v5blueskyer/ESP32_appcardV2/appcardV1.2程序固件及说明（最新）/appcardV1.2/Englishfy.h

 #include <pgmspace.h>
static const char *Englishfy[7990] PROGMEM ={"v.抛弃，放弃",
"n.放弃",
"n.缩写",
"n.缓办，中止",
"v.遵守",
"n.能力",
"adj.有能力的，能干的",
"adj.反常的，变态的",
"adv.船(车)上",
"v.废除，取消",
"n.废除，取消",
"n.流产",
"adj.无效果的，失败的",
"prep.关于，大约",
"prep.在...之上，高于",
"adj.上述的",
"adv.并肩，并列",
"v.省略，摘要",
"adv.国外，海外",
"v.取消，废除",
"n.取消，废除",
"adj.突然的，生硬的",
"adv.突然地",
"n.缺席，缺乏",
"adj.缺席的，不存在",
"adj.心不在焉的",
"adj.完全的，绝对的",
"adv.绝对，完全",
"v.吸收，专心于",
"n.吸收，专注",
"adj.抽象的，难懂的",
"n.抽象，提取",
"adj.荒唐的",
"n.荒唐(事)",
"n.丰富，大量",
"adj.丰富的，充裕的",
"v.滥用，谩骂",
"n.滥用",
"adj.学院的，学术的",
"n.学院，研究院",
"v.同意",
"v.加速，加快",
"v.加速，促进",
"n.腔调v.重读",
"v.接受，同意",
"adj.可接受的，合意的",
"n.接受，承兑",
"n.接近，入口",
"adj.可接近的",
"n.附件，装饰品",
"n.事故，意外之事",
"adj.意外的，偶然的",
"adv.偶尔，附带",
"v.提供便利，拆借",
"n.便利，通融",
"n.伴侣，伴奏",
"v.伴随，伴奏",
"v.完成，达到",
"n.成就",
"v.符合，协调",
"n.按照，与...一致",
"adj.按照，据...说",
"adj.相应地，从而",
"n.账目v.说明",
"n.会计(师)",
"n.会计学",
"v.产生，发生",
"adj.增值的，应计的",
"v.积累，积蓄",
"n.积累",
"adj.积累的",
"n.准确(性)",
"adj.准确的，精密的",
"adj.准确地",
"n.控告",
"v.告发，指责",
"v.使...习惯于",
"v.觉得疼n.疼痛",
"adj.疼痛的",
"v.完成，实现",
"n.完成，成就",
"n.酸",
"v.承认，鸣谢",
"n.承认，鸣谢，回执",
"n.使熟悉，相识",
"n.熟悉人，相识",
"adj.熟悉的",
"v.求得，获得",
"n.获得",
"n.英亩",
"n.杂技演员",
"n.杂技",
"prep.横越adv.横穿",
"n.行为，法令v.表演",
"n.行为，行动",
"v.使活跃，开动",
"adj.活跃的，积极的",
"adv.积极地，活跃地",
"n.活动",
"n.男演员",
"n.女演员",
"adj.现实的，实际的",
"n.实际",
"adv.实际上，居然",
"adj.剧烈的，敏锐的",
"(缩)公元",
"n.(缩)广告",
"v.使适应，改编",
"n.适应",
"v.增添，加，补充",
"n.增加，附加物",
"adj.增加的，附加的",
"adj.附加的n.添加剂",
"n.地址v.致词",
"adj.足够的，恰当的",
"adv.恰当地",
"v.粘附，坚持",
"n.粘合剂",
"adj.邻近的",
"n.形容词",
"v.毗连",
"v.调整，修整",
"adj.可调整的",
"n.调整",
"v.管理",
"n.行政管理，管理机关",
"adj.行政管理的",
"adj.可钦佩的",
"n.羡慕，钦佩",
"v.钦佩，赞美",
"n.准入，承认",
"v.承认，接纳",
"adv.明白地",
"n.青春期",
"adj.青春期的",
"v.采用，采纳",
"n.采用",
"v.崇拜，敬慕",
"v.装饰，佩带",
"n.装饰(品)",
"n.成年人adj.成年的",
"n.v.前进",
"adj.先进的，发达的",
"n.优点，优势",
"adj.有利的，有用的",
"n.冒险，惊险活动",
"adj.冒险的",
"n.副词",
"adj.副词的",
"adj.敌手，对手",
"v.逆的，相反的",
"n.逆境，不幸",
"v.登广告，推销",
"adj.广告的",
"n.广告",
"n.忠告，意见",
"adj.适当的，可行的",
"v.劝告，通知",
"n.顾问",
"v.拥护，提倡",
"adj.天空的，航空的",
"n.飞机",
"n.事件，事情",
"v.影响，改变",
"n.友爱，爱慕",
"adj.充满感情的",
"n.分号(公司)",
"v.断言，肯定",
"n.确定，确认",
"adj.肯定的",
"v.买得起，经受得起",
"adj.买得起的",
"adj.航行中的",
"adj.上述的",
"adj.害怕的，恐怕",
"n.非洲",
"adj.非洲的n.非洲人",
"prep.在...后",
"n.下午",
"adv.后来",
"adv.再，又",
"prep.反对，对着",
"n.年龄，时代",
"n.代理，代理处",
"n.代理人，试剂",
"v.加重，恶化",
"n.加重，恶化",
"v.n.adj.合计(的)",
"n.总计，集合",
"n.侵略",
"adj.侵略的，进取的",
"n.侵略者",
"v.鼓动",
"n.鼓动，不安",
"adv....以前",
"v.使痛苦",
"n.苦恼，痛苦",
"v.同意，一致认为",
"adj.惬意的，易相处的",
"adv.欣然，依照",
"adj.商定的",
"n.一致，协议",
"adj.农业的",
"n.农业",
"adv.在...前",
"n.v.援助，救护",
"n.(缩)艾滋病",
"n.疾病",
"n.目的v.旨在，指向",
"adj.无目的的",
"n.空气，气派",
"n.航空器",
"n.航线，航空公司",
"n.定期航班",
"n.航空邮件",
"n.飞机",
"n.机场",
"n.航线",
"n.过道，走廊",
"adv.半开的",
"n.惊慌，警报",
"adj.警告的",
"int.唉，哎呀",
"n.相册，地图册",
"n.酒精",
"adj.含酒精的",
"n.嗜酒者，酒鬼",
"n.淡啤酒",
"adj.警惕的，灵活的",
"n.代数",
"adj.异国的，异样的",
"v.疏远，转让，挪用",
"n.异化",
"n.对准，准线",
"adj.相象的",
"adj.活着的，有生命的",
"adj.所有的n.一切",
"adj.过敏的，变态的",
"n.反感，过敏",
"n.联合，同盟",
"adj.同盟的",
"v.分配",
"n.分配",
"v.分配，配给",
"n.分配，份额",
"v.允许，许可",
"n.补助，津贴",
"n.合金",
"n.同盟者v.结盟",
"adv.几乎，差不多",
"adj.单独的，仅仅",
"prep.沿着adv.一起",
"prep.在...旁边",
"adv.大声地",
"n.字母表",
"adv.也",
"v.改变，变动",
"v.轮流，交替",
"n.改变，变更",
"n.v.两者取一",
"conj.虽然",
"n.高度",
"adv.全部地，总共",
"n.铝",
"adv.总是，始终",
"(缩)上午",
"adj.业余的",
"v.使惊叹",
"n.惊奇，诧异",
"n.大使",
"adj.周围的，包围着的",
"n.歧义性，意义不明处",
"adj.模棱两可的",
"n.抱负，野心",
"adj.雄心勃勃的",
"n.救护车",
"v.修改，更正",
"n.修改(通知书)",
"n.赔偿",
"n.美国，美洲",
"adj.美国的n.美国人",
"adj.和蔼的，亲切的",
"adj.友好的，和睦的",
"prep.在...之间",
"n.弹药",
"prep.在...之中",
"n.数量，总数v.合计",
"n.【电】安培",
"adj.宽大的，充裕的",
"n.放大",
"n.放大器，扩音机",
"v.详述，放大",
"v.逗乐，给娱乐",
"n.娱乐，乐趣",
"n.模拟，类似物",
"n.类似，类推",
"n.分析，分解",
"adj.分析的，解析的",
"v.分析，分解",
"n.祖先，祖宗",
"n.锚v.停泊",
"adj.古老的，古代的",
"conj.和，与，而",
"n.轶事，轶闻",
"n.天命，安琪儿",
"n.生气，愤怒",
"n.角，角度",
"adj.生气的，愤怒的",
"adj.角状的",
"n.动物",
"v.使有活力，激活",
"n.生气，生机",
"n.踝，踝骨",
"n.附录，附件",
"n.周年纪念日",
"v.宣布，通报",
"n.通知",
"n.播音员",
"v.烦扰，使生气",
"n.烦恼，麻烦事",
"adj.每年的，年度的",
"adv.每年，年年",
"pron.prep.另一个",
"n.答案v.答复",
"n.蚂蚁",
"n.对立，敌对",
"n.对手，敌手",
"adj.南极的",
"adj.抗菌的",
"n.触角，天线",
"v.期望，预料",
"n.期望，预料",
"adj.古老的n.古玩",
"n.反义词",
"adj.反义的",
"n.焦虑，担心",
"adj.焦急的，切盼的",
"adv.焦急地，急切地",
"adj.任何，一些",
"pron.任何人",
"adv.无论如何",
"pron.无论谁",
"pron.无论什么",
"adv.不管怎样",
"adv.无论何地",
"adv.分离，隔开",
"n.套房，公寓",
"n.猿猴",
"v.道歉",
"n.道歉",
"n.仪器，设备",
"adj.明显的，表面上的",
"adj.显然，似乎",
"v.n.呼吁，上诉",
"adj.有吸引力的",
"v.出现，好象",
"n.出现，外表",
"n.附录，盲肠",
"n.食欲，欲望",
"v.称赞，拍手喝彩",
"n.喝彩，欢呼",
"n.苹果",
"n.用具，器械",
"adj.生动的，适用的",
"n.申请人",
"n.申请，应用",
"v.应用，申请",
"v.任命，约定",
"n.任命，约会",
"adj.可看到的",
"adv.相当大地",
"v.欣赏，感激",
"n.欣赏，感激",
"adj.感激的",
"n.学校",
"v.通知",
"v.接近n.途径",
"adj.恰当的v.拨给",
"n.同意，批准",
"v.赞成，批准",
"adj.v.近似，约略",
"adv.近乎，大约",
"n.近似值",
"n.四月",
"adj.恰当的，易于..的",
"n.才智，天资",
"n.阿拉伯",
"n.阿拉伯人，阿拉伯语",
"adj.阿拉伯的",
"adj.专横的，任意的",
"v.仲裁",
"n.仲裁",
"n.仲裁员",
"n.弧",
"n.拱门，弓形",
"n.考古学家",
"n.考古学",
"n.建筑师",
"n.建筑学",
"adj.北极的",
"adj.热心的，强烈的",
"adj.艰巨的，努力的",
"n.地区，面积，领域",
"n.竞技场",
"v.争论，辩论",
"n.争论，论点",
"v.起来，出现",
"n.贵族阶层",
"n.贵族",
"adj.贵族的",
"n.算术",
"n.手臂，扶手v.武装",
"n.武器",
"n.手扶椅",
"n.盔甲，装甲",
"n.军队，陆军",
"adv.在周围，大约",
"v.唤醒，唤起",
"v.整理，安排",
"n.安排，计划",
"v.装扮，排列",
"n.欠款",
"v.逮捕，吸引",
"n.到达，到货",
"v.到达，达到",
"n.傲慢",
"adj.傲慢的",
"adv.傲慢地",
"n.箭，箭头",
"n.艺术，技艺",
"n.文章，物品，冠词",
"adj.人造的，假的",
"n.艺术家",
"n.艺术的",
"adv.一样prep.作为",
"v.登，上升",
"v.查明，弄清",
"v.归于",
"n.(缩)东盟",
"n.灰，灰烬",
"adj.惭愧的，羞耻的",
"adv.在岸上，上岸",
"n.烟灰缸",
"n.亚洲",
"adj.亚洲的n.亚洲人",
"adv.在旁边，搁在一边",
"v.问，要求，邀请",
"adj.睡着的",
"n.容貌，方面",
"n.阿斯匹林",
"n.驴，愚蠢的人",
"v.暗杀",
"n.暗杀",
"n.暗杀者",
"v.袭击，攻击",
"v.集合，装配",
"n.集合，装配",
"v.断言，宣称",
"n.断言",
"v.评定，估价",
"n.估值，评价",
"v.分配，指定",
"n.任务，作业",
"v.协助",
"n.协助，辅助",
"n.助手",
"v.联想adv.副的",
"adj.联合的",
"n.协会，合营",
"adj.联想的",
"adj.各种各样的",
"n.花色品种",
"v.假定，担任",
"n.假定，假装",
"n.自信，保证",
"v.使..放心，向..保证",
"adj.感到放心的",
"v.使惊讶",
"n.惊讶",
"v.使惊讶",
"adv.(信件)遗失、误传",
"n.宇宙飞行员",
"n.天文学家",
"adj.天文学的",
"n.天文学",
"prep.在，处于，以",
"n.田径运动员",
"adj.田径的",
"n.adj.大西洋(的)",
"n.地图集",
"n.大气，气氛",
"adj.大气的，空气的",
"n.原子，微粒",
"adj.原子的，原子能的",
"v.附着于，依恋",
"n.依附，附件，爱慕",
"v.n.进攻，侵袭",
"v.赢得，到达",
"v.n.尝试，企图",
"v.出席，照顾",
"n.出勤(率)，出席",
"n.随从，服务员",
"n.注意，关心",
"adj.注意的，关心的",
"adv.关心地",
"n.阁楼",
"n.态度，看法",
"n.辩护律师",
"v.吸引，引力",
"adj.有吸引力的",
"adj.归于...的",
"v.属于n.属性",
"n.属于",
"adj.定语的，属性的",
"n.拍卖",
"n.听众，观众",
"n.礼堂",
"n.八月",
"n.伯(婶、姨、姑)母",
"adj.听觉的，耳的",
"n.赞助，主办",
"n.澳大利亚",
"adj.澳大利亚的",
"n.作者，创造者",
"n.权力，权威",
"n.授权",
"v.授权，批准",
"n.自传",
"v.自动化",
"adj.自动的",
"n.自动化",
"n.汽车",
"adj.自治的",
"n.自治",
"n.秋天",
"adj.辅助的，补助的",
"v.帮助，有用n.效用",
"n.可用性，可供货",
"adj.可得到的",
"v.报复",
"n.林荫道，途径",
"adj.平均的n.平均数",
"adv.平均",
"n.航空",
"v.避免，逃避",
"v.等候，等待",
"v.醒来醒悟adj.醒的",
"adj.醒着的",
"v.授予n.奖，奖品",
"adj.知道的，意识到的",
"adv.去，远离，在远处",
"n.威惧",
"adj.可怕的",
"adj.令人畏惧的",
"adv.可怕地，非常",
"adj.笨拙的，不熟练的",
"adv.笨拙地",
"n.笨拙",
"n.斧子",
"adj.轴的，轴向的",
"n.轴，轴线，轴心",
"n.(轮)轴",
"n.婴儿，年龄最小的人",
"v.(替人)看护小孩",
"n.看护小孩的人",
"n.单身汉，学士",
"n.背adj.背后的",
"n.脊梁骨",
"v.回溯",
"n.背景，经历",
"n.倒退，支持物",
"n.未交付的订货",
"adv.向后，逆",
"n.落后(状态)",
"n.咸肉，熏肉",
"n.细菌",
"adj.坏的，低劣的",
"n.徽章",
"adv.坏，非常，严重地",
"n.羽毛球",
"v.困扰，难倒",
"n.袋子，提包",
"n.行李",
"adj.袋状的",
"n.饵，诱饵",
"v.烤，烘",
"n.面包师",
"n.面包店",
"n.平衡，天平，余额",
"n.阳台",
"adj.秃的",
"n.球，球状物，舞会",
"n.芭蕾舞",
"n.气球",
"n.热气球飞行运动",
"penn.圆珠笔",
"n.舞厅",
"n.竹",
"n.竹笋",
"n.香蕉",
"n.乐队，带子v.联合",
"n.绷带",
"n.盗匪，歹徒",
"n.v.砰的一响",
"n.岸，银行",
"n.银行家",
"n.银行业务、金融业",
"n.v.adj.破产",
"n.旗帜，横幅",
"n.宴会",
"n.棒，杆，酒吧",
"n.理发师",
"adj.裸的，直率的",
"adv.赤裸裸地",
"n.交易，便宜货",
"n.驳船",
"n.狗吠，树皮v.吠",
"n.谷仓，牲口棚",
"n.晴雨表，标记",
"n.男爵",
"n.男爵夫人，女男爵",
"n.桶，枪(炮)管",
"adj.不育的，贫瘠的",
"n.障碍，壁垒",
"n.易货贸易",
"n.基础，基地v.基于",
"n.棒球",
"n.地下室，地窖",
"adj.基本的，基础的",
"adv.基本上，主要地",
"n.盆，盆地",
"n.基础，根据",
"n.篮子，筐",
"n.篮球",
"n.球拍，蝙蝠v.击打",
"n.洗澡，浴室",
"v.洗澡，冲洗",
"n.浴室，洗手间",
"v.打击",
"n.电池",
"n.战斗，战役",
"n.海湾，湾",
"n.集市",
"(缩)公元前",
"v.是，存在",
"n.海滩，湖滨",
"n.有孔小珠",
"n.鸟嘴",
"n.梁，射线v.发光",
"n.豆子",
"v.负担，忍受，生育",
"n.举止，意义，轴承",
"adj.熊市的",
"n.野兽，牲畜",
"v.打，击败n.击打",
"adj.美丽的，绝妙的",
"n.美，美女",
"conj.因为，由于",
"v.变成",
"n.床，河床，苗圃",
"n.卧室",
"n.蜜蜂",
"n.牛肉",
"n.啤酒",
"n.甲虫",
"prep.在...前面",
"adv.事先，预先",
"v.乞讨，恳求",
"n.乞丐",
"v.开始，着手进行",
"n.初学者",
"n.开端，起点",
"n.代表",
"v.行为，举动",
"n.行为，举止",
"prep.在...后面",
"adj.落后，事后",
"n.生物，存在",
"n.信仰，信心",
"v.相信，认为",
"n.钟，铃",
"n.肚子",
"v.属于",
"adj.敬爱的n.爱人",
"adj.prep.在...下面",
"n.带，腰带",
"n.长凳，工作台",
"v.弯曲，俯身n.拐弯",
"prep.在...之下",
"adj.有益的，有利的",
"n.受益者",
"n.益处，利益",
"n.慈悲，捐助",
"adj.乐善好施的",
"adj.弯曲的",
"n.浆果",
"prep.在...之旁",
"adj.而且prep...之外",
"adj.最好的",
"n.畅销书(货)",
"adj.畅销的",
"v.赠给，授予",
"n.v.打赌",
"v.背叛，泄露",
"n.背叛，暴露",
"adj.更好的adv.较好",
"adj.经济情况较好的",
"prep.在两者之间",
"n.饮料",
"v.当心",
"v.迷惑，茫然",
"prep.在...那边，超出",
"n.偏好",
"n.圣经",
"n.自行车",
"n.v.报价，投标",
"n.投标",
"adj.大的，重大的",
"n.自行车",
"n.帐单，议案，钞票",
"n.十亿",
"v.捆绑，约束",
"n.装订",
"n.传记记者",
"n.传记",
"n.生物学家",
"n.生物学",
"n.鸟",
"n.出生，创始",
"n.生日，诞辰",
"n.出生地",
"n.饼干",
"n.主教",
"n.小片，一点",
"n.v.咬，叮n.一口",
"adj.苦的，痛苦的",
"adv.惨痛地，辛酸地",
"n.苦味，苦难",
"n.(缩)提单",
"adj.黑的n.黑色",
"n.黑板",
"n.铁匠",
"n.刀刃，叶片",
"v.责备n.过失",
"adj.空白的n.空格",
"n.毛毯",
"n.阵风v.爆炸",
"n.火光，光亮",
"v.漂白，变白",
"v.出血，流血",
"v.混合，掺混",
"v.保佑，祝福",
"n.祝福",
"adj.瞎的v.使失明",
"adj.眨眼，闪烁",
"n.大块，街区，障碍物",
"n.封锁",
"adj.金发的",
"n.血，血统",
"adj.流血的，残忍的",
"n.花v.开花",
"n.(果树的)花",
"n.污迹",
"n.女衫",
"v.吹，吹掉，刮风",
"adj.蓝色的，忧郁的",
"n.大错",
"adj.钝的，生硬的",
"v.脸红，害臊",
"adj.害羞的",
"n.木板，伙食，董事会",
"n.伙食",
"v.夸口，以...而自豪",
"n.小船，艇",
"n.身体，尸体，团体",
"n.保镖",
"v.沸腾，煮沸",
"n.锅炉",
"adj.沸腾的",
"adj.大胆的",
"n.胆略",
"n.螺检，插销v.闩门",
"n.炸弹v.轰炸",
"n.轰炸机",
"adj.真诚的，无欺的",
"n.束缚，联结，债券",
"adj.保税的",
"n.骨，骨骼",
"adj.骨头的",
"n.红利",
"n.书v.预订(票)",
"adj.定货",
"n.小册子",
"n.书橱",
"n.书架",
"n.书店",
"v.隆隆响，兴旺，繁荣",
"adj.兴旺的，繁荣的",
"v.抬高，促进",
"n.靴子",
"n.货摊，电话亭",
"n.国界，边境",
"v.烦扰，使厌烦，钻孔",
"adj.讨厌的",
"adj.出生的，天生的",
"v.借，借用",
"n.借款",
"n.X，X怀",
"n.上司，老板",
"adj.好发号施令的",
"pron.adj.双方，两",
"v.打扰，麻烦n.麻烦",
"n.瓶子",
"n.影响...的环节",
"n.底部，末尾",
"n.末行数字，结果",
"n.大树枝",
"v.跳起n.跳跃",
"v.缚，以...为界",
"n.界线，边界",
"n.资产阶级分子",
"v.鞠躬，服从n.弓",
"n.碗，钵",
"n.保龄球",
"n.箱，盒v.拳击",
"n.拳击运动员",
"n.拳击",
"n.节礼日",
"n.男孩，小伙子",
"v.n.抵制",
"n.支撑v.激励",
"n.括号",
"v.吹嘘，夸口",
"n.脑子，头脑，智能",
"n.制动器v.刹车",
"n.树枝，分支，分部",
"n.牌子，商标",
"n.白兰地",
"n.黄铜",
"adj.勇敢的v.冒着",
"adv.勇敢地",
"n.勇敢",
"n.巴西",
"adj.n.巴西的(人)",
"n.违反(契约)",
"n.面包，生计",
"n.挣钱养家的人",
"n.宽度，大量",
"n.打破，破坏n.裂口",
"n.裂口",
"n.故障，衰竭",
"n.突破",
"n.早饭",
"n.ru房，X脯",
"n.呼吸，气息",
"v.呼吸",
"v.繁殖，饲养n.品种",
"n.微风",
"v.贿赂",
"v.贿赂",
"n.砖",
"n.新娘",
"n.新郎",
"n.桥梁，桥牌",
"n.约束v.抑制",
"adj.简短的",
"n.简要情况",
"adv.简单地，简短地",
"adj.明亮的，鲜明的",
"v.使发光",
"n.光辉，明亮",
"n.辉煌，光彩",
"v.辉煌的，杰出的",
"n.边，边缘",
"v.拿来，带来",
"n.边缘",
"adj.敏捷的，活跃的",
"n.鬃毛",
"n.不列颠，英国",
"adj.英国的，英属的",
"adj.易碎的，脆的",
"adj.宽的，辽阔的",
"v.n.广播",
"n.广播节目",
"v.加宽，扩大",
"n.产品介绍手册",
"adj.破碎的，毁坏了的",
"n.经纪人",
"n.青铜",
"n.一窝",
"n.小河，溪流",
"n.扫帚",
"n.兄弟，同胞",
"n.兄弟情谊",
"n.姻兄(弟)",
"n.眉毛，额",
"n.adj.褐色(的)",
"n.青肿v.打伤",
"n.刷子，画笔v.刷",
"adj.野蛮的",
"n.禽兽，畜生",
"n.气泡",
"n.水桶",
"n.芽，蓓蕾",
"n.佛教",
"n.佛教徒",
"n.预算",
"n.水牛，野牛",
"n.冷餐",
"n.臭虫，虫子",
"n.喇叭",
"v.建造，建设",
"n.建筑工人，建设者",
"n.建筑物，大楼",
"n.球形物，灯泡",
"n.体积，大半",
"adj.庞大的，笨重的",
"n.公牛",
"n.子弹",
"n.公报",
"n.金块，金条",
"adj.行情看涨的",
"v.碰，颠簸n.碰撞",
"adj.颠簸不平的",
"n.一束",
"n.v.捆，包",
"n.担子，负担",
"adj.沉重的",
"n.局，司，办公室",
"n.官僚主义",
"adj.官僚主义的",
"n.夜盗，窃贼",
"n.盗窃",
"n.埋葬",
"v.烧，燃烧，烧伤",
"n.喷灯",
"adj.烧焦的，烧坏的",
"v.n.爆炸，破裂",
"v.掩埋，安葬",
"n.公共汽车",
"n.灌木",
"n.蒲式耳(重量单位)",
"n.行业，买卖，商号",
"adj.事务式的",
"adj.忙碌的，热闹的",
"prep.但是，除了",
"n.屠夫v.屠宰",
"n.肉食店",
"n.根端v.顶撞",
"n.黄油",
"n.蝴蝶",
"n.钮扣，按钮",
"v.买，购买",
"n.购买者",
"v.嗡嗡叫n.嗡嗡声",
"prep.在...旁边，按照",
"n.已往的，过时的",
"n.旁道，分路",
"n.副产品",
"n.出租汽车",
"n.卷心菜；圆白菜",
"n.小屋，船舱",
"n.橱柜，内阁",
"n.电缆，海底电报",
"n.咖啡馆",
"n.自助餐厅",
"n.笼子，鸟笼",
"n.糕，饼",
"v.计算，估计",
"n.计算(结果)",
"n.微积分",
"n.日历",
"n.小牛，腿肚子",
"n.刻度，核定",
"v.叫，称为，打电话",
"adj.宁静的，镇静的",
"adv.平静地，沉着地",
"n.热卡，卡路里",
"n.骆驼",
"n.照相机",
"n.帐篷，野营n.宿营",
"n.战役，运动",
"n.野营",
"n.校园",
"v.aux.能，会，可以",
"n.加拿大",
"adj.n.加拿大的(人)",
"n.运河，渠道",
"n.金丝雀",
"v.删除，取消",
"n.删除，取消",
"n.癌",
"adj.坦白的，直率的",
"n.候选人",
"n.蜡烛",
"n.糖果",
"n.手杖，(藤、竹的)茎",
"adj.罐装的",
"n.大炮",
"n.独木舟，游艇",
"n.规范，准则",
"n.食堂",
"n.帆布，画布",
"v.游说",
"n.帽子，盖子v.覆盖",
"n.才能，能力",
"adj.有能力的",
"n.容量，容积，资格",
"n.披肩，岬，海角",
"n.人",
"n.首都，资本",
"adj.资本密集型的",
"n.资本主义",
"adj.资本主义的",
"n.资本化",
"v.大写，资本化",
"n.队长，船长，上尉",
"n.标题",
"adj.被俘虏的n.俘虏",
"v.n.俘获，捉拿",
"n.小汽车",
"n.车队，大蓬车",
"n.碳，复写纸",
"n.卡片，纸牌，名片",
"n.硬纸板",
"adj.主要的",
"n.注意，小心v.关心",
"n.职业，生涯",
"adj.小心的，仔细的",
"adj.粗心的，不关心的",
"n.粗心",
"n.货物",
"n.颂歌",
"n.木匠",
"n.地毯",
"n.马车，(火车)车厢",
"n.运载工具，媒介",
"n.胡萝卜",
"v.搬运，携带",
"n.手推车",
"n.纸箱",
"n.漫画，动画片",
"n.弹仓",
"v.雕刻，切",
"n.雕塑",
"n.事实，案例，箱子",
"n.现金v.兑现",
"n.出纳",
"n.小盒，磁盘盒",
"v.掷，投射，铸造",
"n.城堡",
"adj.偶然的，随便的",
"n.伤亡",
"n.猫",
"n.(商品)目录",
"n.灾难",
"n.催化剂",
"v.捕获，染病n.捉",
"n.种类，范畴",
"v.提供",
"n.大教堂",
"adj.天主教的",
"n.牛(总称)",
"n.原因，理由，事业",
"n.谨慎，告诫",
"adj.谨慎的，当心的",
"n.骑兵，马术",
"n.洞穴，山洞",
"n.酒馆",
"n.坑，孔穴",
"v.停止，平息",
"n.天花板",
"v.庆祝",
"n.庆祝仪式",
"n.芹菜",
"n.细胞，牢房，电池",
"n.地窖，地下室",
"n.水泥",
"n.墓场",
"v.审查",
"n.审查",
"n.分币",
"adj.摄氏的",
"n.厘米",
"adj.中心的，中央的",
"n.中心v.集中",
"n.世纪",
"n.谷物",
"adj.仪式的",
"n.仪式，典礼，礼节",
"adj.确信的，一定的",
"adv.一定，当然，行",
"n.确实，必然的事",
"n.证书，执照",
"n.证明",
"v.证明",
"n.链条，一系列，锁链",
"n.椅子",
"n.主席，董事长",
"n.主席(无性别之分)",
"n.女主席，女董事长",
"n.白垩，粉笔",
"n.v.挑战，质问",
"adj.具有挑战性的",
"n.房间",
"n.优胜者，冠军",
"n.锦标(赛)",
"n.机会，可能性",
"n.变化，零钱v.改变",
"adj.变化的",
"n.沟渠，途径，频道",
"n.混乱",
"n.伙计",
"n.章，节",
"n.性格，角色，特牲",
"n.特征，特性",
"adj....特征的",
"v.具有...特征",
"n.木炭",
"v.收费，冲向，控告",
"n.施舍，仁慈",
"n.魅力v.迷惑",
"adj.迷人的",
"n.图表v.制定计划",
"n.特许证，宪章",
"v.追逐，驱除",
"v.聊天",
"v.喋喋不休，啁啾",
"adj.便宜的，可鄙的",
"v.欺骗，作弊n.骗子",
"n.欺骗行为",
"v.检验，核对n.支票",
"n.结帐，离店时限",
"n.核对，检查",
"n.颊，脸",
"adj.胖乎乎的",
"n.喝彩v.向...喝彩",
"adj.快活的",
"n.干酪，奶酪",
"adj.化学的",
"n.化学家，药剂师",
"n.化学",
"n.支票",
"v.珍爱，怀有",
"n.樱桃",
"n.国际象棋",
"n.X膛，柜子",
"n.栗树，栗子",
"v.咀嚼",
"n.小鸡",
"n.鸡，鸡肉",
"adj.首席的，首要的",
"adv.多半，首要地",
"n.孩子，儿童",
"n.童年",
"adj.孩子气的",
"adj.孩子似的，天真的",
"n.寒意v.冷却",
"adj.凉的，冷淡的",
"n.烟囱",
"n.下巴，下颊",
"n.中国",
"n.瓷器，陶瓷",
"adj.n.中国的",
"n.片，屑，缺口",
"n.巧克力",
"n.选择，选中的人或物",
"v.闷死，窒息，阻塞",
"v.选择，愿意",
"v.劈，剁n.带骨肉",
"n.合唱队，齐声",
"n.基督",
"adj.基督教的n.基督徒",
"n.基督教(精神)",
"n.圣诞节",
"n.教堂",
"n.(缩)到岸价",
"n.雪茄",
"n.卷烟",
"n.电影院",
"n.圆，果v.画圈于",
"adj.圆圈的",
"n.巡回，电路",
"v.循环，流通，流传",
"n.循环，销路，周转",
"n.周围，圆周",
"n.情况，环境",
"n.马戏团",
"v.引证，举例",
"n.公民，市民",
"n.公民权",
"n.城市",
"adj.民用的，民事的",
"n.文明，民族文化",
"v.使...文明，开化",
"v.要求，索赔，声称",
"n.夹子v.夹紧",
"v.排手，鼓掌",
"v.弄清(问题)",
"n.澄清",
"v.n.碰撞，冲突",
"n.扣子v.紧握(抱)",
"n.阶级，种类，班级",
"n.经典作品",
"adj.经典的，古典的",
"n.分类",
"v.分类，分等",
"n.同班同学",
"n.教室",
"v.咔嗒响n.卡嗒响",
"n.条款，从句",
"n.爪",
"n.黏土",
"adj.清洁的，干的",
"adj.清楚的，明确的",
"n.结关",
"adv.清晰地，无疑地",
"v.咬紧，握紧，决定",
"n.办事员，职员，店员",
"adj.聪明的，灵巧的",
"n.聪明，机灵",
"n.当事人，顾客，用户",
"n.顾客(总称)",
"n.悬崖，峭壁",
"n.气候",
"n.顶点，高潮",
"v.爬，攀登，上升",
"v.粘住，依附",
"n.诊所",
"n.夹子，卡子v.夹住",
"n.外套，借口",
"n.时钟",
"adj.adv.顺时针的",
"v.关闭，结束n.终结",
"adj.关闭的，停业的",
"n.倒闭",
"adv.紧密地，严密地",
"n.壁橱",
"n.织物，布，衣料",
"v.给...着衣",
"n.衣服(总称)",
"n.服装(总称)",
"n.云",
"adj.多云的",
"n.小丑，丑角",
"n.俱乐部，会，棍棒",
"n.线索",
"adj.笨拙的，愚蠢的",
"n.群，串",
"v.n.抓紧",
"v.(缩)请转交...",
"n.客车，教练",
"n.煤",
"adj.粗糙的，粗的",
"n.海岸，海滨",
"adj.沿海的",
"n.上衣，涂层",
"n.公鸡",
"n.鸡尾酒",
"n.法规，代码，密码",
"v.编码",
"n.系数",
"n.咖啡",
"n.棺材",
"n.凝聚性",
"adj.有条理的，粘着的",
"n.凝聚力，团结",
"adj.有粘性的",
"v.卷曲n.一卷，线圈",
"n.硬币，创造新词",
"v.重合，一致",
"n.巧合，同时发生",
"adj.同时发生的",
"adj.冷，冷冰冰的",
"n.寒冷，冷淡",
"v.协作，勾结",
"n.协作，通敌",
"v.倒塌v.坍塌",
"n.领子",
"n.同事，同行",
"v.收集，征收，聚集",
"n.收集，收藏",
"n.集体adj.集体的",
"n.学院",
"v.猛烈碰撞，冲突",
"n.猛烈碰拉，冲突",
"n.上校",
"adj.殖民的，殖民地的",
"n.殖民者，移民",
"n.殖民主义",
"n.殖民地",
"n.颜色，色彩，气色",
"adj.色盲的",
"adj.色彩丰富的",
"adj.无色的",
"n.圆柱，栏",
"n.专栏作家",
"v.梳n.梳子",
"v.n.战斗，斗争",
"n.混合，组合",
"v.组合，化合，结合",
"v.来到，出现，发生",
"n.喜剧演员",
"n.喜剧",
"n.舒适，慰藉v.安慰",
"adj.舒适的，自在的",
"adj.喜剧的，滑稽的",
"v.n.命令，控制",
"n.司令，指挥官",
"n.纪念",
"v.纪念",
"v.开始",
"v.称赞，推荐",
"n.称赞",
"n.v.评论",
"n.商业",
"adj.商业的，商务的",
"n.v.委托，委任",
"v.委托，犯(错误)",
"n.责任",
"n.委员会",
"n.商品",
"adj.共同的，普通的",
"adv.通常，平常",
"adj.平凡的，平淡的",
"n.常识",
"n.共同体，联邦",
"n.公社",
"v.传播，通讯",
"n.通信，通讯系统",
"adj.通讯的",
"n.共产主义",
"n.共产主义者",
"n.团体，共同体，群体",
"adj.严密的，紧凑的",
"n.同伴，伴侣",
"n.公司，同伴",
"adj.可比较的",
"adj.比较的，相当的",
"adv.比较地",
"v.比较，比作",
"n.比较",
"n.指南针，圆规",
"adj.可兼容的，一致的",
"v.强迫，逼迫",
"v.赔偿，补偿，酬报",
"n.赔偿，补偿",
"v.竞争，比赛",
"adj.称职的，有能力的",
"n.竞争，比赛",
"adj.竞争的",
"n.竞争能力",
"n.竞争者，对手",
"v.编(书)，编辑",
"v.抱怨，控诉",
"n.怨言，控告",
"n.补充，余数",
"v.完成，结束",
"adv.完全地，十分",
"n.完成，完满",
"adj.综合的，复杂的",
"n.复杂性",
"n.顺从，应允",
"v.使复杂",
"adj.错综复杂的",
"n.v.称赞，问候",
"adj.称赞的",
"v.履行，遵守",
"n.成分，组分",
"adj.成分的",
"v.由...组成，作曲",
"adj.镇静的",
"n.作曲家",
"adj.合成的，组合的",
"n.作文，组成",
"n.化合物v.混合",
"v.理解，了解",
"n.理解",
"adj.综合的，广泛的",
"v.压缩",
"n.压缩，凝缩",
"v.包括，由...组成",
"n.v.妥协，和解",
"v.强迫",
"adj.强制的，必修的",
"n.计算",
"v.计算",
"n.计算机",
"n.计算机化",
"v.使...计算机化",
"n.同志",
"v.隐瞒，隐藏",
"v.让步，输",
"n.自负，自大",
"adj.自负的",
"v.想象，怀孕",
"v.集中，浓缩",
"adj.全神贯注的",
"n.专心，浓度",
"n.概念",
"n.想法，概念",
"adj.概念的",
"v.涉及，关心n.商行",
"adj.有关的",
"prep.关于",
"n.音乐会",
"adj.齐心协力的",
"v.让步",
"n.让步，减免，租界",
"adj.简明的，简要的",
"v.结束，缔结，断定",
"n.结束，结论",
"adj.结束的，结论性的",
"n.混凝土adj.具体的",
"v.同地发生",
"n.合作，并发",
"adj.同时发生的",
"v.谴责，判刑",
"n.谴责，判决",
"n.凝聚",
"v.凝结，冷凝，精简",
"n.冷凝器，聚光器",
"n.状态，情形，条件",
"adj.有条件的",
"v.导致，有益于",
"adj.有助于...的",
"n.行为，管理v.为人",
"n.传导，传热",
"n.(乐队)指挥，售票员",
"n.锥体，锥形",
"v.授予，颁布，商议",
"n.会议",
"v.坦白，供认",
"n.供认，自由",
"v.委托，吐露秘密",
"n.信任，信心",
"adj.确信的，自信的",
"adj.机密的",
"v.限制",
"n.限制",
"v.证实，确认，批准",
"n.确认",
"v.n.冲突，斗争",
"v.遵守，使...一致",
"n.遵照，一致",
"v.面对，与...相对",
"n.面对，对峙",
"v.混淆，弄糊涂，搅乱",
"n.混乱，糊涂",
"n.阻塞，消化不良",
"v.祝贺",
"n.祝贺，贺辞",
"n.(代表)大会，国会",
"n.国会议员",
"n.连词，联结",
"v.连接，联想",
"n.联系，社会关系",
"v.征服，战胜",
"n.征服者，胜利者",
"n.征服",
"n.良心，良知",
"adj.有良心的",
"adv.认真地",
"adj.意识到的，自觉的",
"n.知觉，意识",
"adj.连续的，连贯的",
"v.n.同意，允许",
"n.后果，重要性",
"adv.因而，所以",
"n.保护，保存",
"adj.保守的，稳健的",
"v.考虑，以为，体谅",
"adj.相当的，可观的",
"adv.相当",
"adj.考虑周全的",
"n.考虑，照顾",
"v.委托，托运货物",
"n.委托，货物",
"v.由...组成",
"n.一致(性)",
"adj.始终如一的，符合",
"v.安慰",
"v.团结",
"adj.加固的，统一的",
"n.团结",
"adj.响亮的",
"adj.显眼的，出众的",
"n.阴谋",
"adv.警官",
"adj.不变的，恒定的",
"adv.经常地",
"adj.组成的n.成分",
"v.组成，构成，设立",
"n.宪法，章程",
"adj.宪法的，章程的",
"n.强制，拘束",
"v.建设，建立",
"n.建设，建筑",
"v.翻译，解释",
"n.领事",
"n.领事馆",
"v.咨询，磋商",
"n.咨询顾问(公司)",
"n.咨询",
"v.消费，消耗",
"n.消费者，用户",
"n.消费，消耗量",
"n.v.接触，联系",
"v.含有，容纳，抑制",
"n.容器，集装箱",
"v.沉思",
"n.苦思冥想",
"n.同时代人",
"adj.当代的，同时代的",
"n.轻视，蔑视",
"adj.轻视的",
"n.含量，内容v.满足",
"n.v.争夺，比赛",
"n.参赛人",
"n.上下文，语境，环境",
"adj.上下文的，环境的",
"adj.节制的n.大陆",
"adj.大陆的",
"n.事故，意外",
"adj.连续的，频繁的",
"n.连续",
"v.继续，连续，依旧",
"adj.持续的，不断的",
"adv.连续不断地",
"n.契约，合同v.订",
"adj.合同所规定的",
"adj.合同的，契约的",
"v.反驳，与...矛盾",
"n.矛盾，反驳",
"adj.相反的n.反面",
"n.v.对照，对比",
"v.捐献，贡献，投稿",
"n.贡献，捐献物",
"v.n.控制，管理",
"n.论战，论争",
"adj.有争议的",
"n.方便，便利",
"adj.便利的，方便的",
"n.大会，协定，惯例",
"adj.传统的，常规的",
"adj.精通的，有交情的",
"n.会话，谈话",
"v.谈话，对话，交往",
"adv.相反地",
"n.转变，转化，换算",
"v.转换，改变信仰",
"v.运输，传达",
"n.运送，传达",
"n.罪犯",
"n.定罪，确信",
"v.使...确信，信服",
"adj.信服的",
"v.烹调，烧n.厨师",
"n.厨具，厨灶",
"adj.凉的，冷静的",
"n.凉爽，冷淡",
"v.合作，协作",
"n.合作，协作",
"adj.合作的n.合作社",
"v.协调，配合",
"n.协调，配合",
"v.应付，对付",
"n.铜",
"v.抄写，复制n.副本",
"n.细绳，电线",
"adj.诚恳的，亲切的",
"adv.亲切地",
"n.核，核心",
"n.软木塞",
"n.谷物，玉米",
"n.角落，拐角",
"n.有限公司",
"n.公司",
"adj.正确的，恰当的",
"n.修改，校正",
"adv.正确地",
"v.相关，关联",
"n.相互关系",
"v.符合，通信，相当于",
"n.相应，通信",
"adj.对应的n.记者",
"adj.相应的，通信的",
"n.走廓",
"v.腐蚀",
"n.腐蚀",
"adj.腐败的，腐化的",
"n.腐败，腐化",
"n.化妆品",
"adj.宇宙的",
"n.宇宙",
"n.大都市",
"n.成本，费用v.花费",
"adj.昂贵的",
"n.村舍",
"n.棉花，棉布，棉纱",
"n.躺椅",
"v.n.咳嗽",
"n.理事会，委员会",
"n.劝告，辩护律师",
"n.顾问",
"v.计算，数，认为",
"adj.可计算的",
"n.容貌，支持",
"n.柜台adj.相反的",
"v.撤回，取消",
"n.对策",
"n.还价，还盘",
"n.同类的人或物",
"v.副署，会签",
"n.副署，会签",
"adj.无数的",
"n.国家，乡间，故乡",
"n.乡下",
"n.县，郡",
"n.一对，几个，夫妇",
"n.勇气，胆量",
"adj.勇敢的",
"n.过程，路线，课程",
"n.法庭，宫廷，球场",
"adj.有礼貌的",
"n.礼貌，礼仪，好意",
"n.院子",
"n.堂(或表)兄弟姐妹",
"v.盖，掩盖n.盖子",
"n.覆盖率",
"adj.包括的",
"n.母牛，奶牛",
"n.懦夫",
"adv.胆小地",
"n.蟹",
"v.使...破裂n.裂缝",
"n.苏打饼干，克力架",
"n.摇篮，发源地",
"n.工艺，手艺，飞机",
"n.手艺人",
"n.手艺",
"n.鹤，起重机",
"v.碰撞n.坠毁",
"n.一箱，篓，筐",
"v.渴望，恳求",
"v.爬行，徐徐行进",
"n.疯狂",
"adj.疯狂的，迷恋的",
"n.ru脂，奶油",
"adj.奶油的，奶黄色的",
"v.创造，创作，造成",
"n.创造，创造物",
"adj.有创造力(性)的",
"n.家伙，生物",
"n.信誉，信用v.相信",
"adj.有信誉的",
"n.商誉",
"n.小川，小湾",
"v.爬行，蔓延",
"n.(飞机等的)全体人员",
"n.板球，蟋蟀",
"n.罪，罪行",
"n.罪犯adj.犯罪的",
"adj.n.深红色(的)",
"n.跛子v.使残废",
"n.危险，危险期",
"adj.松脆的，鲜嫩的",
"n.评论家，爱挑剔的人",
"adj.批评的，危急的",
"n.批评",
"v.批评，评论",
"n.钩子",
"adj.弯曲的，歪的",
"n.作物，庄稼",
"n.十字，交叉v.横过",
"n.交叉，十字路口",
"n.交叉路口，十字路",
"v.蹲下，缩着",
"n.乌鸦v.鸦啼",
"n.人群v.挤满",
"n.王冠v.加冕",
"adj.未加工的，粗糙的",
"adj.残酷的，残忍的",
"n.残忍，残酷行为",
"v.巡游，巡航",
"n.面包屑",
"adj.粉碎，崩溃",
"v.压榨，粉碎",
"n.面包皮，硬的表面",
"n.拐杖",
"v.n.叫喊，哭泣",
"n.水晶，晶体",
"n.立方体，三次方",
"adj.立方的",
"n.立体主义",
"n.布谷鸟，杜鹃",
"n.黄瓜",
"v.耕作，栽培，培养",
"n.耕作，培养",
"adj.文化的",
"n.文化，养殖",
"adj.狡猾的，狡诈的",
"n.杯子，一杯",
"n.碗橱",
"v.制止，束缚",
"v.n.治疗，矫正",
"n.好奇心，古玩",
"adj.好奇的，爱打听的",
"v.卷曲，缭绕n.卷发",
"adj.卷曲的，波浪式的",
"n.通货，货币",
"adj.现令的n.流",
"adv.当前，广泛地",
"n.v.诅咒，咒骂",
"n.削减，剥夺",
"n.窗帘，幕布",
"n.曲线，弯曲",
"n.垫子，靠垫",
"n.保管，监护",
"n.风俗，习惯",
"adj.习惯的，通常的",
"n.顾客，主顾",
"n.海关",
"v.割，切，削减，切断",
"n.刀具，餐刀",
"n.刀具，裁剪者",
"n.切片，剪辑",
"n.周期，循环，自行车",
"n.自行车运动员",
"n.圆筒，柱，汽缸",
"n.(缩)承兑交单",
"n.涤纶",
"n.爸爸",
"n.匕首",
"adj.每日的adv.天天",
"adj.优雅，考究",
"n.奶牛场，ru品商店",
"n.坝",
"v.n.损害，破坏",
"v.n.诅咒",
"adj.潮湿的n.潮气",
"v.跳舞n.舞蹈",
"n.舞蹈者，舞蹈演员",
"n.危险，威胁",
"adj.有危险的",
"adj.n.丹麦人(的)",
"n.丹麦",
"v.敢，挑战，竟敢",
"adj.大胆的，勇敢的",
"adj.黑暗的n.暗处",
"v.变黑，转暗",
"n.黑暗",
"n.爱人adj.心爱的",
"n.飞标游戏",
"v.猛冲泼溅n.破折号",
"n.(复数)资料，数据",
"n.日期v.注日期",
"n.约会",
"n.女儿",
"n.儿媳",
"n.黎明，开端",
"n.一天，白天",
"n.破晓",
"n.日光，白昼",
"n.日间",
"v.耀眼，使迷乱",
"v.使...眼花缭乱",
"adj.令人目眩的",
"adj.死的n.死者",
"n.期限",
"adj.致命的，死一般的",
"adj.聋的",
"v.使...聋，震聋",
"v.处理，交易n.买卖",
"n.商人，贩子",
"n.交往，生意",
"n.系主任",
"adj.亲爱的，敬爱的",
"n.死，死亡",
"adj.致死的",
"v.n.辩论，讨论",
"n.借方",
"n.债，债务",
"n.十年",
"v.n.腐烂，衰败",
"adj.已死的",
"n.欺骗，欺诈行为",
"v.欺骗",
"n.欺诈",
"adj.欺骗性的",
"n.十二月",
"n.体面",
"adj.体面的，象样的",
"v.决定，判决",
"adj.明确的，果断的",
"adv.明确地，果断的",
"adj.十进制的，小数的",
"n.决定，决议",
"adj.决定性，明确的",
"n.甲板",
"n.宣布，宣告",
"v.宣布，声明",
"v.婉谢，推辞n.衰落",
"adj.下降的，衰落的",
"v.分解，腐烂",
"v.装饰",
"n.装饰物",
"adj.装饰的，装璜的",
"v.n.减少",
"n.法令v.判决",
"v.奉献，致力",
"v.演绎，推断",
"v.减",
"n.推断，减少",
"n.行为，契据",
"v.以为，认为",
"adj.深的，深远的",
"v.加深，深化",
"adv.深深的，深切地",
"n.鹿",
"n.v.不履行，不负责",
"v.击败n.失败",
"n.缺点，缺陷",
"adj.有缺点的",
"n.保卫，防御",
"v.保卫，为...辩护",
"v.拖延",
"n.蔑视，挑战",
"adj.无礼的，挑战的",
"n.缺乏",
"adj.缺乏的，不足的",
"n.赤字",
"v.下定义，界定，规定",
"adj.明确的，限定的",
"adv.明确地，肯定地",
"n.定义，解释",
"adv.定义的",
"v.收缩，紧缩",
"v.偏斜",
"n.偏转，偏斜",
"v.使变形，使残废",
"n.变形",
"v.支付",
"v.反抗，蔑视，使不能",
"n.降低，恶化",
"v.败低，下降，堕落",
"n.程度，度，学位",
"v.n.耽搁，延误",
"n.保付",
"n.代表n.委派",
"n.代表团",
"v.删除",
"n.删除",
"adj.故意的，审慎的",
"adv.故意地，从容地",
"n.慎重，故意",
"n.精致",
"adj.优雅的，精致的",
"adj.美味的",
"n.快乐，乐事n.喜爱",
"adj.令人高兴的",
"n.轻微犯罪",
"adj.拖欠的",
"v.交付，递送，讲述",
"n.救助",
"n.交付，递送，讲述",
"n.错觉",
"adj.令人产生错觉的",
"v.n.要求，需求",
"adj.对人要求严格的",
"n.民主，民主政体",
"n.民主党人",
"adj.民主的",
"v.拆除",
"n.拆除",
"v.论证，演示，表明",
"n.示范，表演，示威",
"n.滞期费",
"n.窝",
"n.拒绝，否定",
"v.为...命名",
"n.命名",
"v.表示",
"v.谴责，斥责",
"adj.稠密的，浓厚的",
"n.密度，稠密",
"n.牙，槽，凹陷",
"n.牙科医生",
"v.否认，拒绝",
"v.离去，出发，违反",
"n.部，部门，系",
"n.离开，违背",
"v.依靠，依赖",
"n.可依赖性",
"adj.可依赖的",
"n.受赡养者",
"n.依靠，依赖",
"adj.依靠的，随..而定",
"v.描述，描画",
"n.描述",
"v.减少，耗尽",
"v.存放，储蓄n.存款",
"n.免职，罢官",
"v.降价，贬值，折旧",
"n.折旧，贬值",
"v.抑制，使人抑郁",
"adj.情绪低落的",
"n.沮丧，萧条",
"v.剥夺，丧失",
"n.深度",
"n.代表adj.副职的",
"n.起源，衍生物",
"v.从...而来，得来",
"n.钻塔，井架",
"v.降临，下来，遗传",
"n.子孙，后裔",
"n.下降，血统",
"v.描写，作图",
"n.描述，形容",
"v.遗弃，擅离n.沙漠",
"v.应受，值得",
"v.设计，旨在n.设计",
"v.指明，指定",
"n.指定，委派",
"n.设计者",
"adj.合乎要求的",
"n.欲望，要求v.要求",
"n.课桌，写字台",
"adj.荒芜的，凄凉的",
"n.荒凉，凄凉",
"n.v.绝望",
"adj.不顾一切的",
"n.绝望",
"v.鄙视，看不起",
"prep.不管，任凭",
"n.(最后一道)甜食",
"n.终点，目的地",
"v.注定，预定",
"n.命运，定数",
"v.破坏，摧毁，消灭",
"n.破坏，毁灭",
"adj.破坏性的",
"v.分离，拆开",
"n.细节",
"adj.详细的，详尽的",
"v.留住，阻止",
"v.发现，侦察",
"n.发现，侦查",
"n.侦探",
"v.恶化，败坏",
"n.退化",
"n.决心，决定",
"v.决心，决定，测定",
"v.绕道，绕开",
"v.降低",
"n.损害",
"adj.有害的",
"n.贬值",
"v.贬值",
"v.发展，开发，成长",
"adj.发展中的",
"n.进展，发展",
"v.背离",
"n.背离，偏向",
"n.装置，方法",
"n.魔鬼，恶人",
"v.设计，计划",
"v.奉献，贡献",
"adj.献身于...的",
"n.献身，专心",
"v.吞吃，吞没",
"n.露水",
"v.诊断",
"n.诊断",
"n.图表，图解",
"n.钟盘v.拨电话",
"n.方言",
"n.对话，对白",
"n.直径",
"n.钻石，金刚石",
"n.日记",
"v.口授，命令",
"n.口授，听写",
"n.独裁者",
"n.独裁，专政",
"n.措辞",
"n.词典，字典",
"v.死，消亡",
"n.内燃机，柴油机",
"n.饮食，节食",
"v.不同，相异",
"n.差异，差别",
"adj.不同的，各种",
"adj.有差别的",
"adv.不同地",
"adj.困难的",
"n.困难，难题",
"v.挖，采掘",
"v.消化n.摘要",
"n.消化",
"n.数字",
"adj.数字的",
"n.尊贵，尊严",
"n.堤",
"v.稀释",
"adj.勤奋的，用功的",
"adj.暗淡的，模糊的",
"n.(美元)一角",
"n.维，方面，尺寸",
"adj.尺寸的",
"v.减少，缩小",
"v.用餐",
"n.餐厅",
"adj.肮脏的",
"n.正餐，晚餐，宴会",
"v.n.蘸，浸",
"n.毕业文凭，学位证书",
"n.外交",
"n.外交人员",
"n.外交的",
"v.支配，指挥，对准",
"n.方向，指示，说明",
"n.命令，指令",
"adv.直接地，立即",
"n.指导者，导演，领导",
"n.目录，地址录",
"n.尘埃，灰尘，泥土",
"adj.肮脏的",
"v.使残废",
"adj.残废的n.残疾人",
"n.不利之处",
"adj.不利的",
"v.意见不合，不符",
"n.不和，不一致",
"v.不允许",
"v.失踪，消失",
"n.消失",
"v.使...失望",
"adj.失望的，扫兴的",
"n.失望",
"n.不批准",
"n.自然灾害，祸患",
"adj.灾难性的",
"v.支付",
"n.支付",
"n.圆盘，唱片",
"v.n.丢弃，扔掉",
"v.操作别，辨明",
"v.解除，放出，卸货",
"adj.纪律的，学科的",
"n.训练，纪律n.锻炼",
"v.放弃，不承认",
"v.揭开，透露",
"n.不安，不舒服",
"adj.不舒服的",
"v.中断",
"n.v.折扣",
"v.使...泄气，阻止",
"n.演说，谈话，话语",
"v.发现",
"n.发现，发现物",
"adj.周到的，慎重的",
"adv.慎重地",
"n.单货不符",
"n.慎重",
"v.区别，岐视",
"n.辨别，岐视",
"v.讨论",
"v.讨论，商议",
"v.轻视",
"n.疾病",
"n.耻辱v.使受辱",
"adj.耻辱的，受辱的",
"v.n.伪装，掩饰",
"n.厌恶v.使讨厌",
"adj.令人生厌的",
"n.盘子，碟子",
"adj.不名誉的",
"n.耻辱v.凌辱",
"v.使觉醒，幻灭",
"adj.不愿意的",
"n.消毒剂",
"n.分散，解体",
"v.n.厌恶",
"adj.不忠的",
"adj.不忠",
"adj.阴郁的，沉闷的",
"v.使沮丧n.沮丧",
"v.解散，开除",
"n.解散，开除",
"v.不服从",
"n.紊乱，骚乱，失调",
"n.不同，悬殊",
"v.迅速派遣n.快件",
"v.驱散",
"v.分配，施予",
"v.驱散，散布",
"v.置换，取代",
"n.置换，替换物",
"v.n.陈列，表现",
"v.使生气，惹怒",
"n.不快",
"n.处置，对付",
"v.处置，对付，解决",
"adj.有...倾向的",
"n.布置，处置",
"v.争论，质疑n.争论",
"v.n.无视，不顾",
"n.不满",
"v.使不满",
"adj.不同的",
"v.驱散，消耗，浪费",
"v.溶解，使终结",
"n.距离，远处",
"adj.远方的，疏远的",
"n.蒸馏",
"adj.不同的，明显的",
"n.差别，非凡",
"adv.明晰地，清楚地",
"v.辨别，认出",
"adj.尊贵的，尊敬的",
"v.扭曲，歪曲",
"n.曲解，失真，变形",
"v.分神，迷惑",
"n.分心",
"n.苦恼，不幸",
"v.分配，分布，分销",
"n.分配，分布",
"n.分销商",
"n.分销权",
"v.区，区域，地区",
"v.打扰，打乱，使烦恼",
"n.干扰，动乱",
"v.使分裂",
"v.n.废止",
"n.沟，渠，下水道",
"n.同上",
"v.潜水，跳水，俯冲",
"n.潜水员，跳水运动员",
"v.分歧，离题",
"n.分歧",
"adj.不同的，分歧的",
"n.转移，消遣",
"n.多样化",
"v.使转向，消遣",
"v.分开，分享，分裂",
"adj.神的，神圣的",
"n.划分，部分",
"v.离婚，使脱离",
"adj.晕眩的",
"v.做，干，足够，制作",
"n.码头",
"n.医生，博士",
"n.教义，学说",
"n.文件，公文",
"adj.文化的",
"n.提供文件",
"v.躲避",
"n.狗",
"adv.顽固地",
"n.玩偶，娃娃",
"n.元，美元",
"n.领土，领域",
"n.圆顶，穹窿",
"adj.家里的，国内的",
"adj.统治的",
"v.统治，支配，占优势",
"v.捐献",
"n.捐献",
"n.驴，笨蛋",
"n.命运，判决v.命定",
"n.门，(一户)人家",
"n.门口，门道",
"n.集体宿舍",
"n.剂量，一服药",
"n.点，圆点",
"adj.两倍的，双重的",
"v.n.怀疑，疑惑",
"adj.怀疑的，可疑的",
"adv.无疑地，大约",
"n.面团",
"n.鸽子",
"adv.向下，下降",
"adv.在楼下",
"n.闹市adv.去市里",
"adj.向下的，下坡的",
"adv.向下，以下",
"v.打瞌睡",
"n.一打",
"n.草案，草稿，穿堂风",
"v.拖，拽",
"n.龙",
"v.排水，耗竭，泄",
"v.排水系统，污水",
"n.戏剧，剧本",
"adj.戏剧性的，显著的",
"n.戏剧家",
"v.使戏剧化",
"adj.激烈的，严厉的",
"v.画，拉，吸引",
"n.不利，欠缺",
"n.抽屉",
"n.素描，绘画，图样",
"v.n.恐惧，担心",
"adj.可怕的，糟糕的",
"n.梦，梦想v.做梦",
"adj.疲劳的",
"v.浸泡，充满",
"n.服装v.穿衣",
"n.打扮，调味品",
"v.漂流，游荡",
"n.钻头，操练v.训练",
"v.喝，饮n.饮料，酒",
"v.滴下，流下",
"v.驾驶，乘车n.车道",
"n.司机",
"v.下垂",
"v.落下n.滴，下降",
"n.中途退出者",
"n.旱灾",
"v.淹死",
"n.药物，麻醉剂",
"n.零食店",
"n.鼓v.敲鼓",
"adj.喝醉的",
"n.醉鬼",
"adj.干的，枯燥的",
"adj.怀疑的",
"n.鸭子",
"adj.到期的，预定的",
"n.公爵",
"adj.沉闷的，钝的",
"adv.按期地",
"adj.哑的",
"n.傀儡",
"v.倾倒n.垃圾堆",
"n.倾销",
"n.粪",
"n.地牢",
"adj.二重的，复制的",
"adj.持久的，耐用的",
"n.期间，待续时间",
"prep.在...期间",
"n.黄昏",
"n.尘土，粉末v.掸土",
"n.簸箕",
"adj.沾满灰尘的",
"n.责任，义务，关税",
"adj.免税的",
"n.矮子，侏儒",
"v.居住",
"n.居住者，住客",
"n.住宅",
"n.染料v.染色",
"adj.动力的，动态的",
"n.朝代，王朝",
"adj.adv.名，每个",
"adj.热切的，渴望的",
"n.鹰",
"n.耳朵，穗",
"n.伯爵",
"adj.早的，初期的",
"n.标记，特征",
"v.挣钱，赢得",
"adj.认真的，诚恳的",
"n.收入，赚得的钱",
"n.耳机",
"n.地球，地上，泥土",
"adj.世俗的",
"n.地震",
"n.安逸，轻易",
"adv.容易地，安逸地",
"adj.东方的n.东方",
"n.复活节",
"adj.东的，朝东的",
"adv.向东",
"adj.容易的，轻松的",
"adj.逍遥自在的",
"v.吃",
"adj.性格怪僻的",
"n.怪僻",
"n.回声，反响，共呜",
"n.(日、月)食，蚀",
"n.生态学",
"adj.经济的，经济学的",
"adj.节省的，经济的",
"adv.经济上",
"n.经济学",
"v.节省",
"n.经济，节约",
"n.狂喜",
"n.边，边缘，刀刃",
"v.校订，编辑",
"n.片(本)",
"n.编辑，编者",
"n.社论",
"v.教育",
"n.教育，训练",
"adj.教育的",
"n.鳝鱼",
"n.后果，效力v.导致",
"adj.有效的",
"adv.有效地",
"n.有效",
"n.效率，功效",
"adj.效率高的",
"n.努力，尽力，成果",
"g.(缩)例如",
"n.卵，蛋，鸡蛋",
"n.茄子",
"n.埃及",
"adj.n.埃及人(的)",
"num.八",
"num.十八",
"num.第八，八分之一",
"num.八十",
"adj.二者之一adv.也",
"v.喷射",
"n.喷射",
"v.adj.详尽阐述",
"n.详尽阐述",
"v.(时间)消逝",
"adj.弹性的，灵活的",
"n.弹性",
"n.肘，弯管",
"adj.年长的，资格老的",
"v.选举adj.当选的",
"n.选举",
"adj.电的，电力的",
"adj.电的",
"n.电工",
"n.电",
"v.充电，电气化",
"n.电子",
"adj.电子的",
"n.电子学",
"n.优雅",
"adj.优雅的，典雅的",
"n.成分，元素",
"adj.自然力的，基本的",
"adj.基础的，初步的",
"n.象",
"v.提升，抬高",
"n.海拔，提高，崇高",
"n.电梯",
"num.十一",
"num.第十一",
"v.消灭，删除",
"n.消灭，删除",
"adj.椭圆的，省略的",
"n.省略",
"n.雄辩，口才",
"adj.雄辩的，有口才的",
"adj.别的adv.否则",
"adv.在别处",
"adj.躲闪的",
"n.電子郵件",
"v.解放",
"n.解放",
"n.禁运",
"v.登陆",
"v.使窘，使为难",
"adj.令人尴尬的",
"n.窘迫，尴尬",
"n.使馆",
"v.体现，包含",
"v.拥抱，接受，包括",
"v.绣",
"v.刺绣(品)",
"v.出现，暴露",
"n.紧急情况，急诊",
"n.移居国外的人",
"v.移居国外，移民",
"n.向国外移民",
"adj.杰出的，突出的",
"n.发射，散发",
"v.发射，散发",
"n.感情，情绪",
"adj.感情的，激动的",
"n.皇帝",
"n.强调，重点，重读",
"v.强调，着重",
"adj.强调的，着重的",
"n.帝国，财团",
"adj.经验的",
"v.雇用，使用，从事",
"n.雇员",
"n.雇主",
"n.职业，就业",
"n.空虚，空白",
"adj.空的，空虚的",
"v.使能够，使可能",
"v.迷住，陶醉",
"v.环绕，包围",
"v.围住，圈起，封入",
"n.围绕，附件",
"v.面临，遭遇",
"v.鼓舞，鼓励，助长",
"n.鼓舞，鼓励",
"n.百科全书",
"n.结尾v.终止，结束",
"v.危及，危害",
"v.n.努力，尽力",
"n.结局",
"adj.无穷无尽的",
"v.背签",
"n.背书",
"v.资助，赋予，授予",
"n.忍耐力，耐用",
"v.忍受，容忍，持久",
"n.最终用户",
"n.敌人，对手",
"adj.精力旺盛的",
"n.精力，活力，能量",
"v.实施，强制",
"v.从事，雇用，吸引",
"adj.占用的，从事..的",
"n.约束，约会，婚约",
"n.发动机，火车头",
"n.工程师",
"n.工程",
"n.英格兰，英国",
"n.adj.英国的，英语",
"n.英国人",
"v.刻上，牢记",
"adj.雕刻",
"v.吞没",
"v.提高，增加",
"n.提高",
"v.欣赏，享有，享受",
"adj.愉快的",
"n.享受，乐趣",
"v.扩大，扩展，放大",
"n.扩大",
"v.启发，教导",
"adj.给人启发的",
"adj.巨大的，庞大的",
"adj.adv.足够(的)",
"v.询问",
"v.询问",
"v.使富裕",
"v.登记，招收",
"n.招收",
"adv.在途中",
"v.保证，担保，保护",
"v.遗留给，引起",
"v.进入，加入",
"n.事业，企业",
"v.招待，使欢乐",
"n.招待，娱乐",
"v.热情，热心",
"adj.热情的，热心的",
"adj.完全的，全部的",
"adv.完全地，彻底地",
"n.全部",
"v.给...权利，资格",
"n.进入，入口",
"v.恳求，请求",
"v.委托",
"n.进入，入口，词条",
"v.列举",
"v.包，围绕",
"n.信封",
"adj.嫉妒的",
"n.环境",
"adj.环境的",
"v.n.嫉妒，羡慕",
"adj.传染的n.传染病",
"n.事件，情节，插曲",
"n.时代，纪元",
"adj.划时代的",
"adj.相等的，胜任的",
"n.平等，相等",
"adv.相等地，相同地",
"n.等式，方程式",
"n.赤道",
"n.平衡，均衡",
"v.装备，配备",
"n.设备，器材，装置",
"n.相等，等值",
"adj.相等的，等值的",
"n.时代，年代",
"v.根除",
"n.根除",
"v.擦掉，抹去",
"n.抹去",
"v.树立，建立，竖立",
"n.竖立，建立",
"n.腐蚀，侵蚀",
"v.犯错误",
"n.差事，差使",
"n.错误，过失",
"v.喷发，爆发",
"n.喷发，爆发",
"n.电动扶梯",
"v.逃跑，避免，被遗忘",
"v.护送n.护卫队",
"adj.特别的，专门的",
"adv.特别地，专门地",
"n.散文，论文，小品文",
"n.散文作家",
"n.本质，情髓，香精",
"adj.必需的，本质的",
"adj.本质上，实质上",
"v.建立，设立，确立",
"adj.已建立的",
"n.建立，组织",
"n.房地产，财产",
"v.n.尊重",
"v.n.估算，预算",
"n.估算，估计",
"(缩)等等",
"adj.永恒的，无休止的",
"n.欧洲",
"n.adj.欧洲人(的)",
"v.估价，评价",
"n.估价，评价",
"v.蒸发，脱水，消失",
"n.蒸发，升华",
"n.前夕，前夜",
"adj.平坦的，均匀的",
"n.傍晚，晚上",
"adv.平坦地，均匀地",
"n.事件，场合，比赛",
"adj.多事的",
"adv.最终，终于",
"adv.曾经，总是，究竟",
"adj.永久的，持久的",
"adj.每个，所有的",
"pron.人人，每人",
"adj.每日的，日常的",
"pron.人人，每人",
"pron.事事，一切",
"adv.处处，到处",
"n.证据，迹象",
"adj.明显的，明白的",
"adv.明显地，显然",
"adj.坏的，邪恶的",
"v.发展，渐进，进化",
"v.发展，进化",
"prep.在...交货",
"adj.精确的，精密的",
"adv.确切地，正是",
"v.夸张，夸大",
"adj.言过其辞的",
"n.夸张",
"v.抬高，发扬",
"adj.高贵的，得意的",
"n.考试",
"n.检查，考试",
"v.检查，细看，考试",
"n.例子，榜样",
"v.激怒，恶化",
"n.愤慨，加剧",
"v.超过，过度",
"adv.非常，极端地",
"v.胜过，优于",
"n.优秀，卓越",
"adj.优秀的，卓越的",
"prep.除...外v.除外",
"n.除外，例外",
"adj.异常的，例外的",
"n.过量，过剩",
"adj.过分的，极度的",
"v.交换，兑换n.交易",
"v.刺激，使兴奋",
"adj.兴奋的",
"n.兴奋，激动",
"adj.令人激动的",
"v.呼喊，感叹",
"n.呼喊，感叹",
"v.排除，拒绝考虑",
"n.排除",
"adj.独有的",
"adv.独占地",
"n.独家经营权",
"n.短途游览",
"v.原谅n.借口",
"v.执行，实施，处决",
"n.执行，处决",
"adj.执行的n.执行者",
"v.举例说明",
"v.免除",
"n.锻炼，练习，运用",
"n.练习簿",
"v.尽(力)，发挥",
"n.尽力，竭力",
"v.竭尽，用完",
"adj.精疲力竭的",
"n.用尽，详述",
"adj.详尽的",
"v.展出显示n.展览品",
"n.展览会，表现",
"v.放逐n.流亡者",
"v.存在，生存",
"n.存在，生存",
"adj.现存的，已有的",
"n.出口，安全门，离开",
"v.昭雪，解除",
"n.免罪，免除",
"v.扩张，膨胀，扩充",
"n.扩张，扩大",
"v.盼望，期待，预料",
"v.期待，前程",
"n.便利，权宜之计",
"adj.方便的，临时的",
"v.加快，急送",
"n.探险，考察队",
"v.驱逐，开除",
"v.花费，消耗",
"n.支出，费用",
"n.支出，开支",
"adj.昂贵的，高价的",
"n.v.经历，经验",
"adj.有经验的",
"n.v.实验，试验",
"adj.实验的",
"n.实验",
"n.专家，能手",
"n.专家队伍(总称)",
"n.期满",
"v.到期，断气",
"n.逾期",
"v.解释，说明",
"n.说明，解释",
"adj.说明的",
"adj.清楚的，明晰的",
"adv.清晰地",
"v.爆炸，激增",
"v.开发，利用，剥削",
"n.开发，利用",
"n.勘探，考察",
"v.勘探，考察",
"n.勘探者，探险家",
"n.爆炸，爆发，激增",
"adj.爆炸性的n.炸药",
"v.n.输出，出口",
"n.出口",
"n.出口商",
"v.暴露，揭露，陈列",
"n.展览会，说明",
"n.揭露，曝光",
"v.表达，快递n.快车",
"n.表达，措辞，表情",
"adj.有表现力的",
"adj.明确表示的",
"n.高速公路",
"adj.精致的",
"v.延伸，扩大，给予",
"n.延伸，电话分机",
"adj.广泛的，密集的",
"adv.广泛地",
"n.范围，限度，一大片",
"adj.n.外部(的)",
"adj.外部的，对外的",
"adj.绝灭的，熄灭的",
"n.绝灭，熄灭",
"v.扑灭，熄灯",
"adj.额外的，外加的",
"v.取出，榨出，摘录",
"n.出身，摘要",
"n.特别的，格外的",
"n.奢侈，浪费",
"adj.奢侈的，浪费的",
"adj.极度的，极端的",
"adv.极其，非常",
"n.眼睛，孔眼，视力",
"n.眼球",
"n.眉毛",
"n.眼镜",
"n.眼睑",
"n.视力",
"n.寓言",
"n.织物，结构，组织",
"v.制作，捏造",
"n.制作，虚构",
"n.脸，正面v.面对",
"v.使便利，使容易",
"n.方便，设施，便利",
"n.事实，真相",
"n.宗派，派别",
"n.因素，因数，要素",
"n.工厂，制造厂",
"n.本领，学系",
"v.褪色，枯萎",
"n.adj.华氏(的)",
"v.失败，不及格，不能",
"adj.缺点",
"n.失败，疏忽，破产",
"adj.软弱的，模糊的",
"adj.公平的n.交易会",
"adj.公平地，相当",
"n.妖精，仙女",
"n.信任，信念",
"adj.忠诚的，可靠的",
"adv.忠诚地",
"adj.冒片的n.冒牌货",
"v.落下，跌倒n.瀑布",
"adj.假的，假造的",
"n.名声，声誉",
"n.熟悉，相似",
"adj.熟悉的，亲近的",
"n.家庭，家属",
"n.饥荒，饥饿",
"adj.著名的",
"n.扇子，...迷v.扇",
"adj.狂热的，入迷的",
"n.幻想，爱好v.想象",
"adj.奇异的，荒谬的",
"adj.遥远的adv.远",
"n.车费v.饮食",
"int.再见adj.告别的",
"n.农场，农庄",
"n.农夫，农场主",
"n.农工，农场工人",
"n.农舍",
"n.农业，种植业",
"adv.较远，更进一步",
"v.吸引，入迷，蛊惑",
"n.入迷",
"n.法西斯",
"n.法西斯分子",
"n.方式，时髦，时装",
"adj.流行的，时髦的",
"adj.快的adv.快",
"v.捆紧，钉牢",
"n.脂肪adj.肥胖的",
"adj.致命的",
"n.命运，厄运，宿命",
"n.父亲，神父，始祖",
"n.岳父，公公",
"v.领会，推测",
"n.v.(使)疲劳",
"n.缺点，过失，断层",
"adj.完美的",
"adj.有缺点的",
"n.帮助，偏爱v.宠爱",
"adj.赞成的，有利的",
"adv.有利地，顺利地",
"n.adj.最喜爱的人或物",
"國際刑警",
"n.v.害怕，担忧",
"adj.可怕的，吓人的",
"adj.毫不畏惧的",
"n.可行性",
"adj.可行的，做得到的",
"n.v.宴会，宴请",
"n.功绩",
"n.羽毛",
"n.相貌，特征，特写",
"n.二月",
"adj.联邦的",
"n.联邦",
"n.费用，酬金",
"adj.虚弱的，无力的",
"v.喂养，吃东西",
"n.反馈",
"v.感到，摸，意识到",
"n.知觉，感觉，感情",
"v.砍到",
"n.家伙，同事",
"n.交情，会员资格",
"adj.女性的，雌的",
"adj.女性的，妇女的",
"n.围栏，篱笆",
"adj.凶猛的，野蛮的",
"adj.铁的，含铁的",
"n.渡船v.渡运",
"n.渡船",
"adj.肥沃，多产的",
"n.肥料，化肥",
"adj.强烈的，热烈的",
"n.节日adj.喜庆的",
"v.去取来，去请来",
"n.纠纷，封地",
"adj.封建的",
"n.封建主义",
"n.发烧，狂热",
"adj.少的n.少数",
"n.纤维，质地",
"n.小说，虚构",
"adj.虚构的",
"n.提琴",
"n.田野，战场，场",
"adj.凶猛的，猛烈的",
"adj.火的",
"num.十五",
"num.第五，五分之一",
"num.五十",
"n.无花果",
"v.打仗，战斗，作斗争",
"n.战士",
"adj.比喻的，修饰的",
"n.数字，图形，人物",
"n.档案，纵列，锉刀",
"n.档案管理",
"v.装满，充满，补缺",
"n.充填物，馅",
"n.胶片，电影，薄膜",
"n.滤器v.过滤",
"n.污秽，污物",
"adj.污秽的",
"adj.最终的n.决赛",
"v.落实，定下来",
"adv.最终，终于",
"n.金融v.资助",
"adj.金融的，财政的",
"n.金融家",
"n.金融业，财政学",
"v.寻找，找到，发现",
"n.发现，发现物",
"adj.好的，精细的",
"n.手指",
"v.n.结束，抛光",
"adj.制成的",
"adj.有限的，限定的",
"n.裘皮",
"n.火，火灾v.开火",
"n.消防车",
"n.消防队员",
"n.壁炉",
"n.焰火",
"adj.坚固的n.商号",
"adv.坚定地，坚固地",
"n.坚定，坚固",
"adj.第一的adv.首先",
"adj.第一流的",
"n.鱼v.捞取，探听",
"n.渔夫",
"n.渔业",
"n.裂变，分裂",
"n.拳头",
"adj.适合的，健康的",
"n.适合，健康",
"adj.适当的",
"num.五",
"v.固定，确定，修理",
"adj.固定的，已确定的",
"n.固定物，固定装置",
"n.旗",
"n.片，片状物",
"n.火焰，热情",
"n.侧面，胁腹",
"n.法兰绒",
"v.拍打n.垂下物",
"v.n.闪烁",
"n.v.闪光，闪现",
"n.瓶，烧瓶",
"adj.平的，平淡的",
"v.弄平，变平",
"v.奉承，谄媚",
"n.滋味，风趣",
"n.裂缝，瑕疵，缺点",
"v.逃走，消散",
"n.羊毛",
"n.船队",
"n.肌肉，骨肉，果肉",
"adj.肉的",
"n.柔韧，灵活性",
"adj.柔韧的，灵活的",
"v.闪烁",
"n.飞，航班，逃走",
"v.抛，掷",
"v.浮，漂n.彩车",
"n.群v.群集",
"n.洪水，大量",
"n.地板，(楼)层",
"n.面粉",
"v.茂盛，兴旺",
"v.流动n.流动，流量",
"n.花，盛期",
"n.流感",
"v.波动，起伏",
"n.波动",
"n.流利，流畅",
"adj.流利的",
"n.液体adj.流动的",
"v.(脸)发红n.红晕",
"n.长笛，笛子",
"v.飘动，振翼",
"n.流动，变迁",
"v.飞，驾机n.苍蝇",
"n.泡沫v.起泡",
"(缩)离岸价",
"n.焦点，中心v.集中",
"n.饲料",
"n.敌人，宿敌",
"n.雾，翳",
"adj.有雾的，雾蒙蒙的",
"v.折叠n.折痕",
"n.叶子(总称)",
"n.人们，乡亲，亲属",
"v.跟随，听懂，遵循",
"n.追随者，信徒",
"adj.下列的，其次的",
"n.adj.后续(的)",
"adj.喜爱..的，慈爱的",
"n.食物，食粮",
"n.食品",
"n.蠢人，傻瓜v.愚弄",
"n.愚蠢的，笨的",
"n.脚，英尺，最下部",
"n.足球",
"n.立足点，立场",
"n.足迹，脚步声",
"prep.给，作...用的",
"v.禁止，不许",
"adj.禁止的",
"n.力，力量v.强迫",
"adj.前面的adv.在前面",
"n.v.预测，预报",
"n.祖先，先辈",
"n.食指",
"adj.先行的，上述的",
"n.前额",
"adj.外国的，对外的",
"n.外国人，异乡人",
"n.领班",
"adj.最初的，第一流的",
"v.预见，预知",
"n.森林",
"n.林业",
"v.预告，预言",
"adv.永远，总是",
"v.打铁，锻造，伪造",
"n.锻炉，锻造厂",
"v.忘记，疏忽，没想到",
"v.饶恕，原谅，豁免",
"n.餐叉，岔口",
"n.形状，类型，表格",
"adj.形式上的，正式的",
"n.礼节，正式",
"n.格式，样式",
"n.形成，构成",
"adj.以前的，前者",
"adv.从前，以前",
"adj.可怕的，难对付的",
"n.公式",
"v.系统阐述",
"n.确切表述",
"v.遗弃，抛弃",
"n.堡垒，要塞",
"adv.向前，向外",
"adj.即将到来的",
"n.坚毅",
"n.两星期",
"n.堡垒，城堡",
"n.偶然事件",
"adj.幸运的，侥幸的",
"adv.幸运地，幸而",
"n.运气，财富",
"num.四十",
"n.讨论会，座谈会",
"adj.向前的adv.向前",
"n.化石，守旧者",
"v.养育，抚养",
"adj.肮脏的，邪恶的",
"v.创办，使有根据",
"n.建立，基金，基础",
"n.创办人，奠基人",
"n.泉，源泉，喷泉",
"num.四",
"num.十四",
"num.第四，四分之一",
"n.家禽，鸡，禽肉",
"n.狐狸，狡猾的人",
"n.片断，分数",
"adj.零碎的，不足的",
"n.断裂v.折断",
"adj.易碎的，脆的",
"n.碎片，片断",
"n.芬芳，香气",
"adj.香的，芬芳的",
"adj.脆弱的，虚弱的",
"n.框架，骨骼v.构造",
"n.构架，机构",
"n.法国",
"n.特许权",
"adj.坦率的，真诚的",
"adv.坦率地",
"adj.自由的，空闲的",
"n.自由，免除",
"adv.自由地，随意地",
"v.结冰，楞住，冻结",
"n.冷冻箱",
"n.货运，货物，运费",
"adj.法国的n.法语",
"n.法国人",
"n.频繁，频率",
"adj.频繁的，经常的",
"adv.时常，往往",
"adj.新鲜的，崭新的",
"v.使新鲜，使振作",
"n.新人，新生",
"v.使烦恼n.烦燥",
"n.摩擦，摩擦力",
"n.星期五",
"n.朋友",
"adj.友好的，和气的",
"n.友谊，友好",
"n.恐怖，惊吓",
"v.惊吓，吓唬",
"adj.令人害怕的",
"adj.可怕的",
"n.边缘，花边，穗子",
"n.女上衣，童上装",
"n.蛙",
"prep.自，从...来",
"n.正面，前线v.面对",
"n.边界，国境，新领域",
"n.霜，霜冻",
"adj.霜的",
"v.皱眉头，厌恶",
"adj.节俭的",
"n.果子，水果，成果",
"adj.果实累累的",
"v.阻挠，使灰心",
"n.挫折，灰心",
"v.油煎，炸",
"n.煎锅",
"渾蛋，辱駡",
"n.燃料",
"v.完成，满足要求",
"n.完成，成就",
"adj.满的，完全的",
"adv.完全，彻底",
"v.摸索",
"n.娱乐，玩笑，乐趣",
"n.作用，集会，函数",
"adj.功能的",
"n.基金，资金，蕴藏",
"adj.基本的，根本的",
"n.葬礼",
"adj.有趣的，好笑的",
"n.毛皮，裘衣",
"adj.狂怒的，狂暴的",
"n.熔炉",
"v.供应，装备，摆家具",
"n.家具(总称)",
"n.犁沟",
"adv.更远，进一步",
"adv.而且",
"n.狂暴，狂怒",
"n.保险丝，导火线",
"n.忙乱，大惊小怪的",
"adj.爱大惊小怪的",
"n.将来，前途",
"n.期货",
"v.获得，赢得n.收益",
"n.大风，定期交付",
"n.美术馆",
"n.加仑",
"v.奔驰，飞跑",
"v.n.赌博，投机",
"n.赌徒",
"n.游戏，比赛，猎物",
"n.一群，一帮",
"n.匪徒，歹徒",
"n.监狱",
"n.空隙，隔阂，山口",
"n.车库，汽车修理站",
"n.垃圾",
"n.花园，菜园",
"n.园丁",
"n.园艺",
"n.大蒜",
"n.衣服，服装",
"n.要塞，警备队",
"n.气体，煤气，汽油",
"n.汽油",
"v.n.喘息，喘气",
"n.大门，门票收入",
"v.聚集，收集，采集",
"n.集会，聚集",
"n.规格，计量表",
"adj.快活的，快乐的",
"v.n.凝视，注视",
"n.齿轮，用品",
"n.宝石",
"adj.一般的，总的",
"n.概括",
"v.总结，归纳",
"adv.通常，大概",
"v.产生，发生，生殖",
"n.世代，一代人",
"n.发电机",
"n.慷慨，大方",
"adj.慷慨的，丰盛的",
"n.天份，才华，天才",
"adj.温柔的，温和的",
"n.绅士，先生，君子",
"adv.轻轻地，温柔地",
"adj.真正的，道地的",
"n.地理学，地形",
"n.地质学",
"n.几何学",
"n.萌芽，起源，细菌",
"adj.德国的n.德语",
"n.德国",
"n.姿势，手势，姿态",
"v.获得，记住，到达",
"n.集会，聚会",
"n.鬼魂，幽灵",
"n.巨人adj.巨大的",
"n.礼品，天赋",
"adj.巨大的",
"v.咯咯地笑",
"n.姜",
"n.少女，姑娘",
"v.给予，付出n.让步",
"adj.快乐的，高兴的",
"v.看一眼n.一瞥",
"n.v.闪耀，瞪眼",
"n.玻璃，镜子",
"n.玻璃制品",
"n.微光，闪光",
"v.n.滑行，溜",
"v.n.瞥见",
"v.闪光",
"v.闪闪发光",
"adj.全世界的，总的",
"n.全球化",
"v.使...全球化",
"n.地球，球体，地球仪",
"n.黑暗，忧郁",
"adj.阴沉的，忧郁的",
"adj.光荣的，辉煌的",
"v.颂扬，赞美",
"n.光荣，壮丽，荣誉",
"n.词汇表",
"n.手套",
"v.发光，发红",
"n.胶水n.粘贴",
"n.供过于求v.狼吞虎咽",
"v.啃，咬",
"n.(缩)国民总收入",
"v.去，进行，打算",
"n.目标，目的，球门",
"n.山羊",
"n.神，上帝",
"n.女神",
"n.黄金，金币，金色",
"adj.黄色的，金黄色的",
"n.高尔夫球",
"adj.好的，善良的",
"int.再见",
"adj.好看的",
"n.优良，天哪",
"n.你方",
"n.货物，商品",
"n.商誉",
"n.鹅",
"n.咽喉，峡谷，山口",
"adj.绚丽的，了不起的",
"n.大猩猩",
"n.闲谈，聊天",
"v.统制，支配，决定",
"n.编制，政体，政府",
"n.女家庭教师",
"n.州长，总督",
"n.长袍，法衣",
"v.抓住，攫取",
"n.优美，文雅，恩惠",
"adj.优美的，文雅的",
"adj.亲切的，客气的",
"n.等级，年级",
"adj.逐渐的，逐步的",
"adv.逐渐地，逐步地",
"v.毕业生v.毕业",
"n.毕业",
"n.谷物，颗粒，一点点",
"n.克",
"n.语法",
"adj.语法的",
"n.留声机",
"adj.雄伟的，重大的",
"n.(外)孙儿、女",
"n.孙女，外孙女",
"n.祖父，外祖父",
"n.祖母，外祖母",
"n.(外)祖父(母)",
"n.孙子，外孙",
"n.花岗石",
"v.答应，授予，承认",
"n.葡萄",
"n.图象，图解",
"v.n.抓住，领悟",
"n.草，禾本植物",
"n.蚱蜢",
"adj.感激的，致谢的",
"v.使满足，使高兴",
"adj.可喜的",
"adj.免费的",
"n.感激，感谢",
"adj.严肃的，庄重的",
"n.砂砾，石子",
"n.引力，严肃",
"v.吃草，擦碰",
"v.润滑油脂",
"adj.大的，伟大的",
"adj.大大地，非常地",
"n.伟大，大",
"n.希腊",
"n.贪婪，贪心",
"adj.贪婪的",
"n.adj.希腊人(的)",
"adj.绿的，没有经验的",
"n.蔬菜商",
"n.温室",
"v.打招呼",
"n.问候，致意",
"adj.灰色的，阴郁的",
"n.悲哀，悲伤",
"v.使悲伤，伤心",
"adj.冷酷的，不祥的",
"v.露齿而笑",
"v.碾碎，磨快，折磨",
"v.n.紧握，吸引",
"vn.呻吟",
"n.杂货铺",
"n.杂货店",
"n.槽，沟，常规",
"v.摸索，探索",
"adj.总的，粗糙的",
"n.地面，场，根据",
"adj.无根据的",
"n.群，组，团体",
"n.林子，树丛",
"v.增长，成长，种植",
"v.n.咆哮，嗥叫",
"adj.已长成的",
"n.成人adj.成人的",
"n.增长，发展，生长",
"v.嫉妒，吝啬",
"v.抱怨，咕哝，发牢骚",
"n.v.(作)呼噜声",
"n.v.保证，担保",
"v.警卫，提防v.哨兵",
"n.保护人",
"v.n.猜想，推测",
"n.客人，宾客，旅客",
"n.宾馆",
"n.向导，指导",
"v.向导，指引n.导游",
"n.犯罪，过失",
"adj.有罪的，内疚的",
"n.吉它，六弦琴",
"n.海湾，鸿沟",
"v.吞下",
"n.树胶，口香糖，牙龈",
"n.枪，炮",
"n.火药",
"n.一阵(大风)",
"n.街沟",
"n.家伙",
"n.体育馆，健身房",
"n.体操",
"n.体操运动员",
"n.习惯",
"adj.习惯的，惯常的",
"adj.消瘦的，憔悴的",
"n.争论，讨价还价",
"v.欢呼n.冰雹",
"n.头发，毛发",
"n.理发",
"n.美发",
"n.发卡",
"adj.毛发的，多毛的",
"n.一半adv.一半",
"adv.半途",
"n.大厅，会堂",
"n.标志",
"v.n.停住",
"v.对分，减半",
"n.火腿",
"n.汉堡包",
"n.锤子v.锤击",
"v.妨碍",
"n.手，人手，指针",
"n.手袋，手提包",
"n.手册",
"adj.一把，少量",
"n.障碍v.妨碍",
"adj.有残疾的",
"n.手帕，手绢",
"v.处理，对待n.把",
"n.处理，管理",
"adj.漂亮的，得体",
"n.分发物(印刷品等)",
"n.手写，书法，笔迹",
"adj.方便的，近便的",
"v.挂，垂，绞死",
"n.衣架",
"adj.偶然的",
"v.发生，碰巧，出事",
"n.事件",
"adv.幸运地",
"n.幸福",
"adj.高兴的，幸运的",
"n.港口，停泊处",
"adj.硬的adv.努力",
"v.硬化，变硬",
"adv.刚刚，几乎不",
"n.坚硬，硬度",
"n.困苦，艰难",
"n.硬件",
"adj.勤劳的",
"adj.耐劳的，耐寒的",
"n.野兔",
"n.v.损害，伤害",
"adj.有害的",
"adj.无害的，无恶意的",
"adj.和睦的，和谐的",
"n.融洽，和谐",
"v.支配，治理",
"adj.刺耳的，严厉的",
"v.n.收获",
"n.急忙，急速",
"v.赶紧，加快",
"adj.急促的，草率的",
"n.帽子",
"v.孵化，策划",
"v.恨，憎恶，不愿意",
"adj.可恨的，可憎的",
"n.憎恶，敌意",
"adj.傲慢的",
"v.拉，拖n.获得量",
"v.萦绕，作崇",
"v.有，不得不，拿",
"n.鹰隼",
"n.干草",
"n.危险",
"pron.他",
"n.头，领导v.率领",
"n.头疼，头疼的事",
"n.标题",
"n.通栏标题",
"ad.头向前地，卤莽地",
"n.(中、小学)校长",
"n.司令部，总部",
"v.治愈，医治",
"n.健康(状况)",
"adj.健康的",
"n.一堆，许多v.堆积",
"v.听见，听取，听说",
"n.听力，审讯",
"n.心，心肠，中心",
"adj.衷心的",
"n.壁炉，炉边",
"adv.精神饱满的",
"adj.衷心的，热诚的",
"n.热，热烈v.加热",
"n.激烈的，热烈的",
"n.取暖，供热",
"v.起伏，举起，叹气",
"n.天空，天堂",
"adv.重，沉重的",
"adj.星的，繁重的",
"n.树篱，套期保值",
"n.刺猬",
"v.n.注意，留心",
"n.后跟",
"n.高度，顶点",
"v.加高，增加",
"n.继承人",
"n.女继承人",
"n.直升飞机",
"n.地狱，苦境",
"int.喂，你好",
"n.头盔",
"v.n.帮助，有助于",
"adj.有用的",
"adj.无用的，无效的",
"n.半球，领域",
"n.母鸡",
"adv.因此，由此",
"adv.今后",
"pron.她的，她(宾格)",
"n.先兆，先驱",
"n.药草",
"adj.草药的",
"v.放牧n.(牲畜)群",
"adv.这里，在这里",
"adv.此后",
"adv.以此",
"adv.在此",
"adv.以下",
"adv.在本文件中",
"adv.对此",
"adv.与此一道",
"n.英雄，男主角",
"adj.英雄的，英勇的",
"n.女英雄，女主角",
"pron.她自己",
"adj.犹豫的",
"v.犹豫，不想",
"n.犹豫，踌躇",
"int.嗨",
"int.嗨，你好",
"v.躲藏，隐瞒，掩盖",
"adj.骇人听闻的",
"adj.高的，高度的",
"n.高地",
"adv.十分，赞许地",
"n.公路",
"v.拦路抢劫",
"n.栏路抢劫者",
"n.v.徒步郊游",
"n.小山，丘陵",
"n.山坡，山腰",
"pron.他(宾格)",
"pron.他自己",
"adj.后面的，后部的",
"v.妨碍，阻止",
"n.内地",
"n.障碍(物)",
"n.合页，绞链",
"n.暗示，迹象v.暗示",
"n.臀部",
"v.租，雇佣",
"pron.他的",
"v.n.(发)嘶嘶声",
"n.历史学家",
"adj.历史性的",
"adj.历史的",
"n.历史",
"v.打，碰，打击",
"v.搭车旅行",
"adv.迄今，到那时",
"adj.嘶哑的，沙哑的",
"n.嗜好，业余爱好",
"n.锄头v.锄",
"v.升起，扯起",
"v.握住，容纳n.控制",
"n.持有人，支架",
"n.支持，控股",
"n.停顿，耽误",
"n.洞，孔穴",
"n.节日，假日",
"adj.空心的，凹陷的",
"adj.神圣的，圣洁的",
"n.家，故乡adv.回家",
"adj.无家可归的",
"adj.家常的，简便的",
"n.思乡的",
"n.家庭作业",
"adj.同质的，同类的",
"adj.诚实的，正直的",
"n.诚实，正直",
"n.蜂蜜",
"n.蜜月",
"n.荣誉，名誉v.尊敬",
"adj.可尊敬的，体面的",
"n.钩v.钩住",
"v.跳跃",
"v.n.希望，愿望",
"adj.有希望的",
"adv.可以指望",
"adj.无望的，绝望的",
"n.地平线，视野",
"adj.水平的，横的",
"n.角，触须，号角",
"adj.可怕的，糟透的",
"v.使恐惧",
"n.恐惧，恐怖",
"n.马",
"n.马力",
"n.软水管，长统袜",
"n.医院",
"adj.好客的",
"n.好客，款待",
"n.一大群，男主人",
"n.人质",
"n.廉价旅馆",
"n.女主人，女主持人",
"adj.怀敌意的",
"adj.热的，辣的",
"n.热狗(面包)",
"n.旅馆",
"n.旅馆业",
"n.小时，点钟",
"n.猎狗v.追逐",
"n.房子，剧场，家",
"n.户adj.家庭的",
"n.看门人，保姆",
"n.家庭主妇",
"n.家务",
"v.翱翔，盘旋，徘徊",
"adv.如何，多么，怎样",
"adv.可是，然而",
"v.n.嚎叫，嚎哭",
"v.n.紧抱",
"adj.庞大的，巨大的",
"n.豆荚，外壳，船壳",
"v.哼，嗡嗡叫",
"adj.人的，人类的",
"adj.人慈的",
"n.人道主义",
"n.慈善家",
"n.人类，人性",
"adj.谦卑的，卑贱的",
"adj.湿的，潮湿的",
"n.湿度，湿气",
"v.使受辱",
"n.羞辱，耻辱",
"n.幽默(感)，心情",
"adj.幽默的，诙谐的",
"num.一百",
"num.第一面，百分之一",
"n.饥饿，渴望",
"adj.饥饿的，渴望的",
"v.打猎，搜索，寻找",
"n.猎人，搜索者",
"v.猛掷，猛投",
"int.好哇n.喝彩声",
"v.赶紧，急忙，急运",
"v.使受伤，使痛，伤害",
"n.丈夫",
"int.嘘n.沉默",
"v.奔忙",
"n.小屋",
"adj.水力的，液压的",
"adj.水电的",
"n.氢，氢气",
"n.卫生",
"n.赞美诗，赞歌",
"n.伪善",
"n.假设，前提",
"adj.假设的",
"n.歇斯底里，癔病",
"adj.亢奋的",
".我",
"n.冰，冰块",
"n.冰淇淋",
"adj.冰封的",
"n.冰岛",
"adj.冰冷的，结了冰的",
"n.思想，主意，打算",
"adj.理想的n.理想",
"n.理想主义",
"v.使理想化",
"adj.同一的，相同的",
"n.识别，身分",
"v.认出，认为...一致",
"n.认同，同一性",
"n.习语，成语",
"adj.习语的，惯用的",
"n.傻子，白痴",
"adj.空闲的，懒的",
"n.闲散，无所事事",
"n.偶像，被崇拜的人",
"(缩)即，也就是",
"conj.如果，虽然是否",
"v.点燃",
"n.无知，不知道",
"adj.不知道的，无知的",
"v.忽视，不理睬",
"adj.患病的，坏的",
"adj.不合法的，非法的",
"adj.字迹不清的",
"n.文盲",
"adj.文盲的n.文盲",
"n.疾病，生病",
"v.照亮，启发",
"n.幻想，幻觉",
"adj.幻觉的",
"v.图解，用图说明",
"n.阐明，实例",
"n.图像，影像，形象",
"adj.想象的，虚构的",
"n.想象力，想象",
"v.想象，猜想",
"v.模仿，仿造，模拟",
"n.模仿，仿制品",
"adj.无形的，不重要的",
"adj.不成熟的",
"adj.立即的，最近的",
"adv.立即，马上",
"adj.巨大的，极大的",
"v.浸泡，埋头于",
"n.移民",
"v.移入",
"n.移居入境",
"adj.迫切的，危急的",
"adj.不道德的",
"adj.不朽的",
"n.冲击，影响",
"v.给予，告诉",
"adj.公证的",
"n.不耐烦",
"adj.急切的，不耐烦的",
"adj.绝对必要的",
"adj.不完善的",
"n.帝国主义",
"n.帝国主义者",
"v.实行n.工具",
"n.实行，执行",
"n.暗示，含义",
"adj.暗含的，暗示的",
"v.恳求，哀求",
"v.暗示，意味",
"v.进口引进n.进口货",
"n.重要性，意义",
"adj.重要的，重大的",
"n.进口",
"n.进口商",
"v.征(税)，强加",
"n.强迫接受",
"n.不可能性",
"adj.不可能的，不妥的",
"n.进口税，关税",
"v.不可行的",
"v.印，铭刻，产生印象",
"n.印象，影响，印迹",
"adj.给人深刻印象的",
"v.关押，监禁",
"n.监禁，徒刑",
"adj.不适当的",
"v.改善，提高",
"n.改善，好转",
"n.冲击，冲动，脉搏",
"n.不纯，杂质",
"prep.在...内，穿戴",
"n.无能",
"adj.很难得到的",
"adj.不准确的，不确切",
"adj.不充足的，不足以",
"adv.因为，由于",
"adj.开幕的",
"v.举行开幕、就职典礼",
"n.开幕、就职典礼",
"adj.不能的，不会的",
"v.使发怒n.香",
"n.刺激的，鼓励的",
"n.英寸",
"n.事件，事变，插曲",
"adv.偶然地，另外",
"n.倾斜，倾向",
"v.低头，喜欢，倾斜",
"adj.倾向于...的",
"v.包括",
"n.包括在内",
"adj.包括在内的",
"n.收入，所得",
"n.不兼容",
"adj.不相容的",
"adj.不完全的，没完成",
"n.不一致",
"adj.不一致的",
"n.不便，不利",
"adj.不方便的",
"v.合并，体现",
"adj.有限的",
"adj.不正确的",
"n.(缩)国际贸易术语",
"v.n.增加，增长",
"adj.不断增长的",
"adv.日益，越来越",
"adj.不可信的，惊人的",
"adj.表示怀疑的",
"n.增值",
"v.招致，承受",
"adj.感激的，感恩的",
"n.感激",
"adv.的确，实际上",
"adj.不明确的，不确定",
"adv.不明确地",
"v.赔偿，保护",
"v.(书写)缩行",
"n.独立，自主",
"adj.独立的",
"adv.独立地",
"n.索引，标志，指数",
"n.印度",
"adj.n.印度人(的)",
"v.指明，表示",
"n.表示，迹象",
"adj.表示...的",
"n.冷淡，不关心",
"adj.冷淡的，不在乎的",
"n.消化不良",
"adj.气愤的，愤慨的",
"n.愤慨，气愤",
"adj.间接的，侧面的",
"adj.间接地",
"adj.必不可少的",
"adj.个人的，各自的",
"adj.室内的",
"adv.在户内，在屋里",
"v.诱使，引起，归纳",
"n.诱导，动机",
"n.感应，归纳",
"v.放纵，放任，纵容",
"adj.工业的",
"v.使工业化",
"n.工业化",
"adj.工业化的",
"adj.勤劳的，勤奋的",
"n.工业，产业，勤奋",
"adj.效率低的",
"n.低效率",
"n.无效力",
"adj.无效的",
"n.惯性，惰性，不活动",
"adj.必然的，不可避免",
"adv.必然地",
"adj.便宜的",
"n.婴儿，幼儿",
"n.步兵",
"v.感染，传染",
"n.感染",
"adj.传染的",
"v.推断，推论",
"n.推断，推论的结果",
"adj.低级的n.下级",
"n.劣势",
"adj.无限大的，无穷的",
"adv.无限地，无穷地",
"adj.不定式的",
"n.无限，无数，极多",
"adj.不易燃的",
"n.充气，通货膨胀",
"v.打击",
"n.影响，势力(范围)",
"adj.有影响的",
"n.流行性感冒",
"v.通知，告诉，告密",
"adj.非正式的",
"n.通知，情报，资料",
"adj.提供资料的",
"adj.不经常的",
"v.侵权",
"n.侵权",
"adj.灵巧的，精巧的",
"adj.独创的，机智的",
"n.灵巧，机灵，巧妙",
"v.居住，栖身",
"n.居民",
"adj.生来俱有的",
"v.继承，遗传",
"adj.最初的",
"adv.最初",
"v.发动，开始，使入门",
"n.积极性，首创精神",
"v.注射",
"n.注射",
"v.伤害，损害",
"n.伤害，损害",
"n.不公正",
"n.墨水，油墨",
"n.内地的，内陆的",
"n.水湾，入口",
"n.客栈",
"adj.里面的，内心的",
"n.清白，天真",
"adj.无罪的",
"v.革新，变革，创始",
"n.革新，创新",
"adj.无数的",
"adj.无机的",
"n.输入，投入",
"v.询问",
"n.询问，查询，调查",
"adj.疯狂的",
"n.昆虫",
"v.插入，嵌入",
"n.插入",
"n.里面adj.里面的",
"n.知情者",
"n.洞察力",
"adj.无足轻重的",
"v.坚持，坚决要求",
"adj.紧迫的，坚持的",
"adv.在...范围内",
"adj.无偿付能力的",
"v.检查，视察，审查",
"n.检查，视察",
"n.检查员，视察者",
"n.灵感",
"v.鼓舞，激励，受启发",
"adj.不稳定的",
"v.安装，安置",
"n.安装，装置",
"n.分期付款",
"n.例子",
"adj.立即的，速溶的",
"adv.立即，立刻",
"adv.代替，而是",
"n.本能，直觉，天性",
"adj.本能的，天性的",
"n.(专科)学院v.建立",
"n.机构，制度",
"v.指导，指示，告知",
"n.指导，指示",
"adj.指示的，教育的",
"n.教员，教练",
"n.仪器，乐器，手段",
"adj.仪器的，工具的",
"adj.不充足的",
"v.绝缘，隔离，使孤立",
"n.隔离，绝缘",
"v.adj.侮辱",
"n.保险(业)，保障",
"v.保险，确保",
"adj.无形的",
"adj.组成的，整体的",
"v.整合，结合",
"n.结合，整体",
"n.完整性，诚实",
"n.理智，才智",
"n.知识分子",
"n.智慧，情报",
"adj.聪明的，明智的",
"v.打算",
"adj.强烈的，极度的",
"n.强烈，强度",
"adj.强化的，密集的",
"n.意图adj.专心的",
"n.意图，目的",
"adj.有意的，故意的",
"v.相互作用，相互影响",
"n.相互作用",
"n.交流，往来",
"n.兴趣，利息，利益",
"adj.感兴趣的",
"adj.有趣的",
"n.交界，接口",
"v.妨碍，干涉",
"n.干涉，干扰",
"n.内部，内地，内政",
"adj.中间的",
"adj.内部的，国内的",
"adj.国际的",
"n.国际化",
"v.使国际化",
"v.解释，当...译员",
"n.解释，口译",
"n.译员",
"v.打断，中断",
"n.中断，打扰",
"n.间隔，中间休息",
"v.介入，调解",
"n.v.会见，面谈",
"adj.亲密的，熟悉的",
"n.亲密，熟悉",
"prep.到...里面，..成",
"n.语调，声调",
"v.介绍，引进，采用",
"n.介绍，引言",
"adj.介绍的，入门的",
"v.侵入，强加于",
"adj.使充满",
"v.入侵，侵犯",
"n.入侵者",
"adj.伤残的，无效的",
"v.使无效",
"adj.非常宝贵的",
"adv.不变地，总是",
"n.侵略，侵袭",
"v.发明，创造，编造",
"n.发明，创造",
"n.发明者",
"adj.相反的，倒转的",
"adv.相反地",
"v.投资，花费",
"v.调查，研究",
"n.调查",
"n.投资(额)",
"adj.看不见的",
"n.邀请(信)",
"v.邀请，招致，征求",
"n.发票，装货清单",
"v.使卷入，忙于",
"adj.涉及的，复杂的",
"n.卷入，涉足",
"adj.里面的，内心的",
"adv.向内的",
"n.爱尔兰iIrishn.adj.爱尔兰人(的)",
"n.铁，熨斗v.熨平",
"adj.反讽的，讽刺的",
"n.反讽，讽刺",
"adj.不规则的",
"n.不规则",
"adj.不可抗拒的",
"adj.不论，不考虑",
"adj.不可撤消的",
"v.灌溉",
"n.灌溉",
"v.使生气，刺激",
"n.刺激，恼怒",
"n.伊斯兰教，回教",
"n.岛屿",
"v.隔离，孤立",
"n.隔离，孤立状态",
"v.发行发布n.发行物",
"pron.它",
"n.adj.意大利人(的)",
"n.意大利",
"v.n.痒，热望",
"n.条款，项目",
"v.分列",
"pron.它的",
"pron.它自己",
"n.象牙，象牙色",
"n.千斤顶，船首旗",
"n.短外套，茄克衫",
"n.监狱v.监禁",
"n.果酱，阻塞",
"n.一月",
"n.日本",
"n.adj.日本人(的)",
"n.罐子，坛子，刺耳声",
"n.下颚，下巴",
"n.爵士乐",
"n.妒忌",
"adj.妒忌的",
"n.牛仔裤",
"n.果冻",
"n.吉普车",
"v.危及",
"n.颠簸，猛推",
"n.耶稣",
"v.喷射v.喷气发动机",
"n.投弃货物v.抛弃",
"n.犹太人",
"n.珠宝，宝石",
"n.珠宝(总称)",
"adj.犹太人的",
"v.n.(发)叮当声",
"n.工作，活儿，差使",
"adj.失业的",
"v.慢跑",
"v.连接，加入，参加",
"n.接着，关节",
"n.笑话v.开玩笑",
"v.匆匆记下",
"n.刊物，日志",
"n.新闻体",
"n.记者",
"n.旅行，旅程",
"n.高兴，乐事",
"adj.令人高兴的",
"n.法官，裁判v.审判",
"n.判决，意见，判断",
"n.大壶，罐",
"n.汁，液",
"adj.多汁的",
"n.七月",
"n.搞乱，混乱",
"v.n.跳跃，跳动",
"n.连接，结合处，接头",
"n.六月",
"n.密林，热带丛林",
"adj.年少的，低级的",
"n.木屋",
"n.陪审团，评奖团",
"adv.只，刚才",
"n.公正，正直",
"adj.有理由的",
"n.辩护，正当理由",
"v.认为...有理",
"adj.青少年的",
"n.带鼠",
"adj.锋利的，敏捷的",
"v.保持，保留，防止",
"n.保管人，管理员",
"n.一致，协调",
"n.核(仁)，核心",
"n.煤油",
"n.水壶",
"n.钥匙，关键，答案",
"n.键盘",
"n.钥匙孔",
"v.n.踢",
"n.小孩v.哄骗",
"v.绑架，诱拐",
"n.绑架者",
"n.肾，腰子",
"v.杀死，杀害",
"n.杀人者，杀手",
"n.(缩)公斤，公里",
"n.公斤",
"n.公里",
"n.千瓦",
"n.种类adj.仁慈的",
"n.幼儿园",
"v.点燃，激发",
"adv.仁慈地，好心地",
"n.仁慈，好意",
"n.国王",
"n.王国",
"v.接吻，亲嘴",
"n.全套工具、装备",
"n.厨房",
"n.风筝",
"n.膝",
"v.跪下",
"n.小刀",
"n.骑士，爵士",
"v.编织，皱(眉)",
"n.球形把手",
"v.敲，击倒n.敲门声",
"n.结，树节v.打结",
"n.知道，认识，懂",
"n.专项技术，诀窍",
"n.知识，学识",
"adj.博学的",
"n.(缩)实验室",
"n.标签v.标明",
"n.实验室",
"n.劳动，劳动力",
"n.劳工，劳动者",
"adj.劳动密集型的",
"n.花边，鞋带",
"v.n.缺少",
"n.少年，小伙子",
"n.梯子，阶梯",
"n.女士，贵妇人，夫人",
"v.n.落后，滞后",
"n.湖，湖泊",
"n.羔羊，小羊肉",
"adj.跛的，站不住脚的",
"n.灯",
"n.陆地，土地v.着陆",
"adj.卸货的",
"n.楼梯平台，着陆",
"n.女房东",
"n.房东，地主",
"n.风景(画)，地形",
"n.小巷，跑道，行车道",
"冷甲(馬來西亞霹靂洲内一地方名)",
"n.语言",
"n.灯笼",
"n.膝盖",
"v.(时间)流失",
"adj.大的，巨大的",
"adv.大部分，基本上",
"n.云雀，百灵鸟",
"n.激光",
"adj.最后的adv.上次",
"adj.持久的，持续的",
"adj.迟到的，晚的",
"adv.近来，最后",
"adj.潜伏的，潜在的",
"adv.更晚，以后，过后",
"adj.横向的，侧向的",
"n.车床",
"n.adj.拉丁语(的)",
"n.纬度，活动余地",
"adj.后面的，后者的",
"n.结构，点阵",
"v.笑，嘲笑",
"n.笑，笑声",
"v.发射，发动，开始",
"n.洗衣店，送洗的衣物",
"n.盥洗室，厕所",
"n.法律，定律",
"adj.合法的，法律的",
"n.草地，草坪",
"n.律师，法学家",
"v.放，安排，打基础",
"n.装卸日期",
"n.层，层次",
"n.设计，规划，图案",
"n.懒惰",
"adj.懒惰的",
"n.(缩)信用证",
"v.引导，领先，率领",
"n.领导，领袖",
"n.领导",
"adj.领先的，一流的",
"n.叶子，页",
"n.传单，单页宣传品",
"n.同盟，协会",
"v.漏，泄漏",
"n.渗漏",
"v.俯身，倚adj.瘦的",
"v.n.跳跃adj.闰年的",
"v.学习，获悉",
"adj.有学问的",
"n.学习者，学生",
"n.学问，学习",
"v.租凭，出租n.租约",
"adj.最少的",
"n.皮革adj.皮革制的",
"v.出发，离开n.休假",
"n.v.演讲，讲课",
"n.演讲者，讲师",
"adj.活动余地",
"adj.左的adv.向左",
"adj.左手的，左侧的",
"n.剩余物",
"n.腿，裤脚",
"adj.合法的，法律的",
"n.传说，传奇",
"adj.传说的，传奇的",
"n.立法，法规",
"adj.合法的，合理的",
"n.合法",
"n.闲暇，闲空",
"n.柠檬",
"n.柠檬汽水",
"v.出借，贷款",
"n.贷款，借款",
"n.长度，期限",
"v.延长，变长",
"n.列宁主义",
"n.透镜，镜片，晶体",
"n.豹",
"adj.更少的adv.较小",
"v.减少，变小，变弱",
"n.功课，课程，教训",
"prep.唯恐，以免",
"v.让，使",
"n.字母，信，函件",
"n.水平，级v.弄平",
"n.杠杆",
"v.征税n.关税",
"n.责任，义务，债务",
"adj.有责任的",
"n.说谎者",
"adj.思想开放的",
"v.解放，释放，使自由",
"n.解放",
"n.自由",
"n.图书管理员",
"n.图书馆，藏书",
"n.许可(证)，执照",
"v.舔",
"n.盖，脸",
"v.躺，位于v.n.说谎",
"n.中尉，副职",
"n.生活，生命，一生",
"n.一生",
"v.举起，吊n.电梯",
"n.光，灯adj.明亮的",
"v.发亮，使...愉快",
"n.打火机",
"n.灯塔",
"adv.轻轻地，轻易地",
"n.闪电",
"v.喜欢prep.像",
"n.可能，相似性",
"adj.可信的adv.很可能",
"n.相像，类似",
"adv.同样，照样",
"n.兴趣，嗜好",
"n.百合，睡莲",
"n.肢，树枝",
"n.石灰",
"n.石灰岩",
"n.界限，限度v.限制",
"n.限制，局限",
"adj.有限的，限定的",
"n.豪华轿车",
"adj.柔软的v.跛行",
"n.行，线条，界线",
"adj.线性的，线状的",
"n.亚麻(织物)",
"n.班轮，班机",
"v.徘徊，逗留，拖延",
"n.语言学者",
"n.语言学",
"n.夹里，衬里",
"v.联系，连结n.纽带",
"n.狮子",
"n.母狮子",
"n.嘴唇",
"n.口红，唇膏",
"n.液体adj.液体的",
"n.烈性酒",
"n.表，名单v.列表",
"v.听，听从",
"n.听者",
"n.识字",
"adj.字面的，不夸张的",
"adv.简直，字面上",
"adj.文学的",
"n.有文化的",
"n.文学，文献",
"n.公升",
"v.乱丢废物n.废物",
"adj.小的，一点，少的",
"v.居住生存adj.活的",
"n.生活",
"adj.活跃的，热闹的",
"n.肝",
"n.牲畜",
"adj.活着的n.生计",
"n.客厅，起居室",
"n.负载，负担v.装载",
"n.面包v.游荡",
"n.贷款v.出借",
"n.前厅v.游说",
"n.龙虾",
"adj.地方的，当地的",
"n.地点，现场",
"v.找出，确定地点",
"n.地点，位置",
"v.锁上n.锁，绺",
"n.锁，固定资本",
"n.火车头，机车",
"n.蝗虫",
"v.寄宿",
"n.住处，住房",
"adj.崇高的，高耸的",
"n.原木，航海日志",
"n.逻辑，论理学",
"adj.逻辑的",
"n.孤独，寂寞",
"adj.孤独的，寂寞的",
"adj.寂寞的",
"adj.长的adv.长久",
"n.长寿",
"n.渴望，思慕",
"n.经度，经线",
"adj.长期的",
"v.看，看上去n.外表",
"v.隐隐出现n.织布机",
"n.环，回路v.环绕",
"adj.松的，自由自在的",
"v.解开，放松",
"n.君主，贵族，上帝",
"n.卡车，载重汽车",
"v.失去，丢失，输",
"n.丧失，失利，损失",
"adj.失去的",
"n.许多，地adv.相当",
"n.抽彩，抓阄，彩票",
"adj.响亮的，大声的",
"n.响亮",
"n.扬声器，扩音器",
"n.休息室",
"adj.可爱的",
"v.爱，喜欢n.爱情",
"adj.好看的，可爱的",
"n.爱人，情人，爱好者",
"adj.低的，低廉的",
"v.降低，减弱",
"adj.忠诚的，忠贞的",
"n.忠诚，忠贞",
"v.润滑",
"n.润滑",
"n.运气，幸运",
"adj.幸运的",
"n.行李",
"n.木材，木料",
"adj.发光的，明晰的",
"n.块，肿块",
"n.总数",
"adj.月亮的，阴历的",
"n.午饭，便餐",
"n.午餐，午宴",
"n.肺",
"adj.豪华的，奢侈的",
"n.奢侈(品)",
"n.机器",
"n.机械(总称)",
"n.雨衣",
"n.宏观经济学",
"adj.疯狂的，狂热的",
"n.夫人，太太，女士",
"nn.疯子",
"n.疯狂，疯病",
"n.杂志，期刊",
"n.魔法，魔术，魅力",
"n.魔术师",
"n.地方法官",
"n.磁性，磁铁",
"adj.磁性的",
"n.磁性，磁力，吸引力",
"adj.壮丽的，宏伟的",
"v.放大，扩大",
"n.宏大，重要(性)",
"n.女仆，侍女",
"n.少女adj.未婚的",
"n.邮件v.邮寄",
"n.信箱",
"adj.主要的",
"n.大陆，本土",
"adv.主要地，大部分",
"n.主流",
"v.维持，保养，坚持",
"n.保养，维修",
"n.玉米",
"n.陛下，雄伟，庄严",
"adj.主要的，多数的",
"n.多数，过半数",
"v.做，制造n.种类",
"n.制造者，制造商",
"adj.临时的n.权宜之计",
"n.气质，化妆品",
"n.病",
"n.疟疾",
"n.马来西亚",
"n.马来西亚",
"adj.男性的，雄的",
"n.恶意，恶感",
"adj.恶意的",
"n.人，男人，人类",
"v.管理，处理，设法",
"n.管理(人员)，经营",
"n.经理",
"adj.管理的",
"n.男子气",
"v.表明adj.明白的",
"n.表明",
"n.宣言",
"v.操纵，操作，摆布",
"n.操纵，操作",
"n.人类",
"adj.大丈夫的",
"n.方法，方式，礼貌",
"n.宅第，官邸，大厦",
"adj.用手的n.手册",
"v.n.制造",
"adj.制成的",
"n.制造商",
"n.手稿，原稿",
"adj.许多的n.许多",
"n.地图v.筹划",
"n.枫树",
"n.大理石，弹子",
"n.三月",
"n.v.行进，行军",
"n.余地，边缘",
"adj.边缘的，边际的",
"adj.海的，海生的",
"n.海员，水手",
"n.痕迹，符号，标记",
"adj.有标记的，标明的",
"n.市场，销路",
"adj.有销路的",
"n.市场学，营销学",
"n.市场，集市",
"n.唛头，标记",
"n.婚姻，婚礼",
"adj.已婚的",
"v.娶，嫁，为...主婚",
"n.火星",
"n.沼泽",
"n.元帅",
"n.烈士，殉道者",
"n.奇迹v.惊奇",
"adj.奇异的，绝妙的",
"n.马克思主义",
"n.马克思主义者",
"adj.男性的，阳性的",
"n.假面具v.掩饰",
"n.堆，大量，群众",
"n.v.屠杀，残杀",
"n.按摩，推拿",
"adj.粗大的，厚重的",
"median.传媒工具，新闻界",
"n.桅杆",
"n.主人，大师，硕士",
"n.杰作",
"n.垫子，席子",
"n.火柴，对手，比赛",
"n.伙伴v.配对",
"n.材料，资料，原料",
"n.唯物主义",
"v.使具体化，物质化",
"adj.数学的",
"n.数学",
"n.数字家",
"n.(缩)数学",
"n.日场演出",
"n.事情，物资，毛病",
"n.床垫",
"adj.成熟的，到期的",
"n.成熟，到期",
"v.增加到最大程度",
"n.最大量，极限",
"n.五月",
"v.可以，也许，祝愿",
"adv.或许，大概",
"n.市长",
"pron.我(宾格)",
"n.牧场，草地",
"n.膳食，一顿饭",
"v.打算，意指",
"n.意义，意图",
"n.手段，财力",
"adv.同时，在这期间",
"adv.n.在这期间",
"n.尺寸，量具，措施",
"n.测量(结果)",
"n.肉",
"n.技工",
"adj.机械的、机动的",
"adv.机械地",
"n.力学，机械学",
"n.机制，机械装置",
"n.奖章，勋章，纪念章",
"adj.医学的，医务的",
"n.药，医学",
"adj.中世纪的",
"v.考虑，沉思",
"n.考虑，沉思冥想",
"n.地中海",
"n.中间，媒介，中庸",
"adj.温顺的",
"v.遇到，会见，迎接",
"n.会议，集会",
"n.adj.忧郁(的)",
"n.旋律，曲调",
"n.瓜，甜瓜",
"v.熔化，融解",
"n.成员，会员",
"n.会员资格，全体成员",
"n.备忘录",
"n.回忆录",
"adj.纪念的，追悼的",
"v.记住，记忆",
"n.记忆(力)，回忆",
"v.n.威胁，恐吓",
"v.修理，修补，好转",
"adj.心理的，精神的",
"n.心理，意识",
"v.n.提及，讲到",
"n.菜单",
"n.商品，货物",
"n.商人adj.商业的",
"n.商品",
"adj.仁慈的，宽大的",
"n.水星",
"n.汞，水银",
"n.宽大，慈悲，怜悯",
"adj.仅仅的，起码的",
"adv.仅仅，只",
"v.合并",
"n.价值，功绩v.应得",
"n.美人鱼",
"adj.欢乐的",
"n.网孔，筛眼",
"n.肮脏，凌乱v.弄脏",
"n.音讯，消息",
"n.通讯员，使者",
"n.金属",
"adj.金属的",
"n.冶金学",
"n.量器，仪表",
"n.方法",
"n.方法(论)",
"adj.小心翼翼的",
"adv.胆小地",
"n.米，公尺",
"adj.公制的，米的",
"n.大都市",
"n.adj.墨西哥人(的)",
"n.墨西哥",
"n.微观经济学",
"n.扩音器，话筒",
"n.微处理机",
"n.显微镜",
"n.微波",
"n.正午，晌午",
"n.当中adj.中部的",
"n.中人，中间人",
"n.中等的，第二流的",
"n.午夜",
"n.中间，中部",
"v.或许，可以n.力",
"adj.强有力的",
"adj.迁移的，候鸟的",
"v.迁移(海外)，移栖",
"n.迁移，移居海外",
"adj.温和的，味淡的",
"n.英里",
"n.里程",
"n.里程碑",
"adj.军事的，好斗的",
"n.民兵(组织)",
"n.奶，ru夜v.挤奶",
"n.送奶人",
"adj.加奶的，ru白色的",
"n.磨坊，工厂v.滚乱",
"n.磨坊主",
"n.毫米",
"n.百万",
"n.百万富翁",
"v.切碎，绞碎",
"n.粉碎机",
"n.头脑，智力v.介意",
"pron.我的n.矿山",
"n.矿工",
"n.矿物adj.矿物的",
"v.混合，混入",
"n.雏形，缩影，袖珍",
"n.微型计算机",
"v.使减到最小",
"n.最少量adj.最小的",
"n.教士，部长，大臣",
"n.(政府)部",
"adj.较小的，次要的",
"n.少数，少数民族",
"n.造币厂，薄荷",
"prep.减去adj.减的",
"n.分钟，片刻",
"n.奇迹，令人惊讶的事",
"adj.奇迹(般)的",
"n.镜子v.反映",
"n.未到目的地",
"v.未运到(目的地)",
"n.伤害，恶作剧",
"n.吝啬鬼，守财奴",
"adj.悲惨的，糟糕的",
"n.痛苦，悲惨，苦难",
"n.不幸",
"n.疑虑，担心",
"v.装卸不慎",
"n.事故",
"v.误解",
"v.引入岐途",
"v.未击中错过n.小姐",
"n.导弹，发射物",
"adj.丢失的，缺少的",
"n.使团，使命，天职",
"n.传教士",
"n.薄雾v.使迷糊",
"n.错误，误解v.搞错",
"adj.搞错了的，误解的",
"n.先生(缩写为Mr.)",
"n.女主人，情妇",
"adj.雾蒙蒙的，有雾的",
"v.误解，误会",
"n.误会，曲解",
"n.连指手套，露指手套",
"v.混合，配料，交往",
"n.混合器",
"n.混合物，混和",
"v.n.呻吟，悲叹",
"n.暴民，乌合之众",
"adj.机动的，流动的",
"v.动员",
"v.嘲笑，愚弄",
"n.方式，方法",
"n.模范，模型，模特儿",
"adj.适度的v.缓和",
"adv.适度地，适中地",
"adj.现代的，时髦的",
"n.现代化",
"v.使...现代化",
"adj.谦虚的，质朴的",
"n.谦虚",
"n.修改，缓和",
"adj.改良的，改进的",
"v.修改，减轻，修饰",
"v.调整，改变",
"n.模量，模件",
"adj.潮湿的",
"n.潮气",
"adj.分子的",
"n.分子",
"n.时刻，瞬间",
"adj.片刻的，瞬间的",
"adj.重要的，重大的",
"n.君主，王室",
"adj.修道院，寺院",
"n.星期一",
"adj.货币的，金融的",
"n.金钱，货币，财富",
"n.班长监视器v.监视",
"n.和尚，修道士",
"n.猴子",
"v.垄断，独占",
"n.垄断，独占",
"adj.单调的，枯燥的",
"n.单调，枯燥",
"n.怪兽，怪物，魔鬼",
"adj.可怕的，极恶的",
"n.月份",
"adj.每月的n.月刊",
"n.纪念章，不朽之物",
"adj.纪念碑式的",
"n.心情，心境，情绪",
"n.月亮",
"n.月光",
"n.业余干活",
"v.系泊，把船栓定",
"n.拖把，墩布",
"adj.道德的n.教训",
"n.士气，斗志",
"n.道德品质",
"adj.更多的更adv.更",
"adv.此外，而且",
"n.早晨，上午",
"adj.致命的",
"n.adj.穆斯林",
"n.清真寺",
"n.蚊子",
"n.苔藓，地衣",
"adj.最多的adv.非常",
"adv.主要地，大多",
"n.汽车旅馆",
"n.蛾",
"n.母亲adj.出生地的",
"n.岳母，婆婆",
"n.运动，议案",
"adj.不动的",
"v.促进，激发",
"n.动机",
"n.动机",
"n.发动机",
"n.汽车",
"n.摩托车",
"n.摩托车手",
"n.汽车道，高速公路",
"n.座右铭",
"n.模子，型，霉菌",
"n.山，岳v.登上",
"n.山",
"adj.多山的，山一般的",
"v.悲悼，哀痛",
"adj.悲悼的，哀痛的",
"n.哀痛",
"n.老鼠",
"n.胡子，须",
"n.口，嘴巴，河口",
"n.一口，满口",
"v.移动，推动，搬家",
"n.活动，运动，动作",
"n.电影(院)",
"n.(缩)先生",
"n.(缩)夫人，太太",
"n.(缩)女士",
"adj.许多的n.许多",
"n.泥浆",
"adj.泥泞的",
"v.裹住，捂住",
"n.围巾，消音器",
"n.(有柄)大杯",
"n.骡子",
"adj.复合的，多次方的",
"n.乘法，增加",
"v.乘，增加，繁殖",
"n.多功能的",
"n.大批，大群",
"adj.市的，市政的",
"v.咕哝，嘟囔",
"n.腮腺炎",
"v.",
"",
"n.凶手，杀人犯",
"v.低声说",
"n.筋，肌肉",
"adj.肌肉发达的",
"v.沉思，默想",
"n.博物馆，陈列馆",
"n.“蘑菇",
"n.音乐，乐曲",
"adj.音乐的n.歌舞片",
"n.音乐家，作曲家",
"v.必须，准是n.必须",
"n.芥末",
"adj.缄默的n.哑巴",
"v.咕哝，抱怨",
"n.羊肉",
"adj.相互的，共同的",
"pron.我的",
"n.",
"",
"pron.我自己，我亲自",
"adj.神秘的，玄妙的",
"n.神秘，奥妙，秘事",
"adj.神秘的",
"n.神话",
"n.神话(学)",
"n.钉子，指甲v.钉",
"adj.天真的",
"adj.裸体的，赤裸裸的",
"n.姓名，名称v.命名",
"adj.无名的",
"adv.即，也就是",
"n.名义",
"n.打盹，小睡",
"n.餐巾(纸)",
"v.叙述",
"n.叙述",
"n.叙述者",
"adj.狭窄的，勉强的",
"adj.肮脏的，下流的",
"n.国家，国民，民族",
"adj.民族的，国家的",
"n.国籍",
"adj.本国的，出生地的",
"adj.自然的，通常的",
"adv.自然地",
"n.自然，本性，性质",
"adj.淘气的，顽皮的",
"v.恶心，讨厌",
"adj.海军的",
"n.脐，中心",
"adj.可航行的",
"n.航行，航海，航空",
"n.海军",
"adv.近adj.近的",
"adj.adv.附近(的)",
"adv.几乎，差不多",
"adj.整洁的，简洁的",
"adv.必然，当然",
"adj.必要的，必然的",
"v.使需要，强迫",
"n.必要性，必须品",
"n.颈，脖子",
"n.项链",
"n.需要，贫困v.需要",
"adj.必要的",
"n.针，指针，针叶",
"adj.不必要的，无用的",
"adj.贫穷的",
"v.否定",
"n.否定",
"adj.否定的n.负片",
"v.n.疏忽，忽视",
"n.疏忽，过失",
"adj.粗心大意的",
"adj.微不足道的",
"adj.可谈判的",
"v.谈判，交涉",
"n.谈判",
"n.黑人(贬义)",
"n.邻居，邻国",
"n.邻里，街坊",
"adj.邻近的，相邻的",
"conj.既不...又不...",
"n.侄子，外甥",
"n.神经，胆量",
"adj.神经(质)的，",
"n.巢，窝",
"v.安顿，建巢",
"n.网adj.净的，纯的",
"n.网络，网状组织",
"adj.中立的，中和的",
"n.中立",
"n.中子",
"adv.从不，永不，未曾",
"adv.还是，然而",
"adj.新的，重新的",
"n.新闻，消息",
"n.报纸，新闻纸",
"adv.下一次，然后",
"adj.令人愉快的",
"n.镍，镍币",
"n.绰号，诨号",
"n.侄女，外甥女",
"n.夜，黑夜",
"n.睡衣",
"n.夜莺",
"n.恶梦",
"num.九",
"num.十九",
"num.九十",
"num.第九，九分之一",
"n.氮",
"adv.不毫不adj.没有",
"n.(缩)...号，号码",
"n.高贵，庄严",
"adj.高尚的，贵族的",
"prep.谁也不",
"v.n.点头",
"n.噪音，吵嚷声",
"adj.吵闹的",
"adj.名义上的，票面的",
"v.提名，推荐，任命",
"n.提名，任命",
"prep.没人，毫无",
"n.废话，谬论",
"n.中午，正午",
"conj.也不，也没",
"n.标准，规范，定额",
"adj.正常的，标准的",
"n.正常化",
"v.使正常，使标准化",
"adv.正常地，通常",
"n.北，北方adj.北的",
"adj.n.东北(的)",
"adj.北方的，北部的",
"adj.adv.向北(的)",
"adj.n.西北(的)",
"n.鼻子",
"n.鼻孔",
"adv.不",
"adj.值得注意的",
"adj.尤其，值得注意地",
"n.笔记，注释，便条",
"n.笔记本",
"adj.著名的",
"n.笔记，笔录",
"n.没有东西adv.毫不",
"v.留意n.注意，通知",
"adj.显而易见的",
"n.通知(书)，布告",
"v.通知，通告，报告",
"n.概念，意见，看法",
"adj.臭名昭著的",
"prep.conj.尽管",
"n.零",
"n.名词",
"v.养育，提供养分",
"n.食物，补品",
"adj.新颖的n.小说",
"n.小说家",
"n.中篇小说",
"n.新奇，新颖",
"n.十一月",
"adv.n.现在conj.既然",
"adv.现今，目前",
"adv.哪儿也不",
"adj.核的，原子核的",
"n.(原子)核，核心",
"n.令人讨厌的人或事",
"n.无",
"v.使无效，取消",
"n.数字，若干，号码",
"adj.数字的",
"adj.众多的，大量的",
"n.修女，尼姑",
"n.护士，保姆v.护理",
"n.托儿所，苗圃",
"n.坚果，螺母",
"n.尼龙",
"n.橡树，栎树",
"n.橹，桨",
"n.誓言，誓约",
"n.服从，顺从",
"adj.服从的，顺从的",
"v.服从，遵守",
"n.物体，目的v.反对",
"n.反对，异议，不愿",
"n.目标adj.客观的",
"n.义务，责任",
"v.责成，使感激",
"adj.删去，抹掉",
"adj.椭圆形的",
"adj.无名的v.遮蔽",
"n.仪式，习惯",
"n.观察，评述",
"v.观察，遵守，注视",
"n.观察员",
"n.障碍(物)",
"adj.固执的，顽强的",
"n.堵塞，妨碍",
"v.获得",
"adj.可得到的",
"adj.明显的",
"adv.明显地，显然",
"n.场合，盛事，机会",
"adj.偶然的，有时的",
"adv.偶而，有时",
"n.西方",
"adj.西方的，西洋的",
"n.职业，占有",
"v.占据，占领，担任",
"v.发生，出现，想到",
"n.发生，出现，事件",
"n.海洋，大洋",
"n.大洋洲",
"n.海洋学",
"adv.点钟",
"n.十月",
"adj.古怪的，奇数的",
"n.气味",
"prep..的(表示领属等)",
"adv....去prep.离开",
"adj.不当班的",
"n.过错，冒犯，攻击",
"v.冒犯，得罪",
"adj.冒犯的，攻击的",
"v.n.提供，报盘",
"n.报盘，提供的货物",
"adj.等外的，质差的",
"n.办公室，事务所",
"n.军官，警官，官员",
"n.官员adj.官方的",
"v.抵消，弥补",
"n.子女，子孙",
"adv.经常，常常",
"int.哦，嗬",
"n.油，石油",
"adj.n.(缩)对，行",
"adj.老的，...岁的",
"n.橄榄(树)",
"n.前兆",
"adj.不祥的",
"n.省略",
"v.省略，遗漏",
"prep.在...上，关于",
"adv.一度，一次",
"num.n.一，一个",
"pron.自己，自身",
"n.洋葱",
"adj.唯一的adv.仅仅",
"n.攻击，着手",
"prep.到...上",
"adv.adj.向前(的)",
"n.蛋白石",
"adj.不透明的",
"adj.开的v.打开",
"n.开罐器，起子",
"n.开始，通路，孔",
"n.歌剧",
"v.运转，操作，开刀",
"n.操作，生效，手术",
"adj.业务上的，操作的",
"adj.有效的",
"n.操作人员，接线员",
"n.意见，评论，看法",
"n.鸦片",
"n.对手，敌手",
"adj.及时的，凑巧的",
"n.机会，机遇，时机",
"v.反对，反抗",
"adj.对立的，对面的",
"n.敌对，反抗",
"v.压抑，压迫，压制",
"n.压迫",
"adj.视觉的，光学的",
"adj.最佳的",
"n.乐观(主义)",
"adj.乐观(主义)的",
"v.最佳化",
"n.最佳条件",
"n.选择，可选择的东西",
"adj.可任选的，随意的",
"conj.或者，即，否则",
"adj.口头的，口的",
"n.柑桔，橙色",
"n.轨道",
"n.果园",
"n.管弦乐队，交响乐",
"n.命令，订货，次序",
"adj.整齐的n.勤务员",
"adv.通常",
"adj.普通的，一般的",
"n.矿石，矿物",
"n.器官，风琴",
"adj.器官的，有机的",
"n.有机体",
"n.组织，团体",
"adj.组织的",
"v.组织，筹备，编排",
"n.东方v.定方针",
"adj.n.东方的(人)",
"n.定向，倾向性",
"n.起源，产地",
"adj.原始的n.原物",
"n.独创性",
"adv.原来，当初",
"v.起源，首创",
"n.装饰(品)",
"adj.装饰的",
"n.孤儿",
"n.摆动，振动",
"adj.其他的，别的",
"adv.另外的conj.否则",
"v.应该，大概",
"n.盎司",
"pron.我们的",
"pron.我们自己",
"adv.出外，向外，完",
"n.爆发，发作",
"n.结果",
"adj.野外的，露天的",
"adv.在外的，在野外的",
"adj.外部的，外面的",
"adj.最外的",
"n.偏僻地区",
"adj.外国的",
"n.逃犯，歹徒",
"n.费用，支出",
"n.出口，销路",
"n.轮廓，略图，大纲",
"n.看法，景色，展望",
"n.出产，产量",
"n.暴行",
"adj.残暴的",
"adj.公然地，直率地",
"n.开头，起初",
"n.外部adv.在外面",
"n.局外人",
"n.郊区",
"adj.杰出的，未付款的",
"n.卸货情况",
"adj.adv.向外(的)",
"adj.椭圆(形)的",
"n.烤炉，锅灶",
"prep.在...上方，越过",
"adj.总的，全面的",
"adj.多云的",
"v.n.多收(的)钱",
"n.外套，大衣",
"v.征服，克服，压倒",
"v.估计过高",
"v.使..承担过多的义务",
"v.泛滥，溢出，满怀",
"adv.adj.头上(的)",
"v.偶然听到，偷听",
"n.使大喜",
"v.重叠",
"adj.相互重叠的",
"v.n.超载",
"v.视察，俯瞰，宽容",
"adv.adj.终夜(的)",
"n.多付的款项",
"adv.adj.海外(的)",
"n.监视，疏忽",
"v.赶上，压倒",
"v.推翻，颠覆",
"n.超时，加班",
"v.压倒，淹没",
"adj.压倒的",
"v.欠，归功于",
"adj.该付的",
"n.猫头鹰",
"adj.自己的v.拥有",
"n.物主，所有人",
"n.所有权，所有制",
"n.公牛",
"n.氧化物",
"n.氧，氧化",
"n.牡蛎，蚝",
"n.步，速度，步调",
"n.太平洋",
"v.包装，挤满n.背包",
"n.包裹v.打包",
"n.包装",
"n.一盒，小件包裹",
"n.装箱，收拾行李",
"n.垫，便笺本",
"n.(书)页",
"n.提桶",
"n.疼痛，悲痛v.作痛",
"adj.痛苦的",
"n.涂料，油漆v.刷漆",
"n.画家，油漆匠",
"n.画，绘画(艺术)",
"n.对，双，夫妇",
"n.宫殿",
"adj.苍白的，淡的",
"n.手掌，掌心，棕榈树",
"n.小册子",
"n.平底锅",
"n.熊猫",
"n.窗(门)玻璃",
"n.镶板，仪表盘，小组",
"n.v.恐慌，惊慌",
"n.全景",
"adj.全景的",
"n.v.喘气",
"n.豹，美洲豹",
"n.配膳室，食品室",
"n.长裤，衬裤",
"n.纸，报纸，文件",
"n.剪纸，刻纸",
"n.剪纸艺术",
"n.文件，证书",
"n.(跟)原价相等",
"n.降落伞",
"n.v.游行",
"n.天堂，天国",
"n.段落，节",
"adj.平行的，类似的",
"v.使麻痹，惊呆",
"n.参数，参量",
"n.寄生虫，寄生物",
"n.包裹，邮包",
"n.v.原谅，赦免",
"n.父或母亲，母体",
"n.巴黎",
"n.教区",
"n.公园v.停放车辆",
"n.停放车辆",
"n.议会，国会",
"adj.国会的，议会的",
"n.客厅",
"n.鹦鹉",
"n.部分，零件，角色",
"adj.局部的，偏颇的",
"adv.局部地，部分地",
"n.参加者，参与者",
"v.参与，分享",
"n.参加，参与",
"n.颗粒，微粒，虚词",
"adj.特殊的n.项目",
"adv.特别地",
"v.n.划分，隔开",
"adv.部分地",
"n.伙伴，合伙人，搭档",
"n.伙伴关系，合伙",
"adj.计时(干活)的",
"n.聚会，政党，一方",
"v.经过，传给n.关口",
"adj.过得去的",
"n.一段，通过，通道",
"n.旅客，乘客",
"n.激情，热衷",
"adj.多情的，热烈的",
"adj.被动的，消极的",
"n.护照",
"adj.过去的n.过去",
"adj.过期的",
"n.浆糊，糊状物",
"n.消谴，娱乐",
"n.牧场",
"n.v.轻拍，抚摸",
"n.补丁，眼罩",
"n.专利权，专利证",
"n.小径，路线",
"adj.凄婉动人的",
"n.耐心，忍耐力",
"adj.耐心的n.病人",
"n.爱国者",
"adj.爱国的",
"n.爱国主义",
"v.巡逻n.巡逻队",
"n.赞助人，保护人",
"n.保护人身分",
"n.模式，式样，图案",
"v.n.暂停，中止",
"v.铺路，为..铺平道路",
"n.人行道",
"n.脚瓜",
"v.产卵",
"v.支付n.工资",
"adj.支付给...的",
"n.支付，付款",
"n.豌豆",
"n.和平，平静，和约",
"adj.和平的，平静的",
"n.桃子",
"n.孔雀",
"n.顶点，巅，山峰",
"n.花生",
"n.梨",
"n.珍珠",
"n.农民",
"n.农民(总称)",
"n.鹅卵石",
"v.啄",
"adj.古怪的，独特的",
"n.特性，怪癖",
"n.踏板v.骑车",
"n.行人",
"n.小贩",
"n.果皮v.削、剥皮",
"v.偷看，窥视",
"n.同行v.盯，凝视",
"n.桩v.(汇率)钉住",
"n.钢笔，栏，圈",
"n.刑罚，处罚，罚款",
"n.铅笔",
"adj.未决的，紧迫的",
"v.贯穿，穿透，弥漫",
"n.贯穿，洞察力",
"n.青霉素，盘尼西林",
"n.半岛",
"n.便士",
"n.养老金，年金",
"n.人们，人民，人员",
"n.胡椒",
"prep.每，由，按照",
"v.知觉，觉察，领悟",
"n.每百，百分之",
"n.百分率",
"n.感觉，理解力",
"v.栖息",
"adj.完美的，完备的",
"n.完成，完善",
"adv.完全地，完美地",
"v.执行，表演",
"n.执行，演出",
"n.执行者，表演者",
"n.香味，香水",
"adv.也许，多半",
"n.危难，巨大危险",
"n.周长",
"n.时期，句号",
"adj.周期的，定时的",
"n.期刊",
"adj.边缘的，周边的",
"v.死亡，枯萎",
"n.永久，持久",
"n.永久性的，持久的",
"adv.永久地",
"n.允许，许可",
"adj.允许的，许可的",
"v.允许n.许可证",
"adj.垂直的",
"adj.永久的，永恒的",
"v.迷惑，难住",
"v.迫害",
"n.迫害",
"v.坚持",
"n.坚持",
"v.坚持，固执，持续",
"n.坚持，持续",
"n.人，人称，身体",
"adj.私人的，个人的",
"n.人格，个性，人物",
"adv.亲自，就个人而言",
"n.全体人员，人事部门",
"n.展望，观点，透视",
"v.说服，劝导",
"n.说服，信念",
"v.属于",
"n.中肯",
"adj.中肯的，恰当的",
"v.扰乱",
"adj.烦燥不安的",
"n.细读",
"v.仔细阅读，审查",
"n.悲观(主义)",
"adj.悲观的",
"n.害虫",
"n.爱畜，宠儿",
"v.n.请愿(书)",
"n.石油，汽油",
"n.石油",
"adj.细小的，不重要的",
"n.阶段，时期，侧面",
"n.现象，非凡的人",
"n.哲学家",
"adj.哲学上的",
"n.哲学，基本原则",
"n.电话v.打电话",
"n.语音学",
"n.照片",
"n.照片v.拍照",
"n.摄影师",
"n.摄影术",
"adj.静电复印的",
"n.词组，短语",
"adj.身体的，物质的",
"adv.物质上，身体上",
"n.内科医生",
"n.物理学家",
"n.物理学",
"n.钢琴家",
"n.钢琴",
"v.拣，采n.精华，镐",
"n.腌渍品，泡菜",
"n.扒手，小偷",
"n.v.郊游，野餐",
"n.画报",
"n.图片，画，照片",
"adj.风景如画的",
"n.馅饼",
"n.件，片段，张",
"n.码头，栈桥",
"n.猪",
"n.鸽子",
"n.色料",
"n.堆v.堆积",
"v.偷窃",
"n.香客，朝圣者",
"n.朝圣",
"n.药片，药丸",
"n.柱子",
"n.枕头",
"n.飞行员，领航员",
"n.别针，发卡v.别住",
"v.捏，掐，挤痛",
"n.松树",
"n.菠萝",
"adj.n.桃色，粉红色",
"n.品脱(容量单位)",
"n.先驱者v.倡导",
"n.先驱的",
"adj.虔诚的",
"n.管子，烟斗",
"n.管道，管线",
"n.海盗adj.盗版的",
"n.手枪",
"n.活塞",
"n.坑，洼，煤矿，桃核",
"v.搭帐篷，投掷",
"n.水罐",
"n.怜悯，惋惜，憾事",
"n.地方，位置v.放置",
"n.瘟疫",
"adj.明白的，朴素的",
"n.计划平面图v.打算",
"n.水平，平面，飞机",
"n.行星",
"n.植物，工厂v.栽培",
"n.种植园",
"n.灰泥v.粘贴",
"n.塑料adj.可塑的",
"n.塑料(制品)",
"n.盘子，金属牌",
"n.高原，高地",
"n.讲台，站台，政纲",
"n.白金",
"v.玩，扮演，演奏",
"n.选手，演奏者",
"n.运动场，操场",
"n.游伴",
"n.剧作家",
"n.请求，恳求，辩解",
"v.恳求，辩解",
"adj.令人愉快的",
"v.使高兴，喜欢，请",
"adj.高兴的，乐意的",
"n.快乐，乐事，乐趣",
"n.暂约，抵押v.保证",
"adj.完全的",
"adj.大量的，丰富的",
"n.大量，丰富",
"n.保证，困境",
"n.阴谋，情节v.密谋",
"n.v.犁",
"v.拔，摘n.勇气",
"n.塞子，插头v.堵住",
"v.测锤，垂直",
"n.管子工",
"n.羽毛，羽饰",
"adj.丰满的",
"v.n.掠夺，抢劫",
"v.插进，跳入",
"adj.复数的",
"prep.加n.加号，正号",
"v.出力，努力从事",
"(缩)下午",
"adj.气体的，空气的",
"n.风湿病",
"n.衣袋adj.袖珍的",
"n.诗歌",
"n.诗人",
"n.诗，诗意，诗艺",
"n.尖，点，分v.指",
"adj.尖的",
"n.毒，毒药v.放毒",
"adj.有毒的",
"v.戳，刺",
"n.扑克",
"adj.极的",
"n.极性，极端",
"n.柱，杆，极",
"n.警察(局)",
"n.警察",
"n.政策，方针，保险单",
"v.擦亮，磨光，润色",
"adj.有礼貌的，客气的",
"n.礼貌，客气",
"adj.政治的",
"n.政治家，政客",
"n.政治学，政治活动",
"n.选举投票，民意测验",
"v.污染，弄脏",
"n.污染",
"n.聚合物",
"n.池塘",
"v.考虑，沉思",
"n.小马",
"n.水塘，游泳池",
"adj.穷的，差的",
"v.n.砰的一声，爆裂",
"n.爆米花",
"n.教皇",
"adj.受欢迎的",
"n.名望，知名",
"v.普及，宣传",
"n.人口",
"n.瓷，瓷器",
"n.门廊",
"n.毛孔",
"n.猪肉",
"n.粥，麦片粥",
"n.港口，港",
"adj.手提的，经便的",
"n.搬运工",
"n.一份，部分",
"n.肖像，画像，描写",
"v.描写，给...画像",
"n.葡萄牙",
"n.adj.葡萄牙人(的)",
"v.作姿态，提供考虑",
"n.位置，地位，处境",
"adj.明确的，肯定的",
"adv.断言地，绝对地",
"v.占有，拥有，控制",
"n.所有，财产",
"adj.所有(格)的",
"n.可能性",
"adj.可能的",
"adv.可能，或许",
"n.柱，职位v.邮寄",
"n.邮资",
"adj.邮政的",
"n.明信片",
"n.子孙，后代",
"n.邮递员",
"n.邮局",
"v.推迟，延迟",
"n.推迟",
"v.假定，主张",
"n.罐，壶，锅",
"n.马铃薯，土豆",
"adj.有效的",
"adj.潜在的n.潜力",
"n.潜在性",
"n.家禽",
"n.英镑，磅v.重击",
"v.注，灌，倒，涌出",
"n.贫穷，缺乏",
"n.粉末",
"n.力，动力，权力",
"adj.有力的，强的",
"adj.可行的",
"adj.实用的，可行的",
"adj.实际地，几乎",
"n.练习，习惯，实施",
"v.练习，习惯于做",
"n.大草原",
"v.n.赞美，称颂",
"v.祈祷",
"v.祷告，祷文",
"v.说教，鼓吹，布道",
"n.鼓吹者，宣教士",
"n.预防，防备",
"v.在前，高于",
"n.领先，优先权",
"n.先例，惯例",
"adj.前面的，上述的",
"adj.宝贵的，珍爱的",
"adj.精确的，严格的",
"adv.精确地",
"n.精确，精度",
"n.前任，原有物",
"v.预言",
"n.预言，预报",
"n.优越，杰出",
"adj.主要的，有势力的",
"n.序言，开场白",
"v.较喜欢，宁愿",
"adj.更喜爱的",
"adv.更好地",
"n.偏爱(之物)",
"adj.优惠的",
"n.前缀",
"n.怀孕",
"adj.怀孕的",
"n.偏见，成见",
"adj.初步的，预备的",
"n.序言，前兆，序曲",
"adj.早熟的",
"n.首相，总理",
"n.建筑物",
"n.津贴",
"v.使迷住，专心于",
"n.准备，预备",
"v.准备，配制",
"adj.准备好的，预制的",
"n.介词",
"v.命令，规定，开处方",
"adj.规定的",
"n.药方",
"n.出席，在场",
"adj.在场的n.现在",
"n.提出，演出",
"adv.不久，目前",
"n.保藏，保存",
"v.保护，保藏，保持",
"v.预先安排",
"v.主持",
"n.总统，总经理，校长",
"adj.总统的",
"v.压，榨，按n.印刷",
"adj.急迫的",
"n.压力，繁忙，紧迫",
"n.威望，声望",
"adv.也许，大概",
"v.假定，推测",
"v.假装，佯称",
"n.借口",
"adj.自负的，虚伪的",
"adj.精致的，漂亮的",
"v.获胜，流行",
"adj.占上风的",
"n.流行",
"adj.流行的，普遍的",
"v.防止，阻碍",
"n.防止，预防",
"adj.早先的，先前的",
"adv.预先，先前",
"n.猎物，牺牲品",
"n.价格，代价v.定价",
"n.价格表",
"n.定价",
"v.刺穿n.刺痛",
"n.骄傲，自豪，自负",
"n.教士，神父",
"adv.首要地，主要地",
"adj.首要的，初级的",
"adj.首要的，第一的",
"adj.原始的，简朴的",
"n.王子，诸侯",
"n.公主，王妃",
"adj.重要的，主要的",
"adv.主要地",
"n.原则，原理，主义",
"v.印刷，出版n.字体",
"n.印刷者",
"adj.较早的，在前的",
"n.优先，居先",
"n.棱镜",
"n.监狱，牢房",
"n.囚犯",
"n.私事，隐私",
"adj.私人的，秘密的",
"n.特权v.给特权",
"adj.有特权的",
"n.奖品，奖赏",
"n.可能性，概率",
"adj.很可能的",
"adv.或许，大概",
"v.细察，查究",
"n.课题，难题，问题",
"adj.有问题的",
"n.手续，程序",
"v.前进，继续向前",
"n.进行，诉讼",
"n.收益",
"n.程序，过程v.处理",
"n.adj.加工(的)",
"n.行列，仪仗",
"v.宣布，公布",
"v.采购",
"n.采购",
"v.生产，制造，创作",
"n.生产者",
"n.产品，作品",
"n.生产，制造",
"adj.能生产的，多产的",
"n.生产力，生产率",
"v.表白",
"n.职业，专业，表白",
"adj.职业的n.专业人员",
"n.教授",
"n.熟练，精通",
"adj.熟练的，精通的",
"n.侧面，轮廓",
"n.利润v.获益",
"adj.有利可图的",
"adj.形式的",
"adj.深奥的，深深的",
"n.节目，规划，项目",
"n.项目，程序制定者",
"n.程序编排",
"n.v.进步，进展",
"adj.前进的，进步的",
"v.禁止，阻止",
"n.禁止，禁令",
"adj.禁止的",
"n.计划v.设计，射出",
"n.射出，投射",
"n.电影放映机",
"adj.n.无产阶级",
"v.延长",
"n.显著，突出",
"adj.著名的，显著的",
"v.允诺，预示n.诺言",
"adj.有希望的",
"adj.约定的",
"v.提升，促进，宣传",
"n.晋级，提高，促销",
"adj.及时的，迅速的",
"adv.及时地，敏捷地",
"adj.俯伏的",
"n.代词",
"v.发音，宣布",
"n.发音",
"n.证明，证据，实验",
"n.宣传",
"v.繁殖，传播，宣传",
"n.繁殖，传播",
"v.推进，推动",
"adj.推进的",
"n.推进器，螺旋桨",
"adj.合适的，本来的",
"adv.合适地",
"n.财产，地产，特性",
"n.预言",
"n.预言家",
"n.比例，部分",
"adj.成比例的",
"n.建议，计划",
"v.建议，打算，求婚",
"n.建议，提议",
"n.所有者，业主",
"n.业主资格",
"n.散文",
"v.迫害",
"n.迫害",
"n.检查官",
"n.前景v.勘探",
"n.繁荣，兴旺",
"adj.繁荣的，兴旺的",
"v.保护，警戒",
"n.保护，警戒",
"n.贸易保护主义",
"adj.保护的",
"n.蛋白质",
"v.n.抗议，反对",
"n.清教徒，新教徒",
"n.协议，议定书",
"n.原型",
"adj.延长了的",
"adj.骄傲的，得意的",
"v.证明，表明是",
"n.谚语，格言",
"v.供给，提供，准备",
"conj.只要",
"n.省份，领域",
"adj.省级的，省的",
"n.准备，条款，辎重",
"adj.临时的",
"n.刺激，煸动",
"v.激怒，引起",
"adj.下月的",
"n.谨慎",
"adj.谨慎的",
"adj.心理(上)的",
"n.心理学家",
"n.心理学，心理状态",
"adj.公众的，公共的",
"n.出版物，发表",
"n.公开",
"adv.公开地",
"v.出版，发表，公布",
"n.出版商",
"n.布丁",
"n.一阵v.喘气",
"v.拖，拔，扯n.牵引",
"n.滑轮",
"n.脉搏v.跳动",
"n.泵v.抽水，打气",
"n.南瓜",
"n.v.用拳击，冲孔",
"adj.准时的，守时的",
"n.准时",
"n.准时",
"v.处罚，惩罚",
"n.处罚，刑罚",
"n.小学生，瞳孔",
"n.木偶，傀儡",
"n.小狗",
"v.n.购买",
"n.买主",
"adj.纯洁的，纯净的",
"adv.全然，纯然",
"v.净化",
"n.纯粹，纯净",
"n.紫色adj.紫色的",
"n.目的，用途，意图",
"n.钱包",
"n.追求，实行",
"n.追逐者",
"v.追逐，从事，追求",
"n.追逐，追求，职业",
"v.推，推动n.推力",
"v.放置，估价，表达",
"v.使困惑n.难题谜语",
"n.睡衣",
"n.金字塔",
"n.资格，条件",
"adj.有资格的",
"v.使合格，使胜任",
"adj.质量的，定性的",
"n.特性，属性，质量",
"adj.数量的，定量的",
"n.量，大量",
"v.n.争吵",
"n.夸脱(容量单位)",
"n.四分之一，一刻钟",
"adj.季度的n.季刊",
"n.石英",
"n.码头",
"n.王后，女王",
"adj.奇妙的，古怪的",
"v.抑制，熄灭，淬火",
"v.n.询问",
"n.寻找，搜索",
"n.问题，疑问v.询问",
"n.调查表",
"n.辫子，队v.排队",
"adj.快的，灵敏的",
"v.加快，加速，刺激",
"adv.快，迅速地",
"adj.安静的，轻声的",
"adv.安静地，静静地",
"n.平静，安定，安静",
"n.被子",
"v.停止，放弃，退出",
"adv.完全，十分，相当",
"v.颤抖",
"n.测验，问答比赛",
"n.定额，配额",
"n.引语，语录，报价单",
"v.引用，引证，报价",
"n.兔子",
"n.种族，竞赛v.赛跑",
"adj.种族的，人种的",
"n.搁班，行李架",
"n.喧闹，球拍",
"n.雷达",
"adj.放射的，辐射的",
"adj.发光的",
"v.辐射，放射，发光",
"n.辐射，发射",
"adj.基本的，激进的",
"n.无线电，收音机",
"adj.放射性的",
"n.放射性",
"n.萝卜",
"n.镭",
"n.半径，活动范围",
"n.抹布，破衣服",
"n.盛怒，流行v.大怒",
"v.袭击，搜查",
"n.栏杆，钢轨",
"n.铁路",
"n.铁路，铁路公司",
"n.雨v.下雨",
"n.虹",
"n.雨衣",
"n.下雨，降雨量",
"adj.有雨的",
"v.举起，提高，唤起",
"n.v.耙",
"n.v.集会",
"n.漫步",
"n.牧场",
"adj.胡乱的，随便的",
"n.射程，范围，一系列",
"n.军衔，等级v.排列",
"adj.快的，急速的",
"adv.迅速地，急速地",
"n.狂喜",
"adj.稀有的，罕见的",
"adv.难得，少有",
"n.无赖，恶棍",
"adj.轻率的，鲁莽的",
"n.老鼠，耗子",
"n.比率，速度，费率",
"adv.相当，颇，宁愿",
"n.批准，认可",
"v.批准，认可，追认",
"n.比，比率",
"n.理性",
"adj.合理的，有理性的",
"v.n.嘎吱响",
"n.破坏，暴力",
"adj.生的，未加工的",
"n.光线，射线，辐射",
"n.剃须刀",
"prep.关于",
"v.到达，伸手，够到",
"v.反应，起反应，反抗",
"n.反应，反动",
"adj.反动的",
"n.反应堆",
"v.读，阅读，朗诵",
"n.读者，读本",
"adv.容易地，乐意地",
"n.读书，读数，读本",
"adj.准备好的，乐意的",
"adj.真的，纯粹的",
"n.现实主义，写实主义",
"n.adj.现实主义者(的)",
"adj.现实的，实在的",
"n.现实，真实性",
"n.实现",
"v.认识到，实现，执行",
"adv.真正地，果然",
"n.王国，领域",
"v.收割，收获",
"n.后部adj.后面的",
"n.原因，理由v.推论",
"adj.有理的，讲理的",
"adv.合理地，适当地",
"v.使...放心",
"n.回扣，折扣",
"v.起义，反叛",
"n.叛乱，起义",
"v.斥责",
"v.想到，召回，取消",
"v.归还，撤回",
"n.收到，收据",
"v.收到，接待，接见",
"n.受领人，听筒",
"adj.近来的，新近的",
"adv.近来，最近",
"n.招待会，欢迎会",
"n.接待员",
"n.衰退",
"n.菜谱，配方",
"n.接受者",
"adj.相互的，互易的",
"n.朗诵",
"v.背诵，朗诵，讲述",
"adj.鲁莽的",
"v.数，计算，认为",
"v.收回，开垦",
"n.认出，承认",
"v.认出，识别，承认",
"v.回忆，追想",
"n.回忆",
"v.推荐，介绍，劝告",
"n.推荐(书)",
"v.n.回报，赔偿",
"v.使和好，调停",
"n.探索，勘查",
"v.记录，录音n.记录",
"n.记录员，录音机",
"n.求助",
"v.寻回，恢复，复原",
"n.寻回，恢复",
"n.消遣，文娱活动",
"v.招募，征兵",
"n.招募",
"n.长方形，矩形",
"n.纠正",
"v.纠正，订正",
"v.再发生，复发",
"n.再发生",
"adj.红的n.红色",
"v.买回，赎回",
"v.增加，促进",
"v.减少，贬为",
"n.减少，缩减",
"n.芦苇，芦笛",
"n.礁石",
"n.卷，线轴v.卷绕",
"v.再出口",
"v.查阅，提及",
"n.裁判员",
"n.参考(书)，推荐书",
"n.被谈到的事",
"v.精炼，精制",
"adj.精炼的，精的",
"n.精炼",
"n.精炼厂",
"v.反射，反映，反省",
"n.反射，映象，反思",
"v.n.改革，改造",
"v.抑制",
"v.使清醒，使振作",
"n.茶点，饮料",
"n.冰箱",
"n.藏身处，避难所",
"n.难民",
"v.再投资归还n.退款",
"n.拒绝，谢绝",
"v.拒绝n.渣，废物",
"v.驳斥，反驳",
"v.认为，尊重，关于",
"prep.关于",
"adj.adv.不顾的(地)",
"n.政体，制度",
"n.团，大量",
"n.地区，地域，地带",
"adj.地区的，区域的",
"n.区域化",
"v.使区域化",
"v.登记，注册，挂号",
"adj.登记的，注册的",
"n.登记",
"v.懊悔n.遗憾",
"adj.遗憾的",
"adv.遗憾地",
"adj.可遗憾的",
"adj.正常的，有规律的",
"n.整齐，规律",
"adv.整齐地，有规律地",
"v.管理，调整",
"n.管理，规则，法令",
"n.排练，彩排",
"v.排练",
"n.统治v.统治，盛行",
"v.偿还",
"n.偿还，还款",
"n.缰绳v.驾驭，约束",
"v.增援，加强",
"n.加强，援兵",
"v.重申",
"v.拒绝",
"n.拒绝",
"v.欢欣，使喜悦",
"v.叙述，关联，涉及",
"adj.与...有关的",
"n.关系，得害关系",
"n.关系，联系",
"n.亲戚adj.有关系的",
"adv.比较地，相对地",
"n.相关性，相对论",
"v.松弛，舒张，休息",
"n.放松，松弛",
"v.转播，中继",
"v.释放，透露，发行",
"adj.相关的",
"n.可靠性",
"adj.可靠的，可依赖的",
"n.依靠，信赖",
"n.解除，减轻，安慰",
"v.解除，减轻，换班",
"n.宗教(信仰)",
"adj.宗教的，信教的",
"v.放弃",
"n.味道，风味",
"n.不愿，勉强",
"adj.不愿的，勉强的",
"v.依靠，依赖",
"n.依旧的，剩余，逗留",
"n.剩余部分",
"n.剩余，遗迹，遗体",
"v.说起，留意，评论",
"adj.显著的，异常的",
"n.药品，治疗(方法)",
"v.记得，想起，记住",
"n.记得，记忆",
"v.提醒，使想起",
"n.回想，回忆，怀念",
"adj.使想起...的",
"v.汇款，汇出",
"n.汇款",
"n.残余，残迹",
"adj.遥远的，疏远的",
"n.遥远，疏远",
"n.移开，除去，移居",
"v.移开，除去，罢免",
"n.列举",
"n.(文艺)复兴",
"v.使得，给予，翻译",
"v.更新，续期",
"adj.可续期的",
"n.更新，续订",
"n.租金v.租",
"adj.租借的，租金的",
"v.修理，纠正",
"n.修理，修补，纠正",
"v.偿付，报答",
"v.n.撤消，废除",
"v.重复，背诵",
"adj.重复地，一再地",
"v.驱逐，推开",
"v.后悔，悔悟",
"n.重复，反复，复制",
"adj.重复的，反复的",
"v.归还原处，代替",
"n.归回，代替(物)",
"v.补充",
"n.补充(货物)",
"v.n.回答，答复",
"v.报告，报导，报道",
"n.报告文学",
"n.报告人，记者",
"v.表示，表现，代表",
"n.表示，代表",
"adj.代表",
"v.n.责备，指责",
"v.复制，再造，繁殖",
"n.复制(器)",
"n.爬行动物",
"n.共和国",
"n.adj.共和(派)的",
"n.拒绝接收，拒付",
"adj.声誉好的",
"n.名声，声誉",
"n.声誉v.看作，评价",
"n.请求",
"v.需要，请求",
"n.要求，需要",
"adj.必要的，需要的",
"adj.退还，取消",
"v.n.救援，救出",
"v.n.调查，研究",
"n.调查者，研究人员",
"n.相仿，类似",
"v.象，类似",
"v.不满于，愤恨",
"adj.不满的，怨恨的",
"n.不满，愤恨",
"n.贮存物，预定",
"v.贮备，保存，预定",
"n.水库",
"v.居住，存在",
"n.住宅，住处",
"n.居民",
"adj.剩余的",
"v.辞职",
"n.辞职",
"v.抵抗，忍住",
"n.抵抗，阻力，反感",
"n.抵抗的，反对的",
"adj.坚决的，果断的",
"n.决议，决定，决心",
"adj.坚决地，果断地",
"v.决定，解决，分解",
"v.诉诸，求助n.胜地",
"n.资源，机智，策略",
"v.尊重，重视，尊敬",
"adj.可敬的",
"adj.恭敬的，尊重的",
"adv.恭敬地",
"adj.各自的，各个的",
"adv.各自，分别地",
"v.答复，反应，响应",
"v.答复，反应，响应",
"n.责任，职责",
"adj.负责的，尽责的",
"v.休息n.休息，休止",
"n.饭馆，餐厅",
"adj.没休息的，不安的",
"v.重新进货",
"v.恢复，复原，归还",
"v.抑制，制止",
"n.抑制，自制",
"v.限制，约束",
"n.限制，约束",
"n.限制的",
"n.结果，效果，后果",
"adj.结果的，合成的",
"v.继续，再度",
"n.个人简历，摘要",
"v.n.零售",
"n.零售商",
"v.保留，记忆，雇",
"v.复述",
"v.退休，退隐，就寝",
"n.退休，隐居",
"v.反驳，回嘴",
"v.n.退却，撤退",
"adj.可追溯的",
"v.回归，归还n.归来",
"v.揭露，透露，显示",
"n.v.报仇，报复",
"n.岁入，收入",
"n.尊敬，崇敬",
"adj.颠倒的，相反的",
"v.回复到，重议",
"v.n.检查，复习",
"v.修改，校订，复习",
"n.修改，修订",
"n.复苏，再生",
"v.苏醒，复苏",
"v.废除，取消，撤回",
"n.v.起义，反抗",
"n.革命，变革",
"adj.革命的",
"v.旋转，绕行",
"n.报酬，酬金，报答",
"adj.有收获的",
"n.风湿病",
"n.韵，脚韵",
"n.韵律，节奏",
"n.肋，肋骨",
"n.带子，缎带",
"n.稻子，大米，米饭",
"adj.富的，富饶的",
"n.富饶，富有",
"v.使摆脱，使除去",
"n.谜语，谜",
"v.乘坐，骑n.乘车",
"n.山脉，岭，屋脊",
"n.v.嘲笑，挖苦",
"adj.可笑的，荒谬的",
"n.步枪，来福枪",
"adj.正确的，右的",
"adj.正直的，公正的",
"adj.僵硬的，严厉的",
"adj.僵硬，严厉，死板",
"n.严格，严肃",
"adj.严厉的，酷热的",
"n.边缘，眼镜架",
"v.鸣，打铃，打电话",
"v.漂洗，润丝",
"n.v.骚乱，闹事",
"adj.骚乱的，喧扰的",
"v.撕破，扯碎",
"adj.熟的，成熟的",
"v.成熟，变热",
"n.波纹，涟漪",
"v.起立，晋级，增长",
"n.v.冒险，风险",
"adj.有风险的，冒险的",
"n.对手adj.竞争的",
"n.竞争，对抗",
"n.河，江",
"n.道路，路",
"v.漫步，漫游",
"v.n.吼，怒号，轰鸣",
"v.烤，炙adj.烘烤的",
"v.抢劫，偷",
"n.强盗",
"n.抢劫(案)",
"n.长袍",
"n.机器人",
"adj.强壮的，粗壮的",
"n.岩石v.摇摆，摇晃",
"n.adj.(价格)最低(的)",
"n.火箭",
"n.小棒，竿",
"n.角色，作用",
"v.滚，卷，转动，压平",
"n.滚筒，压路机",
"adj.古罗马的n.罗马人",
"n.浪漫文学，浪漫故事",
"adj.浪漫的，好幻想的",
"n.浪漫主义",
"n.罗马",
"n.屋顶",
"n.房间，室，空间",
"n.公鸡",
"n.根，根源",
"n.绳，索",
"n.玫瑰，蔷薇",
"adj.玫瑰红的，幻想的",
"v.腐烂，枯朽",
"adj.旋转的",
"v.旋转，循环，转流",
"n.旋转，更替",
"adj.腐烂的，发臭的",
"adj.粗糙的，粗野的",
"adv.大约地，粗略地",
"adj.圆形的adv.在周围",
"adj.迂回的，转弯抹角",
"v.唤醒，惊起",
"n.路线，航线",
"n.日常事务",
"v.划船n.排，列",
"adj.王室的，皇家的",
"n.皇家，皇族",
"v.擦，摩擦，涂抹",
"n.橡胶，橡皮",
"n.垃圾，废物，废话",
"adj.粗鲁的，下流的",
"n.小块地毯",
"n.废墟v.毁坏，破坏",
"adj.毁灭性的",
"n.法规，常规，统治",
"n.统治者，直尺",
"adj.统治的",
"n.v.传闻，谣言",
"v.跑，竞选，行驶",
"n.奔跑者，赛跑运动员",
"adj.连续的n.经营",
"adj.农村的",
"v.n.冲，冲进",
"n.俄罗斯，俄语",
"n.adj.俄国(人)的",
"n.锈v.生锈，衰退",
"adj.生锈的",
"adj.无情的，冷酷的",
"n.麻袋v.解雇",
"adj.神圣的",
"n.v.牺牲(品)",
"adj.悲哀的，可悲的",
"n.马鞍",
"adv.悲哀地，可惜",
"n.悲哀",
"adj.安全的，无风险的",
"adv.安全地，平安地",
"n.安全adj.保险的",
"v.下跌",
"adj.上述的，该",
"n.帆v.行驶，开航",
"adj.启航的n.航行",
"n.水手，海员",
"n.圣人，圣徒",
"n.缘故，利益",
"n.色拉，拌凉菜",
"n.适销性",
"adj.有销路的，适销的",
"n.工资，薪水",
"n.出售，贱卖",
"n.销售adj.出售的",
"n.售货员，推销员",
"n.鲑，大马哈鱼",
"n.盐",
"adj.咸的",
"v.行礼，致敬",
"n.致敬",
"adj.同样的",
"n.样品v.抽样",
"n.抽样",
"n.沙子",
"n.三明治v.夹入",
"adj.沙的，沙色的",
"n.疗养院",
"Clausn.圣诞老人",
"n.讽刺，挖苦",
"adj.讽刺的",
"n.沙丁鱼",
"n.卫星",
"n.讽刺作品",
"n.满足，满意",
"adv.圆满地",
"adj.令人满意的",
"v.满足，使满意，偿还",
"n.浸透，饱和",
"n.星期六",
"n.土星",
"n.调味汁，酱油",
"n.茶碟",
"n.香肠，腊肠",
"adj.野蛮的，残暴的",
"v.救，拯救，储蓄",
"n.存款，储蓄额",
"v.n.锯",
"v.说n.发言(权)",
"n.刻度，等级，秤",
"adj.鱼鳞状的",
"v.浏览，细察，扫描",
"n.丑闻",
"n.疤，疤痕",
"adj.缺乏的，罕见的",
"adv.几乎没有，将近",
"n.缺乏，不足",
"v.惊吓n.惊恐",
"n.围巾，头巾",
"adj.n.猩红的，鲜红的",
"v.散布，撒播",
"n.现场，情景，一场戏",
"n.风景，布景",
"adj.风景如画的",
"n.气味，香味",
"n.时间表v.排定",
"n.计划，方案，图谋",
"n.学者",
"n.奖学金，学问",
"n.学校，上学，学系",
"n.学校教育",
"n.科学，学科",
"adj.科学的",
"n.科学家",
"n.剪刀",
"v.嘲笑，嘲弄",
"v.n.训斥，责骂",
"n.范围",
"v.烧焦",
"adj.灼热的",
"n.得分，成绩，二十",
"n.v.蔑视，不屑",
"adj.蔑视的，轻视的",
"n.苏格兰",
"n.苏格兰人",
"adj.苏格兰的",
"n.苏格兰",
"n.侦察员，童子军",
"v.爬，攀，争夺",
"n.碎片，废品，屑",
"v.擦，刮，凑集",
"v.抓破，挠n.抓痕",
"v.n.尖叫声",
"v.n.尖叫(声)",
"n.屏，帘v.甄别",
"v.拧n.螺钉",
"n.螺丝刀，改锥",
"n.临时单据",
"v.擦洗，刷",
"n.细看，复查",
"n.雕塑家",
"n.雕塑，雕刻",
"n.海，海洋",
"v.封n.图章，封条",
"n.接缝",
"n.海员，水手",
"n.海港，港口",
"v.n.搜查，寻找",
"n.海滨",
"n.海边",
"n.季节v.调味",
"adj.季节性的",
"n.座位，席位v.就座",
"num.第二n.第二，秒",
"adj.第二的，次要的",
"adj.二手的，间接的",
"adv.第二，其次",
"n.秘密(状态)",
"adj.秘密的n.秘密",
"n.秘书处",
"n.秘书，部长，书记",
"n.部分，区域",
"n.部分，部门",
"adj.安全的，可靠的",
"n.安全，有价证券",
"v.看见，明白，查看",
"n.种子v.播种",
"v.寻觅，企图获得",
"v.好象，似乎",
"adv.表面上",
"n.部分，节，片",
"v.抓住，夺取，占领",
"n.强占，没收",
"adv.难得，不常",
"v.挑选adj.精选的",
"n.选择，选集",
"n.自己，自身，品质",
"adj.自私的，利己的",
"v.卖，出售",
"n.卖方",
"n.研讨会，学术讲座",
"n.半导体",
"n.参议院",
"n.参议员",
"v.派遣，送，寄出，请",
"n.寄信人",
"adj.年长的，老资格的",
"n.感觉，感动",
"adj.轰动的",
"n.感官，感觉，见识",
"adj.无意义的",
"adj.明智的，感知的",
"adj.敏感的",
"n.灵敏度",
"n.句子v.判决",
"n.感情，情绪",
"adj.多愁善感的",
"v.分离，分隔，分手",
"adv.分别地",
"n.分离，分开",
"n.九月",
"n.一连串，顺序",
"adj.清澈的，晴朗的",
"n.晴朗",
"n.系列，从书",
"adj.慎重的，严重的",
"adv.严肃地，严重地",
"n.布道，说教",
"n.大蛇",
"n.仆人",
"v.服务，任职，服役",
"n.服务，公共设施",
"adj.有用的，耐用的",
"n.会议，会期，市，盘",
"v.放，指定n.全套",
"n.安置，背景，环境",
"v.解决，安置，支付",
"n.解决，结算",
"num.七",
"num.十七",
"num.第七，七分之一",
"num.七十",
"adj.几个",
"adj.严厉的，苛刻的",
"adv.严厉地，苛刻地",
"v.缝纫",
"n.缝纫机",
"n.性，性别",
"adj.性的，性感的",
"n.性欲",
"adj.褴褛的，不体面的",
"n.阴影，遮光物，浓淡",
"n.影子，阴影",
"adj.有阴影的，模糊的",
"adj.遮阴的，背阴的",
"n.柄，竖井",
"v.摇动，发抖，握手",
"v.将",
"adj.浅的，浅薄的",
"n.赝品v.假冒",
"n.羞耻，耻辱",
"adj.可耻的，丢脸的",
"n.洗发香波",
"n.形状，轮廓v.形成",
"adj.不定形的",
"n.份，股份v.分配",
"n.鲨鱼",
"adj.锐利的，明显的",
"v.削尖，磨快",
"n.铅笔刀，磨石",
"adv.尖锐地，敏锐地",
"v.粉碎，毁坏",
"v.剃，修脸",
"pron.她",
"v.剪毛，切割",
"v.流下n.棚子",
"n.绵羊",
"adj.胆怯的",
"adj.全然的，极薄的",
"n.被单，张，大片",
"n.架子，搁板",
"n.壳，英，炮弹，外壳",
"n.躲避处，庇护",
"n.牧羊人",
"n.郡长，警官",
"n.盾牌v.防护",
"v.转变n.转移，轮班",
"n.先令",
"v.发光，照射，照耀",
"adj.耀眼的",
"n.船，舰v.船运",
"n.造船业",
"n.随船带交",
"n.船运，一船货",
"n.船主",
"n.船运，装运",
"n.(船只)失事",
"n.船坞",
"n.衬衣",
"v.发抖",
"n.震惊，电击v.震动",
"n.鞋",
"n.鞋匠",
"v.射击，发芽n.嫩芽",
"n.商店，车间",
"n.店主",
"n.购物",
"n.岸，滨",
"adj.短的，矮的",
"n.缺少，不足",
"n.短处，缺点",
"n.捷径",
"v.缩短",
"n.速记",
"adv.立刻，不久",
"n.短裤",
"n.短装，短重",
"n.射击，弹丸",
"v.应该，会",
"n.肩膀",
"v.n.叫喊",
"v.推，推开",
"n.铲子",
"v.显示，表明n.演出",
"n.阵雨，淋浴",
"n.展室，陈列室",
"adj.机敏的，精明的",
"v.n.尖叫(声)",
"v.刺耳的v.尖叫",
"n.神龛",
"n.虾",
"v.收缩，畏缩",
"n.遮蔽物",
"n.灌木",
"v.n.耸肩",
"v.拖脚走",
"v.躲避，躲开",
"v.关闭，合拢",
"n.百叶窗，快门",
"n.梭v.穿梭",
"adj.害羞的，腼腆的",
"adj.有病的，厌恶的",
"n.病",
"n.镰刀",
"n.边，面，侧面，一方",
"n.人行道",
"adv.侧面地",
"v.包围，围攻",
"n.筛子",
"v.筛，细查",
"v.n.叹息，叹气",
"n.视力，情景",
"n.观光，游览",
"n.告示，迹象，符号",
"n.信号v.做手势",
"n.签字",
"n.重要性，意义",
"adj.重要的，有意义的",
"v.表示，意味",
"n.路标，广告柱",
"n.寂静，沉默",
"adj.寂静的，沉默的",
"n.硅",
"n.丝，绸adj.丝的",
"adj.丝绸般的",
"adj.糊涂的，愚蠢的",
"n.银，银餐具",
"adj.类似的，相象的",
"n.类似，相似",
"adj.简单的，朴素的",
"n.简单，简朴，单纯",
"v.简单化",
"adv.简单地，仅",
"v.假装，佯伪",
"adj.同时(发生)的",
"adv.同时地",
"n.罪，罪恶",
"prep.自从conj.既然",
"adj.真诚的，诚挚的",
"adv.真诚地",
"n.真诚，诚挚",
"adj.有罪的，罪恶的",
"v.唱",
"n.歌手",
"adj.单个的，单身的",
"adj.非凡的，单数的",
"v.沉，下落n.水槽",
"n.先生",
"n.汽笛，报警器",
"n.姊，妹",
"v.坐，栖息",
"n.场所，场地",
"n.起居室",
"v.位于，坐落在",
"n.形势，局面",
"num.六",
"num.十六",
"num.第六，六分之一",
"num.六十",
"adj.相当大的",
"n.大小，规模，尺寸",
"n.冰鞋v.滑冰",
"n.滑冰，溜冰",
"n.骨架",
"n.素描，速写，草图",
"n.雪撬v.滑雪",
"n.滑雪",
"n.技能，技艺",
"adj.熟练的",
"v.撇去，掠过，略谈",
"n.皮，皮肤v.剥皮",
"v.跳过，遗漏",
"n.小冲突",
"n.裙子",
"n.颅骨",
"n.天，天空",
"v.猛涨",
"n.摩天大楼",
"adj.松驰的，不景气的",
"v.砰地关上",
"n.v.诽谤，污蔑",
"n.俚语",
"v.掌击，掴",
"v.n.屠宰，屠杀",
"n.奴隶v.做苦工",
"n.奴隶制，奴役",
"v.屠杀",
"v.n.睡眠",
"adj.欲睡的",
"n.雨加雪",
"n.袖子",
"adj.细长的，苗条的",
"n.薄片v.切成薄片",
"v.滑，溜",
"adj.轻微的，纤瘦的",
"adv.轻微地，稍稍",
"adj.苗条的",
"v.滑，滑行，溜走",
"n.便鞋，拖鞋",
"adj.滑的",
"v.割裂n.狭口，裂缝",
"n.标语，口号",
"v.倾斜n.坡，坡度",
"adj.慢的，迟钝的",
"n.放慢，迟缓",
"adj.慢慢地",
"n.贫民窟",
"n.睡眠，微睡",
"n.暴跌，不景气",
"adj.狡猾的",
"n.滋味v.劈啪地响",
"adj.小的，不重要的",
"adj.聪明的，漂亮的",
"v.打破，粉碎，猛撞",
"v.嗅发出气味n.气味",
"v.n.微笑",
"n.烟雾",
"v.冒烟，抽烟n.烟",
"n.抽烟者",
"n.抽烟",
"adj.平稳的，光滑的",
"adv.顺利地，安稳地",
"v.走私，夹带",
"n.走私者",
"n.走私",
"n.快餐，小吃",
"n.蜗牛",
"n.蛇",
"v.n.折断(声)",
"v.n.抢夺，攫取",
"v.偷偷地逃走、做",
"n.旅游鞋",
"v.n.嘲笑，讥笑",
"v.打喷嚏",
"v.嗅，闻",
"n.势利小人",
"n.势利",
"adj.势利的",
"v.打鼾",
"n.雪v.下雪",
"n.雪人",
"n.暴风雪",
"adj.有雪的，下雪的",
"adv.这样，也一样",
"v.浸，吸水，湿透",
"n.肥皂",
"v.急速上升，暴涨",
"v.n.呜咽，啜泣",
"adj.清醒的，冷静的",
"adj.所谓的",
"n.足球",
"adj.善交际的，社交的",
"adj.社会的，社会性的",
"n.社会主义",
"n.adj.社会主义者、的",
"n.社会，协会，社交界",
"n.社会学家",
"n.社会学",
"n.短袜",
"n.苏打，碱，苏打水",
"n.钠",
"n.沙发，软椅",
"adj.柔软的，温和的",
"v.使柔软，变软",
"adv.柔软地，温和地",
"n.柔软，温和",
"n.软件",
"n.土壤，国土，污秽",
"adj.太阳的",
"n.士兵，兵",
"adj.唯一的，单独的",
"adv.唯一地，只",
"adj.正式的，严肃的",
"n.律师",
"adj.固体的，牢固的",
"n.团结",
"adj.独自的，孤独的",
"n.寂寞，独居",
"n.独唱，独奏",
"n.解决，溶液",
"v.解答，溶解",
"n.偿付能力",
"adj.有偿付能力的",
"adj.若干，某一",
"pron.某人，重要人物",
"adv.以某种方式",
"pron.有人，某人",
"pron.某事，某物",
"adv.日后，曾经",
"adv.有时，不时",
"adv.稍微，有点",
"adv.某地，到某处",
"n.儿子",
"n.歌，歌词，鸟鸣",
"n.女婿",
"n.十四行诗",
"n.索尼愛立信通訊手機公司",
"adv.不久，很快，早",
"n.油烟，煤烟",
"v.安慰，使镇定",
"adj.复杂的，先进的",
"n.世故",
"adj.疼痛的，恼火的",
"n.伤心，悲哀，忧患",
"adj.悲哀的，忧愁的",
"adj.难过的，遗憾的",
"n.种类v.分类，拣",
"v.灵魂，心灵，人",
"n.声，声音v.听起来",
"n.汤",
"adj.酸的，不高兴的",
"n.来源，出处，源泉",
"n.南南方adj.南方的",
"n.东南(部)",
"adj.南的，南方的",
"adj.adv.向南",
"n.西南(部)",
"n.纪念品",
"n.君主adj.主权的",
"n.主权",
"v.播种，散布n.母猪",
"n.酱油",
"n.空间，太空，空地",
"n.宇宙飞船",
"n.太空船，宇宙飞船",
"n.航天飞机",
"adj.广阔的，宽敞的",
"n.铲子，铁锹，黑桃",
"n.西班牙",
"n.跨度；指距v.跨越",
"adj.n.西班牙人(的)",
"v.腾出时间adj.备用的",
"n.火花，火星",
"v.发火花，闪耀",
"n.麻雀",
"adj.空间的",
"v.说话，发言，讲",
"n.说话者，发言人",
"n.矛，枪",
"adj.特别的，专门的",
"n.专家",
"v.专攻，专门研究",
"adj.专业的，专门的",
"adv.特地，专门地",
"n.专业，专长",
"n.物种，种类",
"adj.特殊的，明确的",
"n.规格，明细表",
"v.详细说明，指定",
"n.标本，样本",
"n.眼镜，场面，壮观",
"adj.壮观的",
"n.观众，旁观者",
"n.光谱",
"v.推测，投机",
"n.推测，投机",
"n.投机商",
"n.演说，语言能力",
"n.速度v.飞驰",
"adj.快速的",
"v.拼写，咒语",
"n.拼音，拼写",
"v.花费，消耗",
"n.球体，范围，领域",
"n.香料，调味品",
"adj.辛辣的",
"n.蜘蛛",
"v.溢出，流出",
"v.自转，纺",
"adj.n.螺旋(的)",
"n.精神，心灵n.酒精",
"adj.精神上的，心灵的",
"v.吐，倾吐n.唾液",
"n.恶意，怨恨",
"v.溅，泼",
"adj.辉煌的，灿烂的",
"v.劈，分割",
"v.损坏，宠坏",
"n.发言人",
"n.海绵",
"n.发起人，主办者",
"n.发起，主办",
"adj.自发的",
"n.汤匙",
"adj.一匙的量",
"v.运动，嬉戏",
"n.运动员",
"n.体育精神",
"n.点，斑，污点，场所",
"v.n.扭伤",
"n.水雾v.喷射",
"v.伸开，散布，传播",
"v.跳跃，萌芽n.春季",
"v.洒，撒，不细雨",
"n.幼芽v.出芽",
"n.v.刺激，鼓舞",
"n.间谍",
"n.正方形，广场，平方",
"v.压碎n.果子汁",
"v.蹲",
"v.压，榨，挤",
"n.(缩)轮船",
"n.松鼠",
"v.n.刺，戳",
"n.稳定性",
"adj.稳固的，稳定的",
"n.v.推放，垛",
"n.露天运动场",
"n.工作人员，棒子",
"n.舞台，阶段v.上演",
"v.蹒跚",
"n.停滞",
"n.污点，瑕疵v.弄脏",
"adj.无瑕的，不锈的",
"n.楼梯",
"n.扶手楼梯",
"n.桩，赌注",
"adj.陈旧的",
"n.主茎，叶柄",
"n.厩，货摊",
"v.n.口吃，结巴",
"n.邮票，图章v.盖章",
"v.站立，坐落，忍受",
"n.标准adj.标准的",
"v.标准化",
"adj.常务的n.地位",
"n.立场，观点",
"n.停顿",
"n.钉书钉，主要产品",
"n.钉书机",
"n.星v.主演",
"n.v.凝视",
"v.开始，着手，发动",
"n.出发，开始",
"v.惊吓，使吃惊",
"n.饥饿",
"v.挨饿，渴求",
"n.状态，国家，州",
"n.声明，陈述",
"n.政治家，国务活动家",
"adj.静止的，静态的",
"n.站，台v.驻扎",
"adj.固定的，稳定的",
"n.文具",
"adj.统计的",
"n.统计(学)",
"n.雕像，铸像",
"n.形势，身分",
"n.法令，章程，条例",
"v.停留，暂住，保持",
"adv.稳固地，稳步地",
"adj.平稳的，稳健的",
"n.牛排，排骨",
"v.偷窃",
"n.汽，蒸汽v.蒸",
"n.汽船",
"n.钢",
"adj.陡峭的",
"v.驾驶，行驶",
"n.茎",
"n.复写纸，蜡纸",
"n.脚步，台阶，步骤",
"n.立体声",
"adj.英镑的",
"adj.严厉的，坚决的",
"n.码头工人",
"v.炖，煮n.炖菜",
"n.乘务员，男仆",
"n.女乘务员，空姐",
"n.枝，杆，手杖v.扎",
"adj.黏的",
"adj.僵硬的，生硬的",
"adj.静止的adv.仍旧",
"n.寂静，静止",
"v.刺激，使兴奋",
"n.刺激",
"n.刺痛v.刺，叮",
"adj.臭的",
"v.合同规定，约定",
"n.规定",
"v.搅拌，激起n.骚动",
"adj.动人的",
"n.一针v.缝合",
"n.存货，股份v.贮存",
"n.长袜",
"n.胃",
"n.石头，石料，宝石",
"adj.石头多的",
"n.凳子",
"v.弯腰，屈从n.俯身",
"v.停止，终止n.停止",
"n.贮藏，货栈",
"n.商店v.贮藏，储备",
"n.楼层",
"n.暴风雨，暴怒",
"adj.有暴风雨的",
"n.故事，小说，经历",
"adj.肥胖的，结实的",
"n.炉子，火炉",
"v.装载，理舱",
"n.装载",
"adj.直的adv.笔直地",
"adj.直爽的",
"v.弄直",
"v.拉紧，扭伤，使紧张",
"n.海峡",
"n.(绳)股，缕",
"adj.奇怪的，陌生的",
"n.新人，陌生人",
"n.带，皮带",
"adj.战略的",
"n.战略，策略，计谋",
"n.麦杆，稻草，吸管",
"n.草莓",
"v.迷路adj.走失的",
"n.纹理，条纹",
"n.小溪，流",
"n.流线型v.精简",
"n.大街",
"n.有轨电车",
"n.力气，力量，强度",
"v.加强，巩固",
"v.n.强调，压力",
"v.伸展，拉长n.伸展",
"adj.严格的，精确的",
"adv.严格地，绝对",
"adv.阔步走n.阔步",
"n.冲突，争斗",
"v.打，攻击，罢工",
"adj.引人注目的",
"n.细绳，弦，一串",
"v.剥n.窄条",
"n.条纹",
"v.努力，奋斗",
"n.敲，笔划v.抚摸",
"v.n.散步，闲逛",
"n.散步者",
"adj.强壮的，强烈的",
"adv.强烈地，强有力地",
"n.堡垒，要塞",
"adj.结构的，组织上的",
"n.结构，构造，组织",
"v.n.斗争，奋斗",
"adj.顽固的，倔强的",
"n.学生，研究人员",
"n.画室，工作间",
"v.n.学习，研究",
"n.材料，东西v.塞满",
"adj.闷热的，不透气的",
"v.绊跌",
"n.树桩，残茬",
"adj.愚蠢的，迟钝的",
"n.愚蠢",
"adj.健壮的",
"n.风格，时尚，作风",
"n.时装设计师",
"v.细分，再分",
"v.战胜，征服",
"n.题目，学科，主语",
"adj.主观的",
"adj.虚拟的",
"adj.海底的n.潜水艇",
"v.浸没，淹没",
"v.服从，呈交",
"adj.下级的，辅助的",
"n.服从",
"v.订购，订阅",
"n.预订，订购",
"n.后果",
"adj.以后的，后起的",
"adv.后来，其后",
"adj.辅助的，次要的",
"n.物质，实质",
"adj.可观的，实质的",
"v.证实",
"n.v.代替，代用品",
"n.代替",
"adj.敏锐的，微妙的",
"v.减去",
"n.减法，减去",
"n.郊区，郊外",
"adj.郊区的",
"n.地铁",
"v.成功，后继",
"n.成功",
"adj.成功的",
"adv.成功地",
"n.接连，继任",
"adj.接连的，连续的",
"n.继承人，继任者",
"adj.这样的，如此的",
"v.吮，咂",
"adj.突然的，意外的",
"adv.突然，忽然",
"v.遭受，受苦，忍受",
"n.苦难",
"v.足够，满足需要",
"adj.充足的，充分的",
"adv.充分地，足够地",
"n.后缀",
"n.糖",
"v.建议，暗示",
"n.建议，示意",
"n.自杀",
"n.一身西服，起诉",
"adj.合适的，适宜的",
"n.手提箱",
"n.随员，一套(房间)",
"adj.板着脸的",
"adj.闷热的",
"n.总数，会计v.总结",
"v.概括，总结",
"n.概要adj.概括的",
"n.夏季",
"n.顶峰，最高点",
"v.n.召唤，召集",
"n.太阳，阳光",
"v.晒黑",
"n.星期日",
"n.葵花",
"n.阳光",
"adj.向阳的，晴朗的",
"n.日出",
"n.日落",
"n.日照，日光",
"adj.特级的，超级的",
"adj.华丽的，超等的",
"adj.表面的，肤浅的",
"n.管理人，负责人",
"adj.优良的，上级的",
"n.优越(性)",
"n.超级市场",
"v.代替",
"adj.超音速的",
"n.迷信",
"adj.迷信的",
"v.管理，监督，监考",
"n.监督",
"n.监考人，监查",
"n.晚餐",
"n.v.增补，补充",
"adj.补充的",
"n.供应商",
"v.供应，供给",
"v.支持，资助，支援",
"n.支持者",
"v.猜想，假设",
"conj.假使",
"v.镇压，压制，遏止",
"n.镇压，压制",
"adj.最高的",
"n.附加费，超载",
"adj.有把握的，一定的",
"adv.一定，肯定，谅必",
"n.表面adj.表面的",
"n.v.汹涌，波动",
"n.外科医生",
"n.外科(学)",
"v.n.猜想，推测",
"n.姓",
"v.超过，胜过",
"n.过剩adj.剩余的",
"v.使惊诧n.惊奇",
"adj.惊人的",
"v.放弃，交出，投降",
"v.包围",
"n.环境，周围事物",
"v.视察，测量n.调查",
"n.调查人，检验人",
"n.幸存，遗风",
"v.幸免于，幸存",
"n.幸存者",
"v.怀疑n.嫌疑犯",
"v.吊，悬，暂停，停学",
"n.暂停，中止",
"n.怀疑，嫌疑",
"adj.可疑的，猜疑的",
"v.支撑，遭受",
"n.燕子v.吞咽",
"n.沼泽",
"n.天鹅",
"n.群v.云集",
"v.摇晃，影响",
"v.宣誓，诅咒",
"v.出汗n.汗水",
"n.运动衫，毛衣",
"n.瑞典人",
"n.瑞典",
"adj.n.瑞典人(的)",
"v.扫除，席卷",
"adj.甜的，甜蜜的",
"v.变甜，加糖",
"n.心肝，宝贝",
"n.甜味",
"v.膨胀，肿",
"adj.快的，迅速的",
"v.游泳，游",
"v.摇摆n.秋千",
"n.瑞士人",
"v.转换n.开关",
"n.瑞士",
"n.剑",
"n.音节",
"n.象征，符号",
"v.象征",
"adj.对称的，匀称的",
"n.对称",
"adj.同情的，有共鸣的",
"v.同情",
"n.同情，同感，共鸣",
"n.交响乐",
"n.座谈会，学术讨论会",
"n.症状，征兆",
"n.同义词",
"n.综合，合成",
"adj.合成的，人造的",
"n.系统，体制，制度",
"adj.系统的，有组织的",
"adv.有系统地",
"n.桌子，表格",
"n.药片",
"v.制表，将...列表",
"n.图钉",
"n.用具，辘轳v.抓住",
"n.机敏，圆滑",
"adj.机智的，老练的",
"n.战术，策略",
"n.标签，货签",
"n.尾巴，尾部",
"n.裁缝v.缝制",
"v.拿，带，吃，乘",
"n.起飞",
"n.故事",
"n.人才，天资",
"v.谈话n.讲话，会谈",
"adj.罗嗦的",
"adj.高的",
"v.吻合，符合",
"v.驯养，制报",
"n.黄褐色v.鞣草",
"v.缠绕，纠缠",
"n.油箱，水箱，坦克",
"n.油轮",
"v.叩击n.轻敲",
"n.条，带，磁带",
"n.录音机",
"n.录音",
"n.沥青，柏油",
"n.目标，对象，靶",
"n.皮重",
"n.关税",
"n.工作，任务",
"n.味道，趣味v.品尝",
"adj.有滋味的，好吃的",
"n.税v.征税",
"n.税(总称)，税务",
"n.出租汽车",
"n.茶，茶叶",
"v.教，教书，教导",
"n.教员，老师",
"n.教学，教导",
"n.茶杯",
"n.小队v.协同工作",
"n.茶壶",
"n.眼泪v.撕，拔",
"v.取笑，逗乐",
"adj.技术的，技能的",
"n.技术员，技师",
"n.技术，技巧",
"adj.技术的，工艺的",
"n.技术，工艺",
"adj.腻烦的，乏味的",
"n.(十几岁的)少年",
"n.十多岁",
"n.传真v.发传真",
"n.电报",
"n.电报",
"n.电话v.打电话",
"n.望远镜",
"n.电视，电视机",
"n.电传v.发电传",
"v.告诉，讲，说出",
"n.出纳",
"n.情绪，脾气",
"n.温度，体温",
"n.庙，寺院，太阳穴",
"adj.暂时的，临时的",
"v.引诱，诱惑",
"n.诱惑，引诱",
"num.十",
"n.房客，承租人",
"v.趋向，照料，投标",
"n.趋势，倾向",
"n.投标人adj.温柔的",
"n.网球",
"n.(支票)限期",
"adj.紧张的v.拉紧",
"n.紧张状态，张力",
"n.帐篷",
"adj.试探性的",
"num.第十，十分之一",
"n.期限，学期，术语",
"adj.可终止的",
"n.终点adj.末端的",
"v.终止，结束",
"n.终止，结束",
"n.术语(总称)",
"n.平台，台阶",
"adj.可怕的，极度的",
"adv.可怕地，极",
"adj.了不起的，极好的",
"v.惊吓，使恐怖",
"n.领土，领域，地区",
"n.恐怖，令人恐怖的事",
"n.恐怖主义",
"n.恐怖分子",
"v.n.测验，试验",
"v.证明，证实",
"n.证据",
"n.正文，课文，原文",
"n.课本，教科书",
"n.纺织品",
"adj.课文的，正文的",
"conj.比，除...外",
"v.谢谢，感谢",
"adj.感谢的，欣慰的",
"n.感谢int.谢谢",
"day]n.感恩节",
"adj.那那个adv.那么",
"(定冠词)那，这",
"n.剧场，戏剧，舞台",
"adj.戏剧的",
"n.偷盗",
"adj.他们的，它们的",
"pron.他(她)们，它们",
"n.主题，题目",
"pron.他们、它们自己",
"adv.当时，然后，那么",
"adj.理论的",
"n.理论，学说",
"adv.那里，到那里",
"adv.此后，其后",
"adv.因此，由此",
"adv.为此",
"adv.因而，所以",
"adv.由此",
"adv.在那里，其中",
"adv.及其，由此，它的",
"adv.关于那",
"adv.对此",
"n.温度计",
"pron.这些",
"n.论文",
"pron.他(她)们，它们",
"adj.厚的，浓的",
"v.加厚，变浓",
"n.厚，厚度，浓",
"n.窃贼，小偷",
"n.大腿",
"adj.薄的，瘦的",
"n.东西，事情",
"v.想，相信，认为",
"n.思想",
"n.思想家",
"num.第三，三分之一",
"n.渴，渴望",
"adj.渴的，渴望的",
"num.十三",
"num.三十",
"adj.pron.这，这个",
"n.刺，荆棘",
"adj.充分的，彻底的",
"adv.充分地，彻底地",
"pron.adj.那些",
"conj.虽然，可是",
"n.想法，思想，关怀",
"adj.深思的，体贴的",
"adj.轻率的，粗心的",
"num.千",
"v.抽打",
"n.线，思路",
"n.恐吓，威胁",
"v.恐吓，威胁",
"num.三",
"n.开端，门槛",
"n.节俭",
"adj.节俭的",
"v.发抖n.激动",
"n.惊险小说，电影",
"v.兴旺，繁荣",
"n.咽喉",
"n.王位",
"n.一群人v.挤满",
"prep.通过，借助",
"prep.贯穿adv.全部",
"v.n.投，扔，抛",
"v.强推，插入，刺",
"n.拇指",
"n.按钉，图钉",
"n.雷v.隆隆响",
"n.雷雨",
"]n.星期四",
"adv.如此，这样，因而",
"n.滴答声v.打勾号",
"n.票，标签，价目单",
"v.挠，搔，逗乐",
"n.潮汐，潮流v.度过",
"adj.整齐的，整洁的",
"v.捆，打结n.领带",
"n.(资金)占用，冻结",
"n.虎",
"adj.紧的，密封的",
"v.拉紧",
"adv.紧紧地，紧密地",
"n.母虎",
"n.瓦，瓷砖",
"prep.直到",
"v.n.倾斜",
"n.木材",
"n.时间，时候，次数",
"adj.及时的",
"n.时刻表，时间表",
"adj.胆怯的，害羞的",
"n.锡，锡器",
"adj.微小的",
"n.梢，尖，小费",
"v.用脚尖走",
"v.疲劳，厌倦",
"adj.疲劳的，厌倦的",
"adj.使人厌倦的",
"n.组织，卫生纸",
"n.标题，题目，称号",
"prep.向，到",
"n.蟾蜍，癞蛤蟆",
"n.烤面包，祝酒v.烘",
"n.烟草",
"adv.今天现在n.今日",
"n.脚趾，鞋头",
"adv.共同，一起，同时",
"v.苦干",
"n.卫生间，便桶",
"n.象征，纪念章",
"adj.可容忍的",
"n.宽容，容忍",
"adj.宽容的，宽大的",
"v.容忍，宽容",
"n.税",
"n.蕃茄，西红柿",
"n.坟",
"n.墓碑",
"n.明天adv.在明天",
"n.吨",
"n.语气，腔调，市况",
"n.舌，语言",
"n.今晚adv.在今晚",
"n.吨位，吨数",
"n.公吨",
"adv.也，非常",
"n.工具，手段",
"n.牙齿",
"n.牙疼",
"n.牙刷",
"n.牙膏",
"n.顶，盖子v.高于",
"n.课题，主题",
"n.火炬，手电筒",
"v.n.折磨，虐待",
"n.鱼雷",
"n.激流，山洪",
"n.龟",
"v.n.拷打，折磨",
"v.向上扔，颠簸，辗转",
"adj.总n.总和，合计",
"adv.统统，完全地",
"v.碰，接触，触动",
"adj.坚韧的，难嚼烂的",
"n.v.旅行，周游",
"n.旅游业",
"n.旅游者，游客",
"v.n.拖，牵引",
"prep.向，对于，将近",
"n.毛巾",
"n.塔v.高耸",
"n.市镇，城市，闹市",
"n.玩具",
"n.痕迹，微量v.追踪",
"n.径赛，轨道，路径",
"n.拖拉机",
"n.贸易，交换v.经商",
"n.商人",
"n.商标",
"n.商人",
"n.传统，惯例",
"adj.传统的",
"n.交通，交易，运输",
"n.悲剧，惨事，灾难",
"adj.悲剧的，悲惨的",
"v.拖曳，尾随n.踪迹",
"n.列车，一列v.训练",
"n.受训练者",
"n.教练",
"n.训练",
"n.叛徒",
"n.有轨电车",
"n.跋涉，流浪者",
"v.践踏，蹂躏",
"adj.平静的，安宁的",
"v.交易",
"n.交易",
"v.转移，转让",
"adj.可转让的",
"v.转变，转化",
"n.转化，转变",
"n.变压器",
"adj.短暂的，瞬时的",
"n.晶体管(收音机)",
"v.运输，转运",
"n.过渡，转变",
"v.翻译",
"n.翻译，译文",
"n.译音",
"n.传送，播送",
"v.传播，传导，发射",
"adj.透明的",
"v.移植",
"v.运送v.运输",
"n.运输，交通",
"v.转运，转船",
"n.转运",
"adj.横向的，横断的",
"n.陷井，圈套v.诱捕",
"n.v.横断，横过",
"v.旅行，传导",
"n.旅行者",
"n.托盘",
"v.踩，践踏",
"n.谋反，叛国",
"n.财宝，珍宝v.珍藏",
"n.司库",
"v.对待，医治，论述",
"n.待遇，疗法",
"n.条约",
"n.树",
"v.哆嗦，发抖",
"adj.巨大的，惊人的",
"n.沟，壕",
"n.走向，趋势",
"n.审讯，尝试，试验",
"n.三角(形)",
"adj.三角形的，三方的",
"n.部落",
"n.颂词，献礼",
"n.诡计，骗局，伎俩",
"v.滴下，流下",
"adj.巧妙的，狡猾的",
"n.小事，琐事",
"n.扳机v.触发",
"v.修剪，修整",
"n.旅行，远足",
"adj.三倍的，三重的",
"n.一式二份",
"n.胜利v.战胜",
"adj.得胜的，得意的",
"adj.琐碎的",
"n.手推车，电车",
"n.队，军队",
"n.回归线，热带",
"adj.热带的",
"v.n.小跑，快步走",
"n.v.麻烦",
"adj.讨厌的，麻烦的",
"n.裤子",
"n.卡车，载重汽车",
"adj.真实的，真正的",
"adv.真正地，确实",
"n.喇叭",
"n.树干，躯干，皮箱",
"n.v.委托，信任，信托",
"n.真相，真理",
"adj.诚实的，真正的",
"v.尝试，审讯n.尝试",
"n.浴缸，木盆",
"n.管子，试管",
"n.结核，肺结核",
"v.卷起，塞进",
"]n.星期二",
"v.n.用力拖，拖船",
"n.学费",
"n.郁金香",
"v.跌倒，摔跤，打滚",
"n.骚动，暴动，吵闹",
"n.金枪鱼",
"n.调子v.调谐",
"n.隧道，地道，坑道",
"n.汽轮机，涡轮机",
"adj.骚动的",
"]n.土耳其人",
"n.火鸡adj.n.土耳其",
"v.转向，旋转n.轮流",
"n.拐角adj.旋转的",
"n.萝卜",
"n.周转，营业额",
"n.海龟",
"n.辅导教师",
"num.第十二",
"num.十二",
"num.第二十",
"num.二十",
"adv.两次，两倍",
"n.细枝",
"n.黎明，黄昏，微亮",
"n.adj.孪生(的)",
"v.n.闪烁，眨眼",
"v.拧，扭，搓，歪曲",
"num.二",
"n.类型，典型v.打字",
"n.打字机",
"n.台风",
"adj.典型的",
"n.打字员",
"n.暴政，暴行",
"n.暴君，专制",
"n.轮胎",
"adj.丑恶的，丑陋的",
"n.溃疡",
"adj.最终的，极限的",
"adv.最后，终究",
"adj.上月的",
"adj.超声速的",
"adj.紫外的",
"n.伞，保护伞",
"adj.不能的，不会的",
"adj.不能接受的",
"adj.不青通融的",
"adj.买不起的",
"adj.一致的",
"adj.不可避免的",
"adj.不可忍受的",
"adj.不确定的，易变的",
"n.不定，易变",
"n.伯、叔、舅、姑父",
"adj.不舒服的",
"adj.罕见的，不常见的",
"adv.无条件地",
"adj.无知觉的",
"v.揭开",
"prep.在...下面",
"v.低估",
"v.经受，经历",
"n.本科生",
"adj.地下的，秘密的",
"v.在...下划线，强调",
"adj.根本的，在下面的",
"adj.下述的",
"v.破坏",
"prep.adv.在...下面",
"adj.在...下面签名的",
"n.了解，懂，熟悉",
"n.理解，谅解",
"v.从事，承担",
"n.事业，许诺",
"n.内衣",
"n.保险商，承购人",
"v.解开，取消",
"adv.无容置疑地",
"adj.过分的，不适当的",
"adv.过分地，不适当地",
"adj.不自在的，担心的",
"n.失业",
"adj.意外的，未料到的",
"adj.不公平的",
"adj.不合适的",
"v.展示，摊开",
"adj.不幸的，遗憾的",
"adv.不幸地，不凑巧",
"adj.不幸福的",
"adj.均匀的，统一的",
"adv.单调地，一样地",
"adj.不感兴趣的",
"n.联合，联盟，联合会",
"adj.唯一的",
"n.单位，个体",
"v.统一，联合，团结",
"adj.联合的",
"n.英国，联合王国",
"sn.联合国",
"sn.美国，合众国",
"n.统一，团结",
"adj.宇宙的，普遍的",
"adv.普遍地",
"n.宇宙",
"n.大学",
"adj.不公正的",
"adj.不仁慈的，冷酷的",
"adj.未知的n.未知物",
"adj.不合法的，违法的",
"prep.除非",
"adj.不同的",
"adj.未必的，不象的",
"adj.无限的",
"v.卸货，卸除",
"v.开启，揭开",
"adj.不幸的，倒霉的",
"adj.无销路的",
"adj.不必要的",
"adj.无法得到的",
"adj.未付的",
"adj.令人不愉快的",
"adj.前所未有的",
"adv.空前地",
"adj.不合理的，贵的",
"adj.不好销售的",
"adj.不令人满意的",
"adj.不稳定",
"adj.不适宜的",
"v.解开",
"prep.conj.到...为止",
"adj.无法使用的",
"adj.不寻常的",
"adj.无根据的",
"adj.不受欢迎的",
"adj.不愿意的",
"adj.行不通的",
"adv.向上，起床",
"n.(价格)上涨",
"v.支持，维持",
"prep.在...之上",
"adj.上部的，较高的",
"adj.直立的，正直的",
"n.喧闹，轰鸣",
"v.倾覆，打乱，使心烦",
"n.上面，上部",
"adj.颠倒的，倒置的",
"adv.在楼上，往楼上",
"adj.时新的，最近的",
"adv.adj.向上(的)",
"n.铀",
"adj.都市的，城市的",
"v.敦促，推动n.冲动",
"adj.紧迫的，紧急的",
"adv.紧急地",
"pron.我们(宾格)",
"n.使用，惯用法",
"v.使用n.用途，利用",
"adj.有用的，有益的",
"n.用处，有效性",
"adj.无用的",
"n.使用者，用户",
"adj.通常的，习惯性的",
"adv.通常，平常",
"n.用具，器皿",
"n.效用，公用事业",
"n.利用",
"v.利用",
"adj.最大的，最高的",
"v.说发声adj.完全的",
"n.说话",
"n.空缺，空位",
"adj.空的，闲置的",
"n.假期",
"v.接种疫苗",
"n.接种",
"n.真空",
"adj.含糊的，不清楚的",
"adj.徒然的，自负的",
"adv.徒劳地",
"n.坏蛋",
"adj.正当的，有效的",
"n.有效，确实",
"n.山谷",
"adj.宝贵的，有价值的",
"n.价值v.评价，估价",
"adj.宝贵的",
"n.阀门",
"n.小货车，面包车",
"v.消失，消散",
"n.虚荣心，浮华",
"n.水汽，蒸汽",
"adj.可变的n.变量",
"n.分歧，不一致",
"adj.不同的，不一致的",
"n.变化，变更",
"adj.不同的",
"n.多样(性)，品种",
"adj.各种各样的",
"n.清漆",
"v.变化，使多样化",
"n.花瓶",
"adj.巨大的，宏大的",
"n.拱顶",
"n.蔬菜，植物",
"n.运载工具",
"n.面纱，账，托辞",
"n.静脉，矿脉，脉",
"n.速度，速率",
"n.丝绒adj.柔软的",
"n.商贩",
"n.报复，复仇",
"v.换气，自由讨论",
"n.通风",
"n.v.冒险",
"n.金星",
"n.动词",
"adj.文字的，口头的",
"n.边缘，界限",
"n.检验",
"v.检验，证实",
"adj.多才多艺的",
"n.诗，韵文",
"n.译文，译本，看法",
"prep.对",
"adj.垂直的",
"adv.很，非常",
"n.船只，容器，血管",
"n.背心，汗衫",
"n.老手，老兵",
"v.n.否决(权)",
"v.使烦恼",
"prep.经由，取道",
"v.振动，战栗",
"n.振动，颤动",
"n.坏事，恶习",
"n.邻近，附近，接近",
"adj.邪恶的，不道德的",
"n.受害者",
"adj.胜利的，成功的",
"n.胜利",
"adj.电视的，视频的",
"n.视域，景色，见解",
"n.观察者，电视观众",
"n.观点，看法",
"n.活动，精力，元气",
"adj.精力旺盛的",
"n.别墅",
"n.村庄",
"n.坏蛋",
"n.藤，葡萄树",
"n.醋",
"v.违犯，违背",
"n.违犯，侵犯",
"n.猛烈，暴力，暴行",
"adj.猛烈的，暴力的",
"n.紫罗兰，紫色",
"n.小提琴",
"adj.处女的n.处女",
"adj.实质上的",
"adj.几乎，差不多",
"n.善，美德，优点",
"n.病毒",
"n.签证",
"adj.粘的",
"adj.看得见的",
"n.视觉，视力，想象力",
"v.n.访问，参观",
"n.客人，来宾，来访者",
"adj.视觉的",
"adj.必不可少的",
"n.维生素",
"adj.鲜艳的",
"adv.生动地",
"n.生动(性)",
"n.词汇，词汇表、量",
"n.职业",
"n.时尚，时髦",
"n.声音，嗓音v.吐露",
"adj.无声的",
"adj.空的，无效的",
"n.火山",
"n.v.齐射",
"n.排球",
"n.伏特",
"n.电压",
"n.卷，册，量，体积",
"adj.自愿的，志愿的",
"n.志愿者v.志愿",
"n.投票(权)，得票数",
"n.投票人，选举人",
"adj.有投票权的",
"v.担保",
"n.凭证，收据",
"v.n.许愿，发誓",
"n.元音",
"n.v.航行",
"adj.低级趣味的",
"n.易损性",
"adj.晚受损害的",
"v.消，跋涉",
"v.摇，摆",
"n.工资v.进行",
"n.货车",
"n.腰(部)",
"v.等候，伺候",
"n.服务员，侍者",
"n.女服务员",
"v.放弃(要求、权利)",
"v.醒来",
"v.唤醒，使觉醒",
"v.步行，走n.散步",
"n.步行者，散步者",
"n.墙壁",
"n.钱夹",
"n.核桃",
"v.徘徊，离题，迷失",
"v.想要，通辑n.缺乏",
"n.战争，斗争",
"n.病房，牢房",
"n.衣柜",
"n.货物",
"n.仓库，货栈",
"n.仓储",
"n.战争(状态)",
"adj.温暖的，热情的",
"adv.热烈地，热情地",
"n.温暖，暖和，热烈",
"v.警告，预先通知",
"n.警告",
"n.许可证，正当理由",
"adj.担保的",
"n.担保，保证",
"n.勇士，战士",
"n.军舰",
"v.洗，冲走",
"n.洗衣机",
"n.黄蜂，马蜂",
"v.浪费n.垃圾，废料",
"adj.浪费的，挥霍的",
"v.观看，看过n.手表",
"adj.注意的，警惕的",
"n.水v.浇水，垂涎",
"n.瀑布",
"n.水边，滩",
"adj.防水的",
"adj.不透水的",
"adj.水汪汪的，淡的",
"n.瓦特",
"n.波浪，波v.挥手",
"n.波长",
"n.晃动，动摇",
"adj.波浪状的",
"n.蜡v.打蜡",
"n.方法，路，方向",
"pron.我们",
"adj.弱的，差的",
"n.弱点，软弱",
"n.财富，丰富",
"adj.富裕的，富庶的",
"n.武器",
"v.穿，戴，磨损，耐久",
"adj.疲倦的",
"n.天气v.经受住",
"v.编织",
"n.织布工，编织者",
"n.网，蛛网，圈套",
"n.婚礼",
"n.楔子，起因v.楔住",
"n.星期三",
"n.杂草v.除草，清除",
"n.星期，周，工作周",
"n.工作日",
"n.周末",
"adj.每周的n.周刊",
"v.哭泣，哀悼",
"v.重...，称，权衡",
"n.重量，重担，重物",
"adj.受欢迎的v.欢迎",
"v.焊接",
"n.福利",
"n.井adv.好，充分",
"adj.有名的，著名的",
"n.西方adj.向西的",
"adj.西的，西方的",
"n.西方人，欧美人",
"adj.adv.向西(的)",
"adj.湿的，多雨的",
"n.鲸",
"n.捕鲸(业)",
"n.码头，停泊处",
"pron.什么adj.什么的",
"pron.无论什么",
"n.小麦",
"n.轮，车轮",
"adv.何时",
"conj.无论何时",
"adv.哪里",
"n.下落",
"conj.而，却",
"adv.借此",
"adv.在何处",
"adv.无论哪里",
"conj.是否，还是...",
"pron.adj.哪个，那个",
"pron.无论哪个",
"n.一会儿conj.当..时",
"conj.当...时，尽管",
"v.抽打，搅n.鞭子",
"v.n.旋转，飞转",
"n.络腮胡子",
"n.威士忌洒",
"v.n.耳语，发飒飒声",
"v.吹哨，鸣笛，啸叫",
"adj.白的n.白蛋清",
"v.粉刷，掩饰",
"pron.谁",
"pron.无论谁",
"adj.全部的n.全部",
"n.v.批发",
"n.批发商",
"n.批发",
"adj.卫生的",
"adv.完全，一概",
"pron.谁(宾格)",
"pron.谁的",
"adv.为什么",
"adj.坏的，不道德的",
"adj.宽的，广阔的",
"adv.广泛地，非常",
"v.加宽，扩大",
"adj.流传广泛的",
"n.寡妇",
"n.鳏夫",
"n.宽度",
"v.挥动，行使",
"n.妻子，夫人",
"adj.野生的，狂暴的",
"n.荒原",
"v.aux.将，愿n.意志",
"adj.乐意的，自愿的",
"adv.乐意地，自愿地",
"n.乐意，自愿",
"n.柳树",
"v.赢得，成功",
"n.风，风声v.绕",
"adj.弯曲的，蜿蜒的",
"n.风车",
"n.窗户",
"n.窗台",
"adj.刮风的",
"n.酒，葡萄酒",
"n.酿酒厂",
"n.翅膀，翼，派别",
"v.眨眼，使眼色",
"n.得胜者，获奖者",
"n.冬季",
"v.擦，抹掉",
"n.金属线，电线",
"adj.n.无线电",
"n.智慧，明智",
"adj.智慧的，博学的",
"v.希望，祝愿，想要",
"n.机智，才智",
"prep.同...一起，用",
"v.撤消，退出，提款",
"n.撤退，取款",
"v.枯萎，凋谢，衰弱",
"v.坚持",
"prep.adv.在...内",
"prep.没有，在...外部",
"v.抵挡，顶住",
"n.目击者证人v.目睹",
"adj.机智的，风趣的",
"n.悲痛，苦恼",
"n.狼",
"n.妇女，女人",
"v.想知道诧异n.奇迹",
"adj.奇妙的，精彩的",
"n.木，木材",
"adj.木制的",
"n.啄木鸟",
"n.树林",
"n.羊毛，毛线",
"adj.羊毛的，毛织的",
"n.字，词，诺言，音讯",
"n.措辞",
"adj.冗长的，罗嗦的",
"n.劳动，工作，作品",
"adj.可行的，起作用的",
"n.工人",
"n.工作者",
"n.工艺，手艺",
"n.工厂",
"n.车间，工场，学习班",
"n.世界，...界，世间",
"adj.adv.全世界的",
"n.蠕虫，幼虫",
"v.v.烦恼，担心",
"adj.更坏的，更差的",
"v.n.崇拜，礼拜",
"adj.最坏的，最差的",
"n.价值adj.值...的",
"adj.不值钱的",
"adj.值得做的",
"adj.值得的，配...的",
"v.受伤n.伤口，创伤",
"adj.受伤的n.伤员",
"v.包，裹",
"n.(饺子)皮，包装用品",
"n.暴怒",
"n.花圈，花环",
"v.毁坏n.失事",
"v.拧，扭伤n.扳手",
"v.n.摔交，搏斗",
"adj.可怜的，可耻的",
"v.拧，扭",
"n.皱纹v.折皱",
"n.腕",
"v.写，写信，写作",
"n.作者，作家",
"n.写作",
"adj.写作的，书面的",
"adj.错误的，有毛病的",
"adv.错误地，不正当地",
"n.v.复印",
"n.X射线v.X光检查",
"n.游船，快艇",
"n.码，庭院，场",
"v.n.打呵欠",
"n.年，年度",
"adj.adv.每年的",
"v.向往",
"n.酵母",
"v.n.叫嚷",
"n.adj.黄色(的)",
"adv.是，好",
"n.昨天adv.在昨天",
"adv.仍然，还，尚",
"v.生产，屈服n.产量",
"n.轭",
"n.蛋黄",
"pron.你，你们",
"adj.年轻的n.青年人",
"n.少年",
"pron.你的，你们的",
"pron.你(们)自己",
"n.青春，青年",
"adj.年轻的",
"n.热情，热忱",
"adj.热情的，热心的",
"n.斑马",
"n.零，零度",
"n.锌",
"n.活动，尖啸声",
"n.邮政编码",
"n.拉链",
"n.地带，区域，区",
"n.动物园",
"n.动物学"
};
